a1wolfe/iMX6-BareBones/Kicad/3D Models/SOT583_MP2182_MNP.step

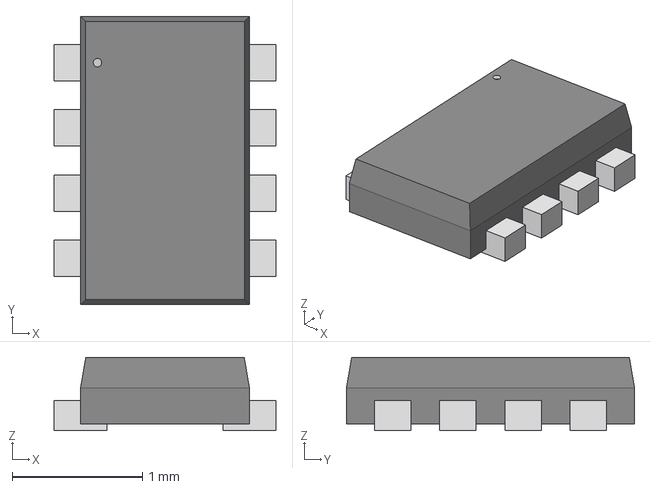
[picture p31: CAD file, 2026-04-11]
Kicad/3D Models/SOT583_MP2182_MNP.step
1.70 x 2.21 x 0.561 mm
