a1wolfe/iMX6-BareBones/Kicad/3D Models/P3V3_ind_74438322010.stp

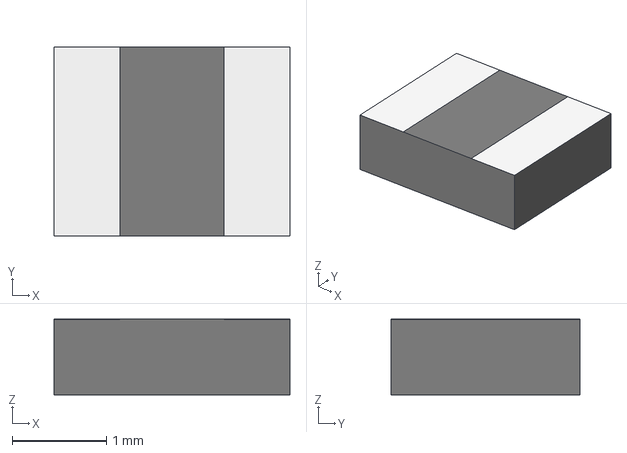
[picture p32: CAD file, 2026-04-11]
Kicad/3D Models/P3V3_ind_74438322010.stp
2.50 x 2.00 x 0.8 mm
