a1wolfe/iMX6-BareBones/Kicad/3D Models/5015.step

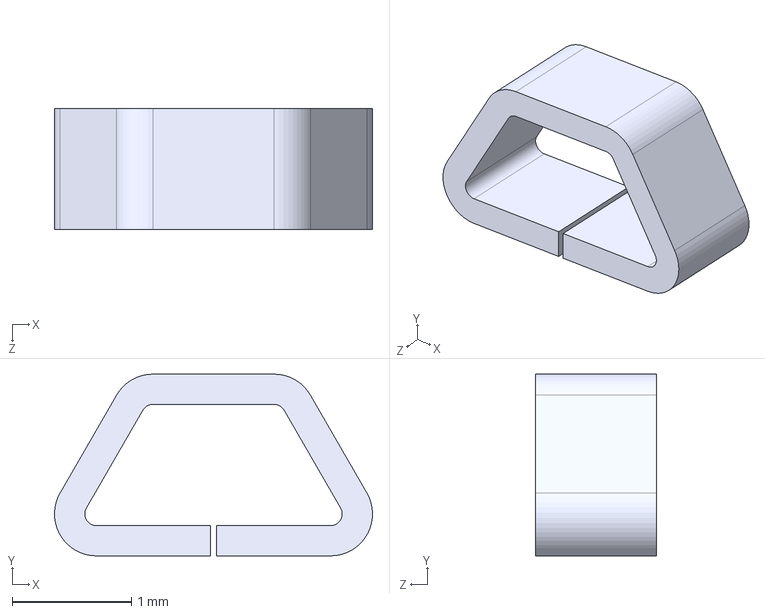
[picture p33: CAD file, 2026-04-11]
Kicad/3D Models/5015.step
2.67 x 1.52 x 1.02 mm
