a1wolfe/iMX6-BareBones/Kicad/3D Models/TPS3808E.stp

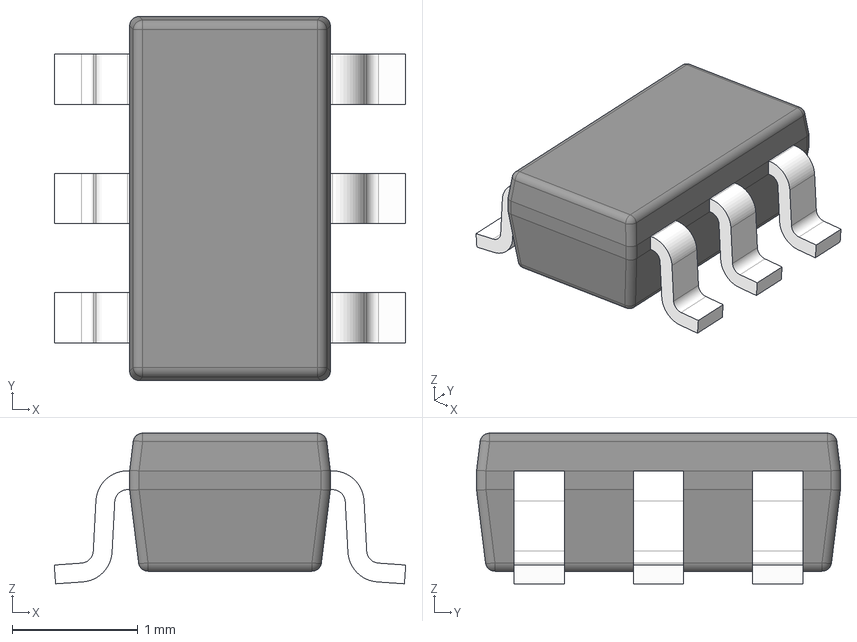
[picture p34: CAD file, 2026-04-11]
Kicad/3D Models/TPS3808E.stp
2.80 x 2.90 x 1.20 mm
BODY-SOT
LEAD-SOT x 6
