a1wolfe/iMX6-BareBones/Kicad/3D Models/PPPC042LFBN-RC.STEP

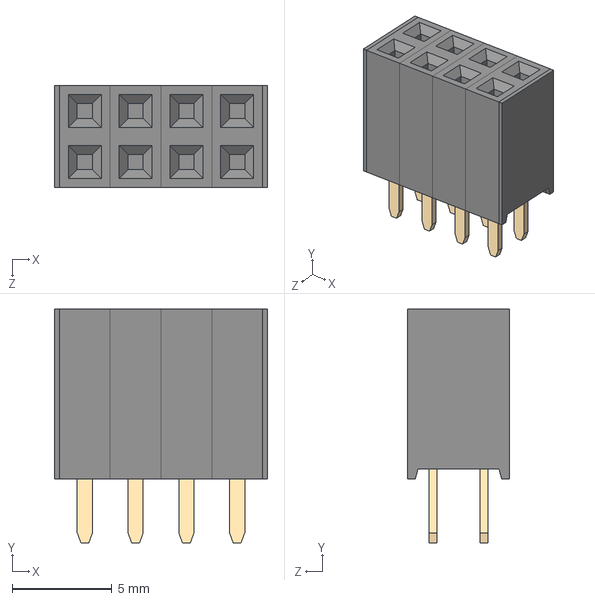
[picture p35: CAD file, 2026-04-11]
Kicad/3D Models/PPPC042LFBN-RC.STEP
10.7 x 11.7 x 5.08 mm
NPPC202LFBN-RC_C04
Pin - Gold x 4
