a1wolfe/iMX6-BareBones/Kicad/3D Models/QSPI-Flash_AT25SF321B-SSHB-T.stp

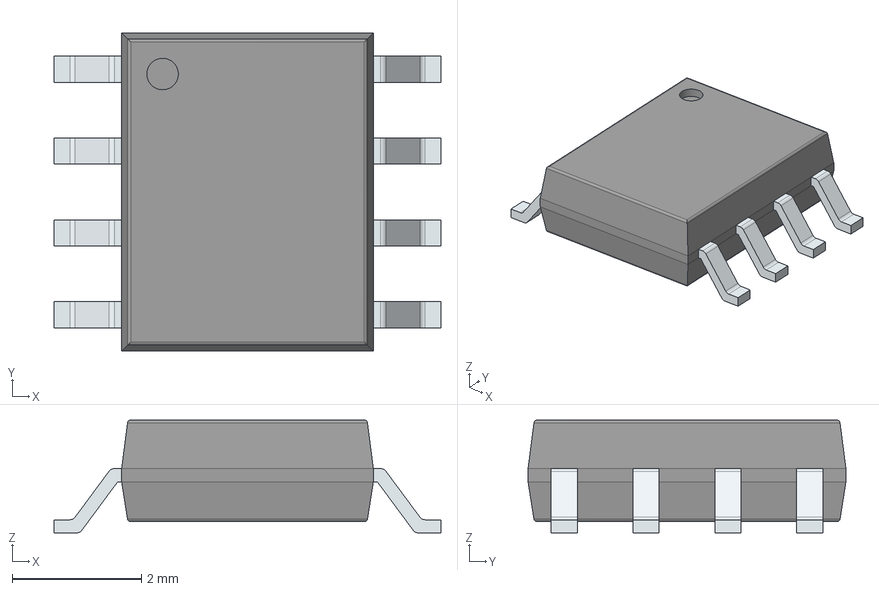
[picture p36: CAD file, 2026-04-11]
Kicad/3D Models/QSPI-Flash_AT25SF321B-SSHB-T.stp
6.00 x 4.92 x 1.75 mm
PinsArrayLR
