a1wolfe/iMX6-BareBones/Kicad/3D Models/_ _ _C122LFBN-RC.STEP

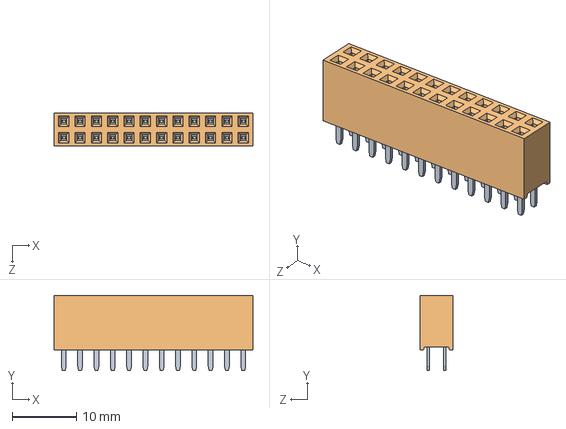
[picture p37: CAD file, 2026-04-11]
Kicad/3D Models/_ _ _C122LFBN-RC.STEP
31.0 x 11.7 x 5.08 mm
