a1wolfe/iMX6-BareBones/Kicad/3D Models/SP0503BAHTG.stp

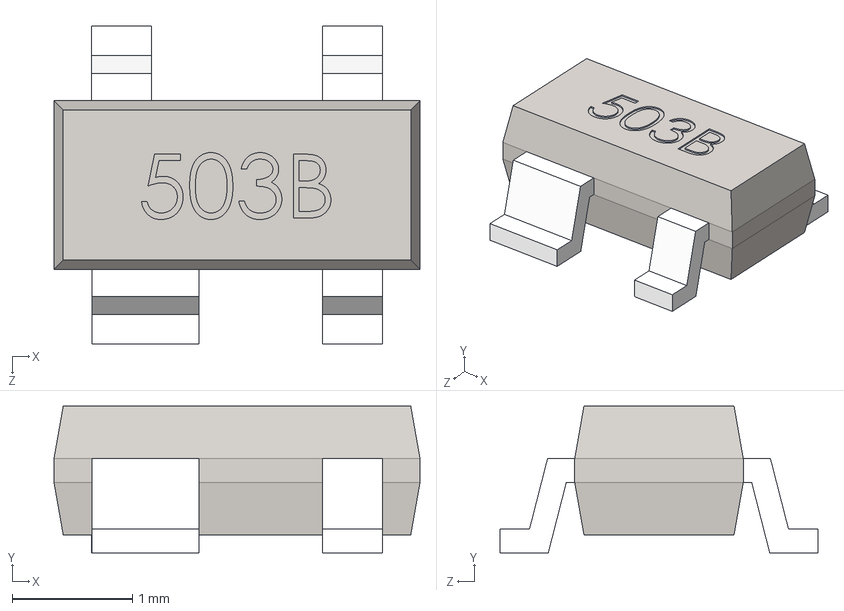
[picture p38: CAD file, 2026-04-11]
Kicad/3D Models/SP0503BAHTG.stp
3.04 x 1.22 x 2.64 mm
