a1wolfe/iMX6-BareBones/Kicad/3D Models/NCP380HMU05AATBG_LoadSwitch.stp

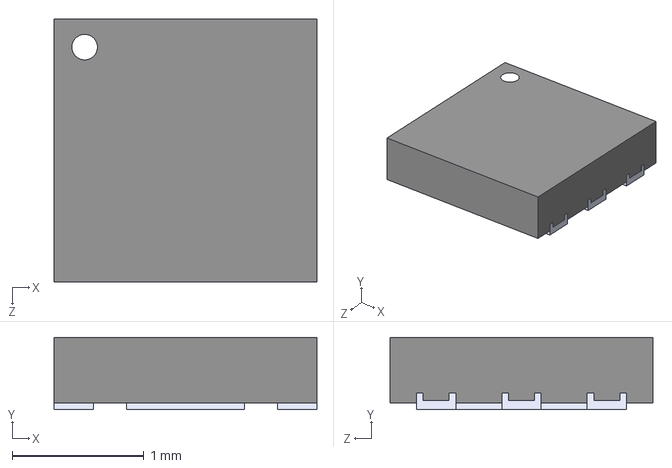
[picture p39: CAD file, 2026-04-11]
Kicad/3D Models/NCP380HMU05AATBG_LoadSwitch.stp
2.00 x 0.55 x 2.00 mm
