a1wolfe/iMX6-BareBones/Kicad/3D Models/MT41K256M16TW-107_P.step

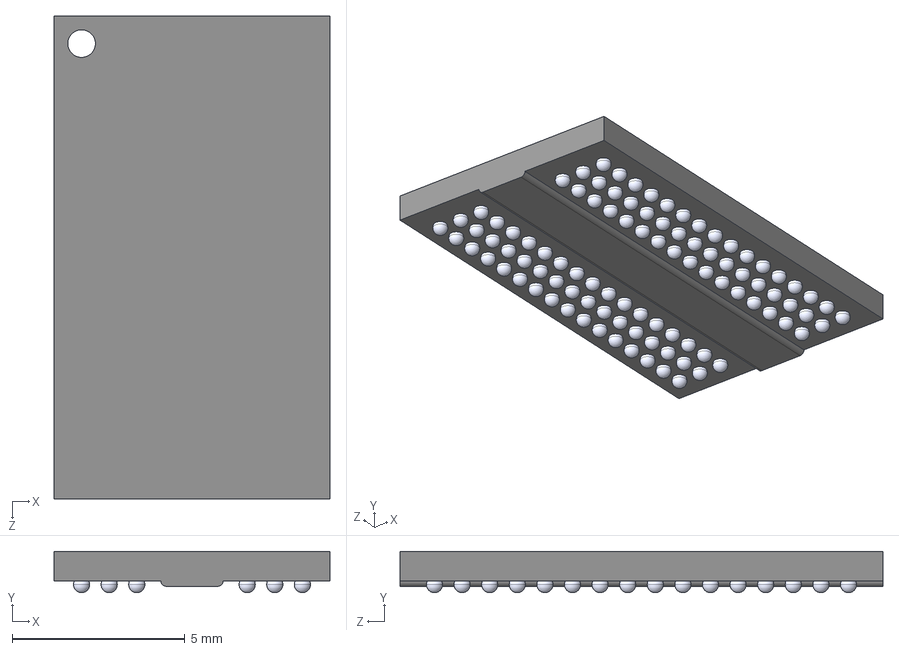
[picture p40: CAD file, 2026-04-11]
Kicad/3D Models/MT41K256M16TW-107_P.step
8.00 x 1.20 x 14.0 mm
