a1wolfe/iMX6-BareBones/Kicad/3D Models/TJA1042T_3.stp

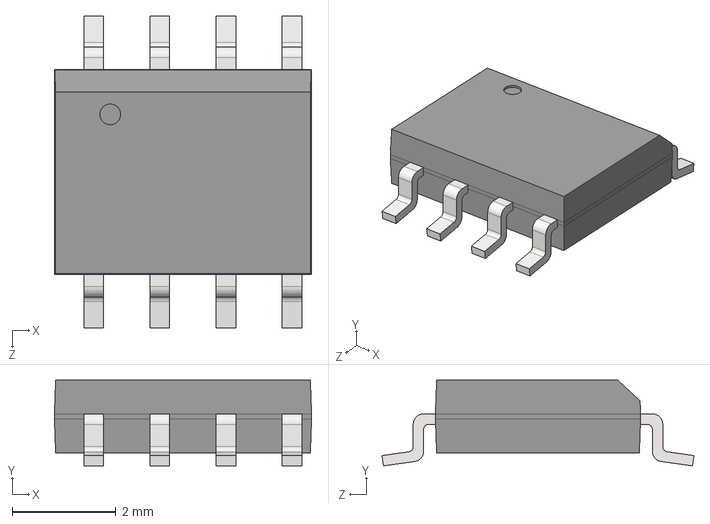
[picture p41: CAD file, 2026-04-11]
Kicad/3D Models/TJA1042T_3.stp
4.95 x 1.65 x 6.00 mm
