a1wolfe/iMX6-BareBones/Kicad/3D Models/APX803S-29SR-7.stp

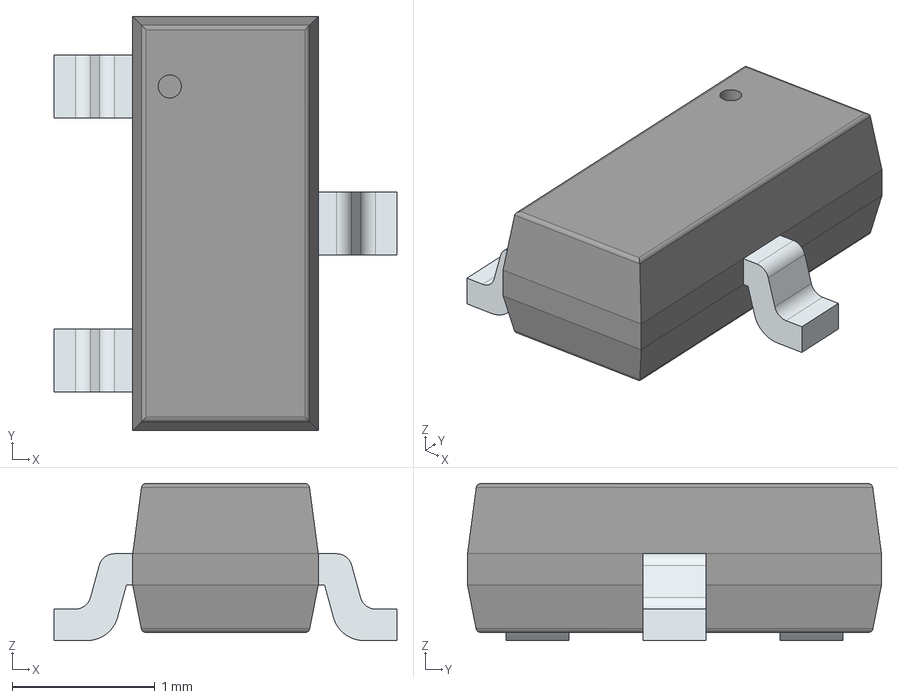
[picture p42: CAD file, 2026-04-11]
Kicad/3D Models/APX803S-29SR-7.stp
2.40 x 2.90 x 1.10 mm
PinsArrayL
FilletPinR
