a1wolfe/iMX6-BareBones/Kicad/3D Models/NX20P5090UK_awolfe.stp

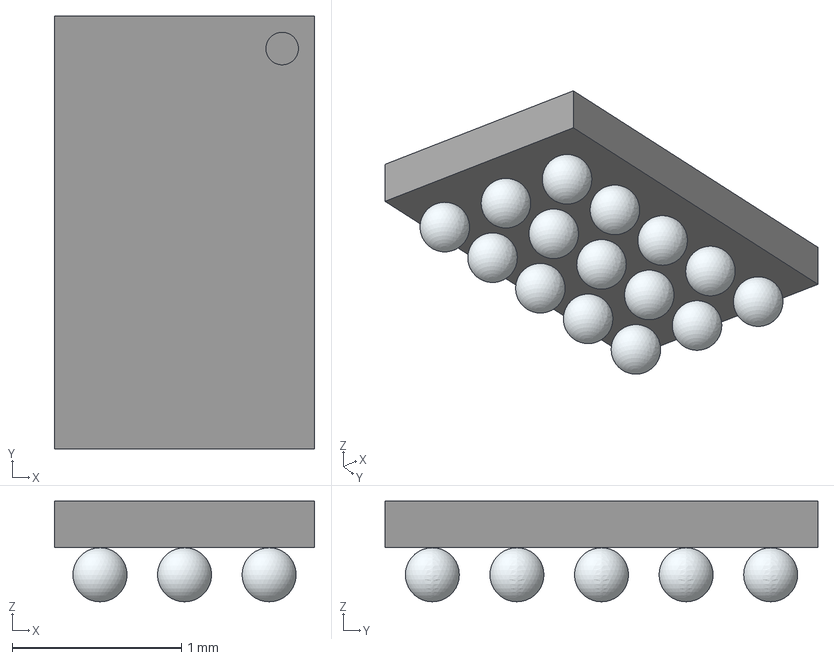
[picture p43: CAD file, 2026-04-11]
Kicad/3D Models/NX20P5090UK_awolfe.stp
1.54 x 2.56 x 0.595 mm
