a1wolfe/iMX6-BareBones/Kicad/3D Models/FC-135_32.7680KA-K0.stp

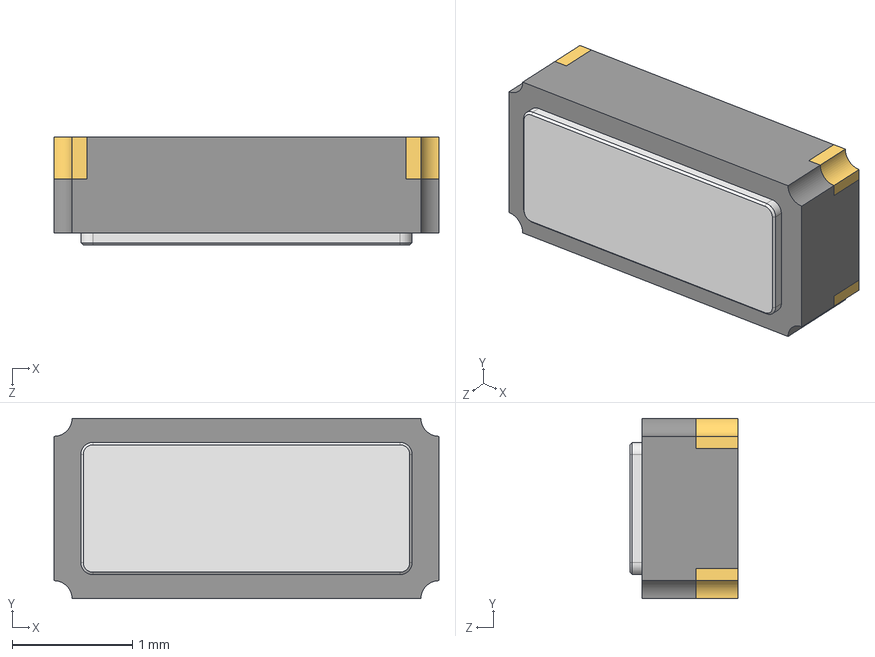
[picture p44: CAD file, 2026-04-11]
Kicad/3D Models/FC-135_32.7680KA-K0.stp
3.20 x 1.50 x 0.901 mm
