a1wolfe/iMX6-BareBones/Kicad/3D Models/MIC2025_MSOP-8_MM_MCH.step

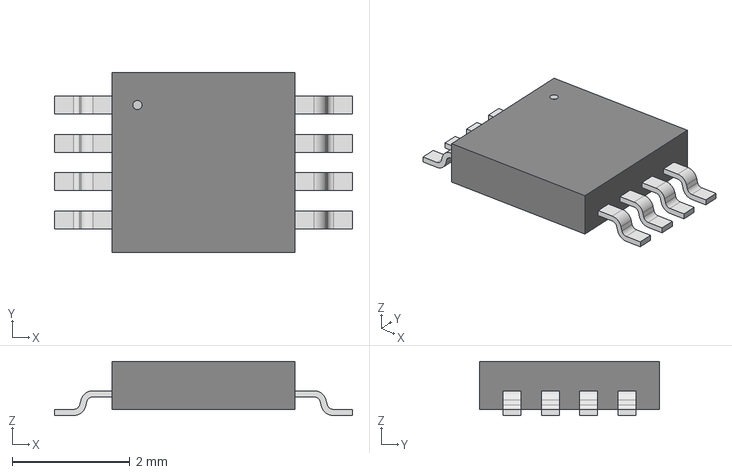
[picture p45: CAD file, 2026-04-11]
Kicad/3D Models/MIC2025_MSOP-8_MM_MCH.step
5.05 x 3.05 x 0.917 mm
