a1wolfe/iMX6-BareBones/Kicad/3D Models/eMMC_MX52LM04A11XSI.stp

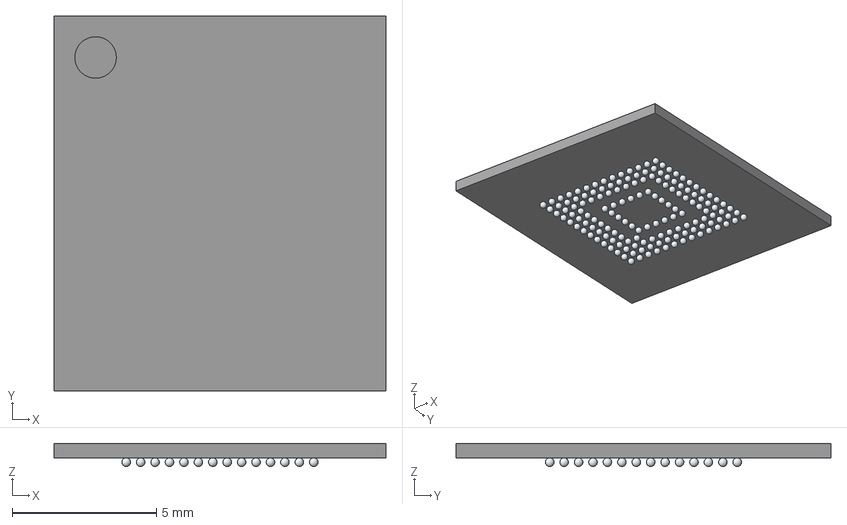
[picture p46: CAD file, 2026-04-11]
Kicad/3D Models/eMMC_MX52LM04A11XSI.stp
11.5 x 13.0 x 0.8 mm
A1
A2
A3
A4
A5
A6
A7
A8
A9
A10
A11
A12
A13
A14
B1
B2
B3
B4
B5
B6
B7
B8
B9
B10
B11
B12
B13
B14
C1
C2
C3
C4
C5
C6
C7
C8
C9
C10
C11
C12
C13
C14
D1
D2
D3
D4
D12
D13
D14
E1
E2
E3
E5
E6
E7
E8
E9
E10
E12
E13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
