a1wolfe/iMX6-BareBones/Kicad/3D Models/TLV773P_LDO_DBV0005A.stp

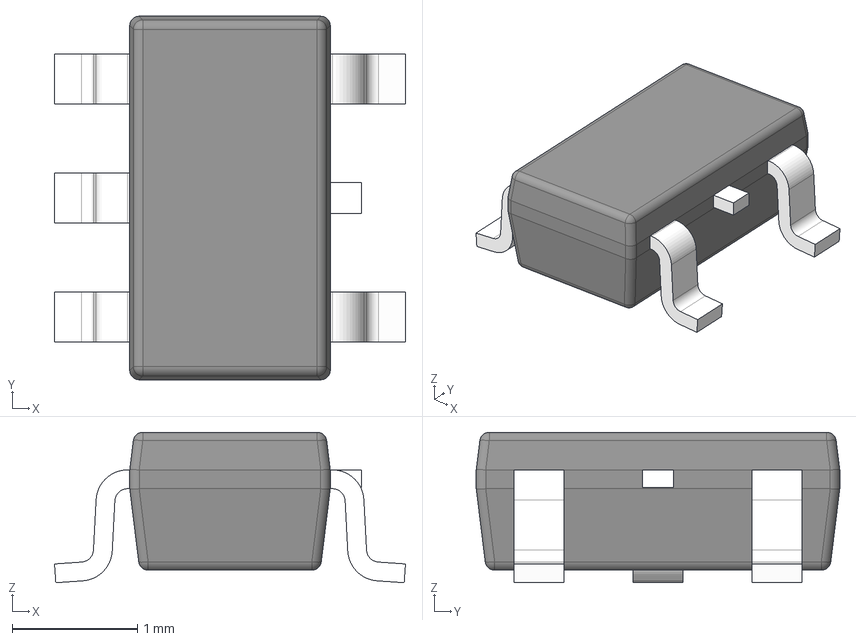
[picture p47: CAD file, 2026-04-11]
Kicad/3D Models/TLV773P_LDO_DBV0005A.stp
2.80 x 2.90 x 1.20 mm
BODY-SOT
LEAD-SOT x 5
LEAD-DUMMY
