a1wolfe/iMX6-BareBones/Kicad/3D Models/DualAnd_74LVC2G08GT_115.step

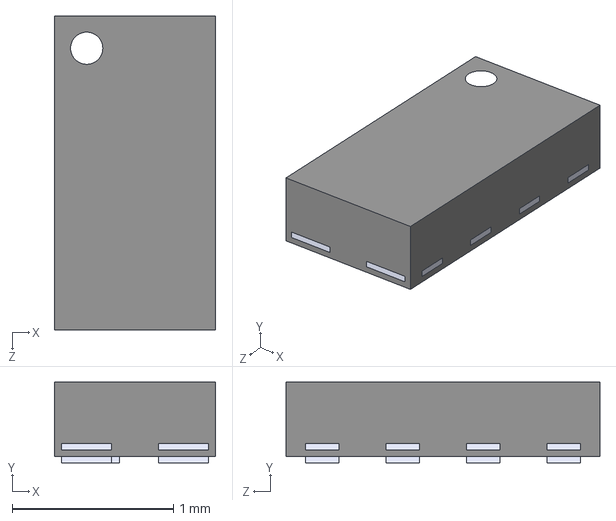
[picture p48: CAD file, 2026-04-11]
Kicad/3D Models/DualAnd_74LVC2G08GT_115.step
1.00 x 0.5 x 1.95 mm
