a1wolfe/iMX6-BareBones/Kicad/3D Models/USBArec_61400416021_rev1.stp

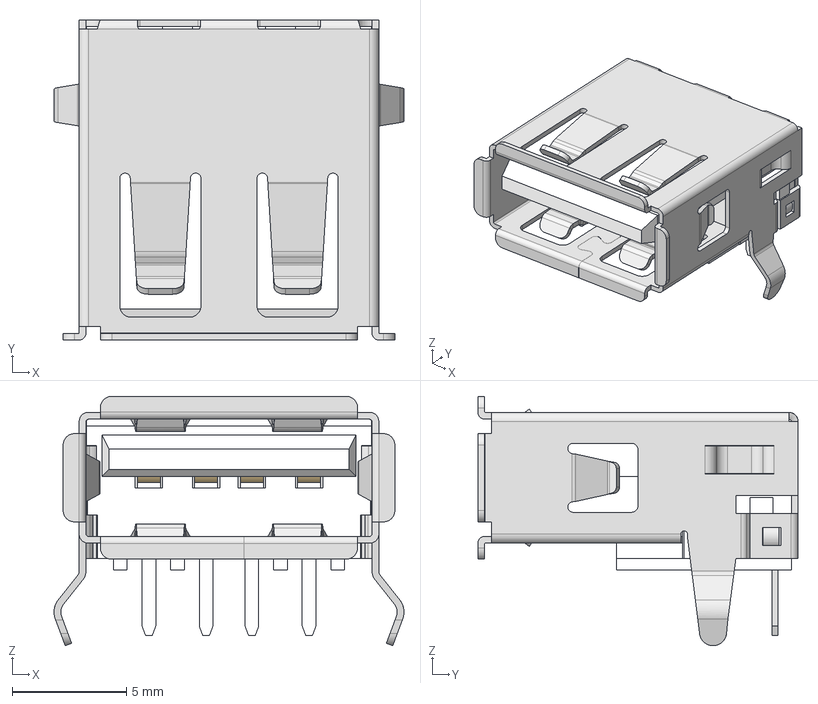
[picture p49: CAD file, 2026-04-11]
Kicad/3D Models/USBArec_61400416021_rev1.stp
15.3 x 14.0 x 10.9 mm
61400416021_Insulator
61400416021_Contact Plating x 4
61400416021_Shielding
