a1wolfe/iMX6-BareBones/Kicad/3D Models/LevelShift_DCU0008A.stp

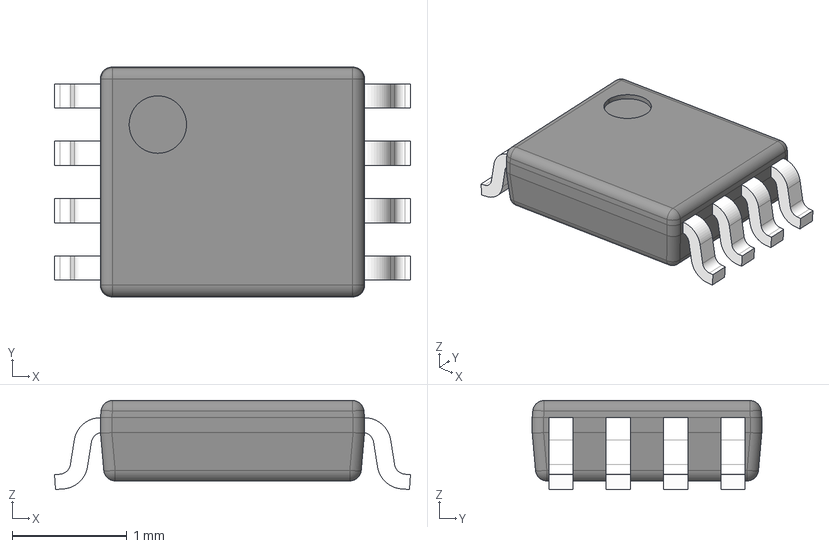
[picture p50: CAD file, 2026-04-11]
Kicad/3D Models/LevelShift_DCU0008A.stp
3.10 x 2.00 x 0.775 mm
BODY-VSSOP
LEAD-VSSOP x 8
