a1wolfe/iMX6-BareBones/Kicad/3D Models/218-4.STEP

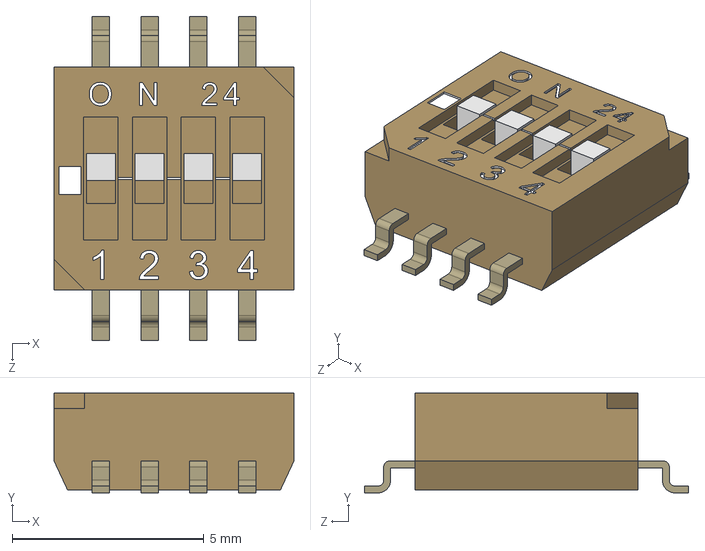
[picture p51: CAD file, 2026-04-11]
Kicad/3D Models/218-4.STEP
6.25 x 2.60 x 8.44 mm
