a1wolfe/iMX6-BareBones/Kicad/3D Models/DualNPN_MBT3904DW1T3G.stp

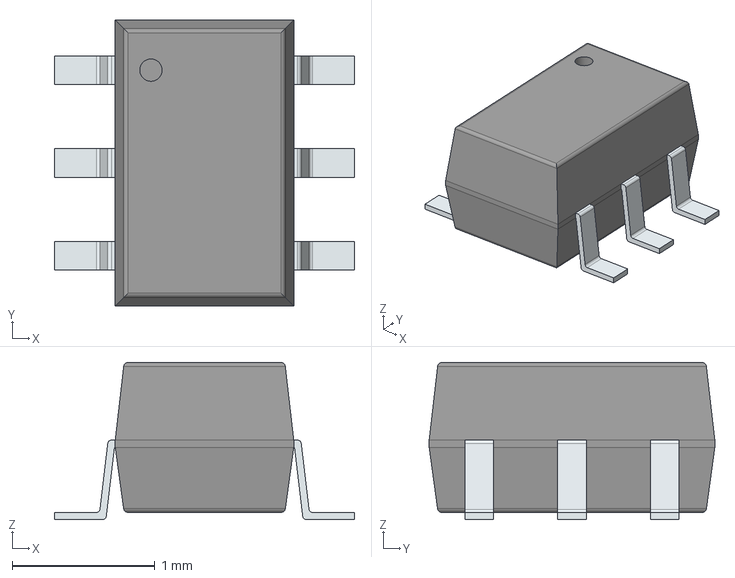
[picture p52: CAD file, 2026-04-11]
Kicad/3D Models/DualNPN_MBT3904DW1T3G.stp
2.10 x 2.00 x 1.10 mm
PinsArrayLR
