a1wolfe/iMX6-BareBones/Kicad/3D Models/USB-Tran_CP2102N-A02-GQFN20--3DModel-STEP-269445.STEP

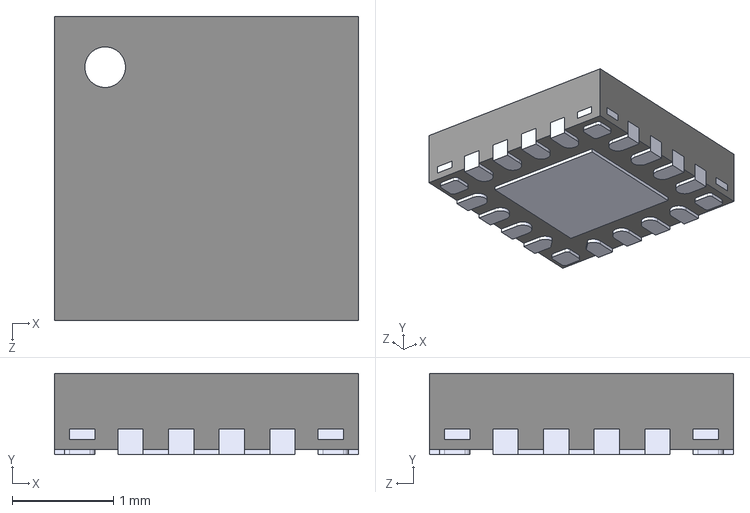
[picture p53: CAD file, 2026-04-11]
Kicad/3D Models/USB-Tran_CP2102N-A02-GQFN20--3DModel-STEP-269445.STEP
3.00 x 0.8 x 3.00 mm
