a1wolfe/iMX6-BareBones/Kicad/3D Models/PPPC102LFBN-RC.STEP

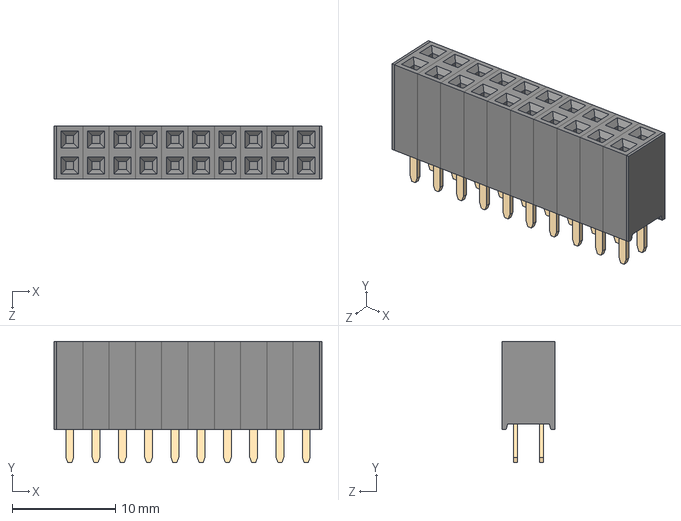
[picture p54: CAD file, 2026-04-11]
Kicad/3D Models/PPPC102LFBN-RC.STEP
25.9 x 11.7 x 5.08 mm
NPPC202LFBN-RC_C10
Pin - Gold x 10
