a1wolfe/iMX6-BareBones/Kicad/3D Models/WE-LHMI_4020+(rev1).stp

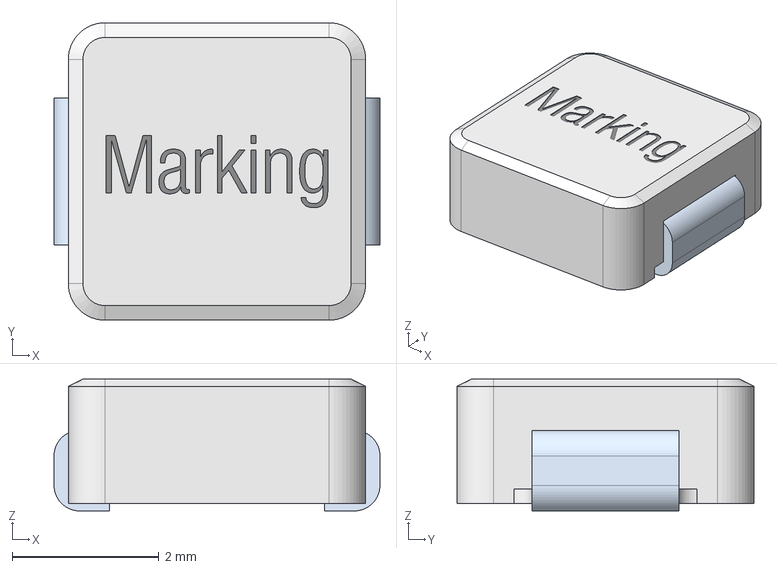
[picture p55: CAD file, 2026-04-11]
Kicad/3D Models/WE-LHMI_4020+(rev1).stp
4.45 x 4.06 x 1.80 mm
