a1wolfe/iMX6-BareBones/Kicad/3D Models/DLW43SH510XK2K--3DModel-STEP-1.STEP

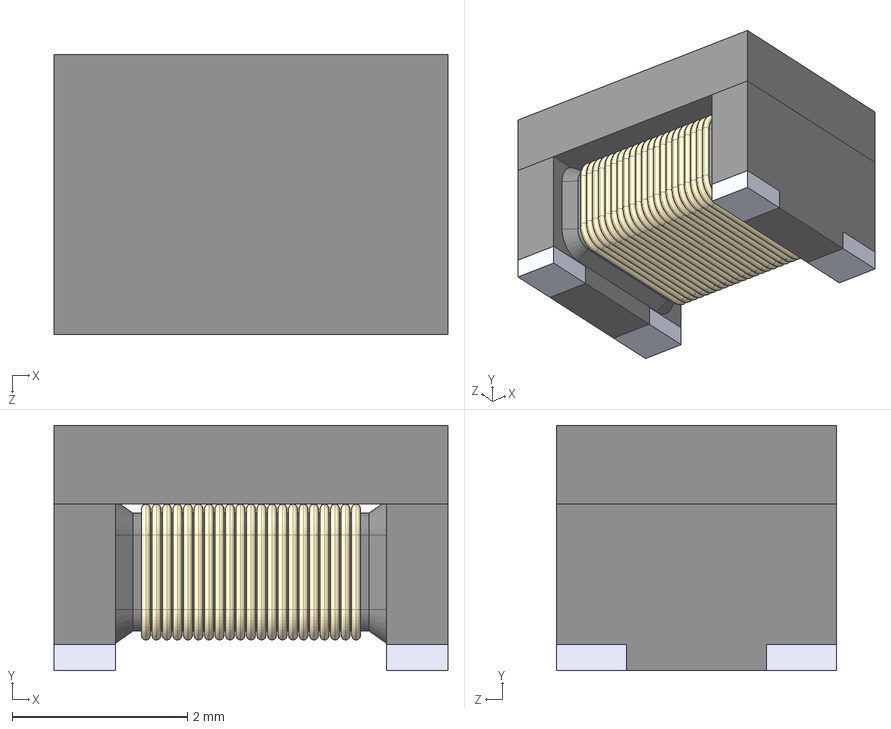
[picture p56: CAD file, 2026-04-11]
Kicad/3D Models/DLW43SH510XK2K--3DModel-STEP-1.STEP
4.50 x 2.80 x 3.20 mm
