a1wolfe/iMX6-BareBones/Kicad/3D Models/AP3401KTTR-G1.stp

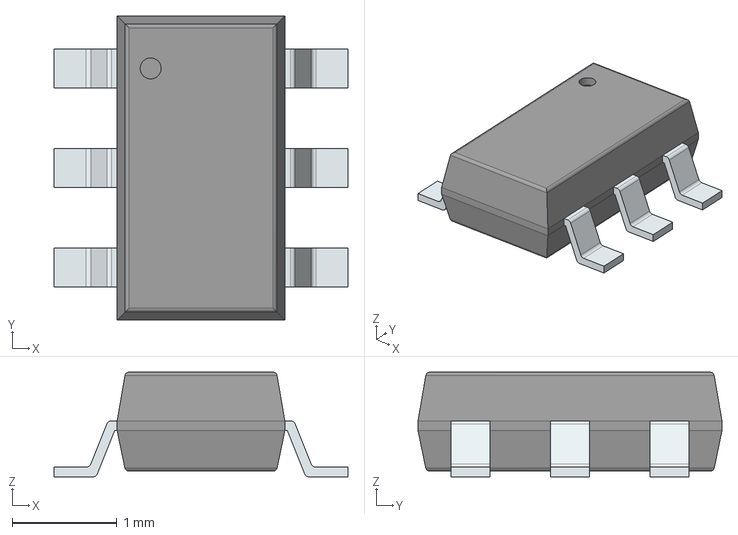
[picture p57: CAD file, 2026-04-11]
Kicad/3D Models/AP3401KTTR-G1.stp
2.80 x 2.90 x 1.00 mm
PinsArrayLR
