a1wolfe/iMX6-BareBones/Kicad/3D Models/sf-1206s-series.stp

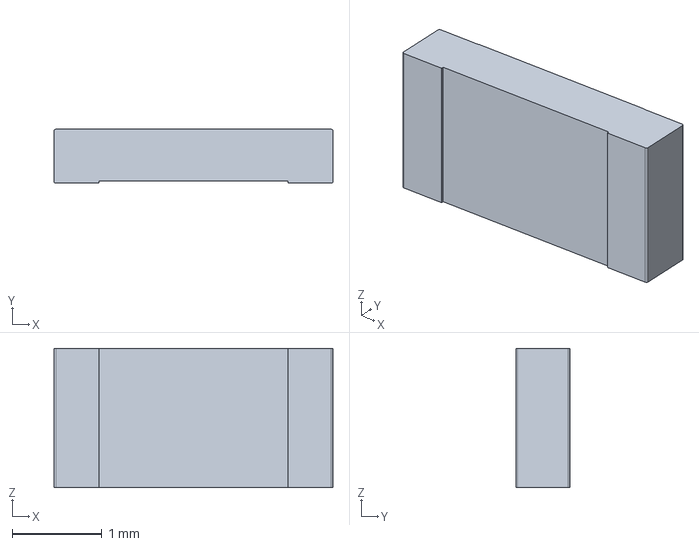
[picture p58: CAD file, 2026-04-11]
Kicad/3D Models/sf-1206s-series.stp
3.10 x 0.605 x 1.55 mm
