a1wolfe/iMX6-BareBones/Kicad/3D Models/DRL0006A_buck.stp

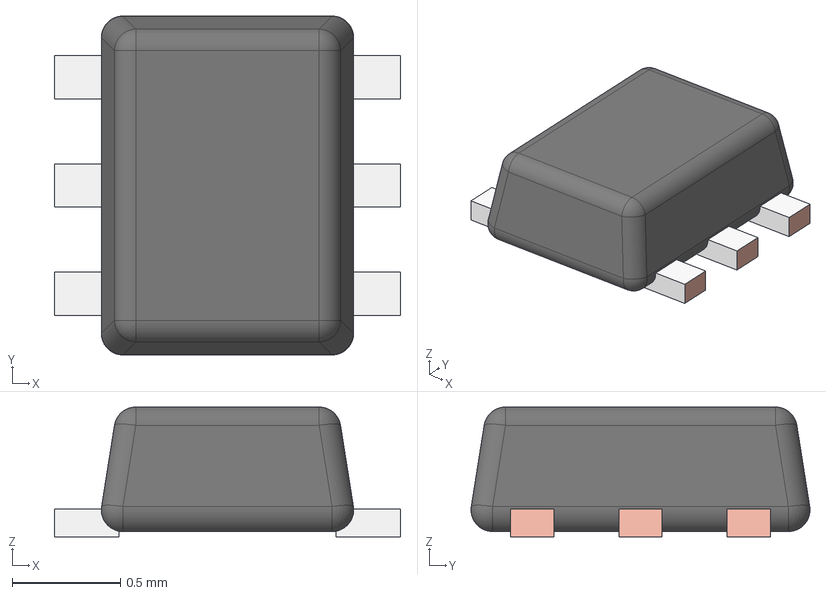
[picture p59: CAD file, 2026-04-11]
Kicad/3D Models/DRL0006A_buck.stp
1.60 x 1.57 x 0.6 mm
FRAME-DRL0006A
BODY-SOT
PIN1-ID
