a1wolfe/iMX6-BareBones/Kicad/3D Models/Kingbright_dualLED.step

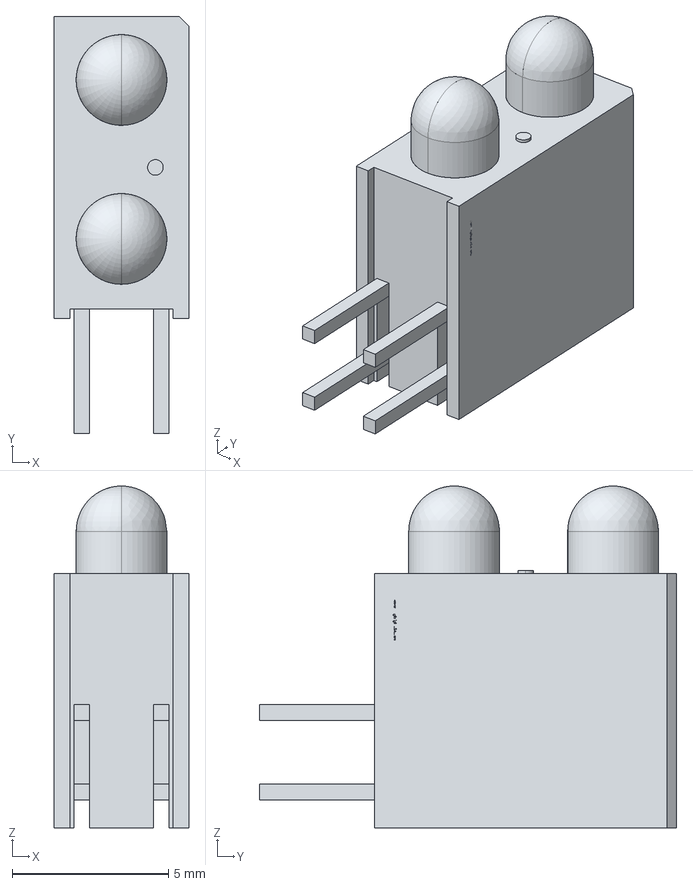
[picture p60: CAD file, 2026-04-11]
Kicad/3D Models/Kingbright_dualLED.step
4.30 x 13.3 x 10.9 mm
