a1wolfe/iMX6-BareBones/Kicad/BootMode.kicad_sch

## KiCad design Kicad/BootMode.kicad_sch (2026-04-23)

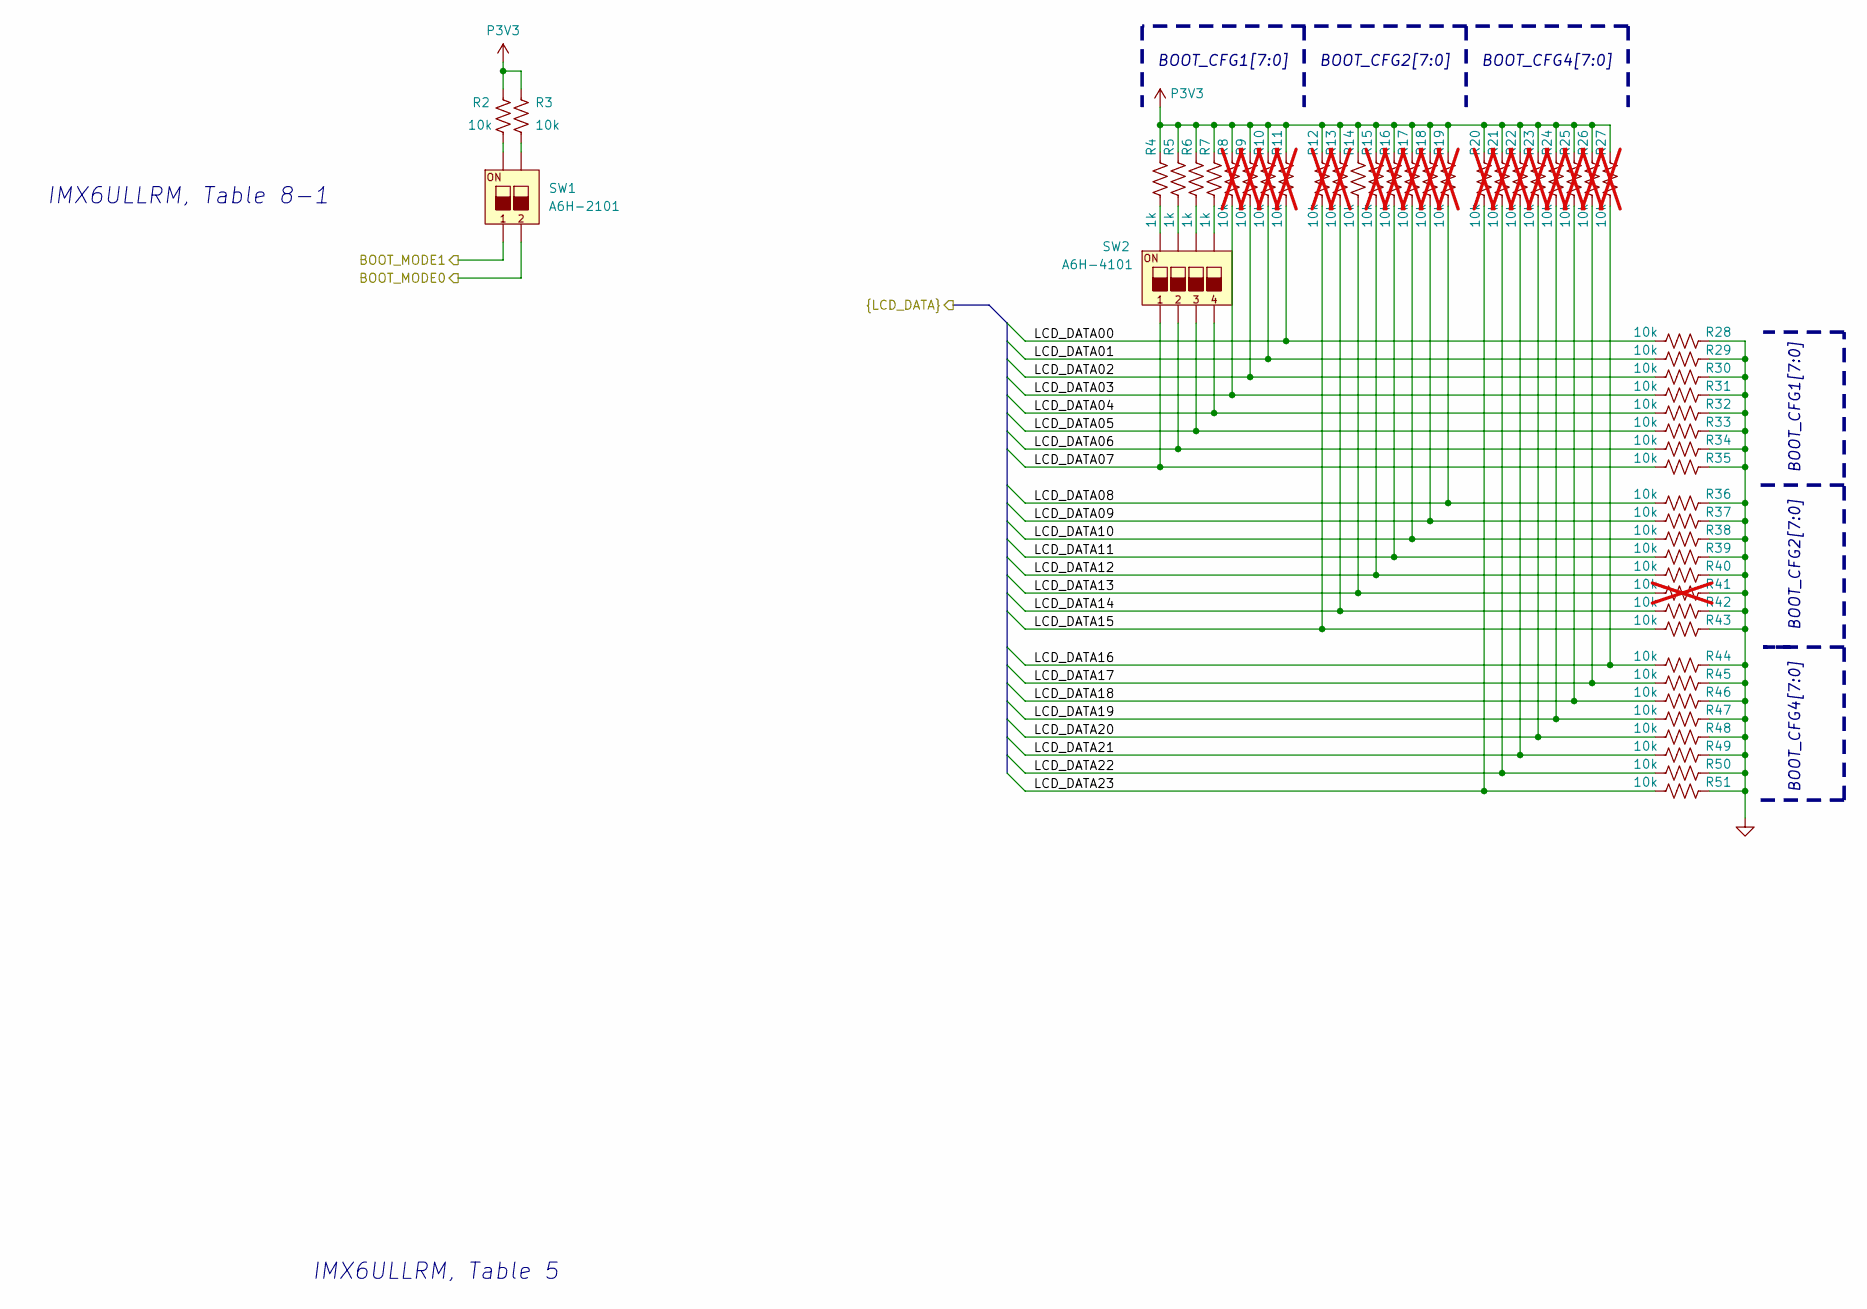
[picture p63: schematic BootMode.kicad_sch]

Parts:
R2, R3, R14, R28, R29, R30, R31, R32, R33, R34, R35, R36, R37, R38, R39, R40, R42, R43, R44, R45, R46, R47, R48, R49, R50, R51: 10k; R_0402_1005Metric; Tolerance 1%; MPN RC0402FR-7W10KL
R4, R5, R6, R7: 1k; R_0402_1005Metric; Tolerance 1%; MPN RC0402FR-7W1KL
R8, R9, R10, R11, R12, R13, R15, R16, R17, R18, R19, R20, R21, R22, R23, R24, R25, R26, R27, R41: 10k; R_0402_1005Metric; Tolerance 1%; MPN RC0402FR-7W10KL; not fitted
SW1: A6H-2101; SW_DIP_SPSTx02_Slide_Omron_A6H-2101_W6.15mm_P1.27mm; MPN A6H-2101
SW2: A6H-4101; SW_DIP_SPSTx04_Slide_Omron_A6H-4101_W6.15mm_P1.27mm; MPN A6H-4101

Connections:
BOOT_MODE0: SW1.2
BOOT_MODE1: SW1.1
GND: R28.1, R29.1, R30.1, R31.1, R32.1, R33.1, R34.1, R35.1, R36.1, R37.1, R38.1, R39.1, R40.1, R41.1, R42.1, R43.1, R44.1, R45.1, R46.1, R47.1, R48.1, R49.1, R50.1, R51.1
LCD_DATA00: R11.2, R28.2
LCD_DATA01: R10.2, R29.2
LCD_DATA02: R9.2, R30.2
LCD_DATA03: R8.2, R31.2
LCD_DATA04: R32.2, SW2.5
LCD_DATA05: R33.2, SW2.6
LCD_DATA06: R34.2, SW2.7
LCD_DATA07: R35.2, SW2.8
LCD_DATA08: R19.2, R36.2
LCD_DATA09: R18.2, R37.2
LCD_DATA10: R17.2, R38.2
LCD_DATA11: R16.2, R39.2
LCD_DATA12: R15.2, R40.2
LCD_DATA13: R14.2, R41.2
LCD_DATA14: R13.2, R42.2
LCD_DATA15: R12.2, R43.2
LCD_DATA16: R27.2, R44.2
LCD_DATA17: R26.2, R45.2
LCD_DATA18: R25.2, R46.2
LCD_DATA19: R24.2, R47.2
LCD_DATA20: R23.2, R48.2
LCD_DATA21: R22.2, R49.2
LCD_DATA22: R21.2, R50.2
LCD_DATA23: R20.2, R51.2
unnamed: R2.2, SW1.4
unnamed: R3.2, SW1.3
unnamed: R4.2, SW2.1
unnamed: R5.2, SW2.2
unnamed: R6.2, SW2.3
unnamed: R7.2, SW2.4
P3V3: R2.1, R3.1, R4.1, R5.1, R6.1, R7.1, R8.1, R9.1, R10.1, R11.1, R12.1, R13.1, R14.1, R15.1, R16.1, R17.1, R18.1, R19.1, R20.1, R21.1, R22.1, R23.1, R24.1, R25.1, R26.1, R27.1

Notes on the sheet:
BOOT_CFG2[7:0]
IMX6ULLRM, Table 8-1
BOOT_CFG4[7:0]
BOOT_CFG1[7:0]
IMX6ULLRM, Table 5
