a1wolfe/iMX6-BareBones/Kicad/CAN.kicad_sch

## KiCad design Kicad/CAN.kicad_sch (2026-04-23)

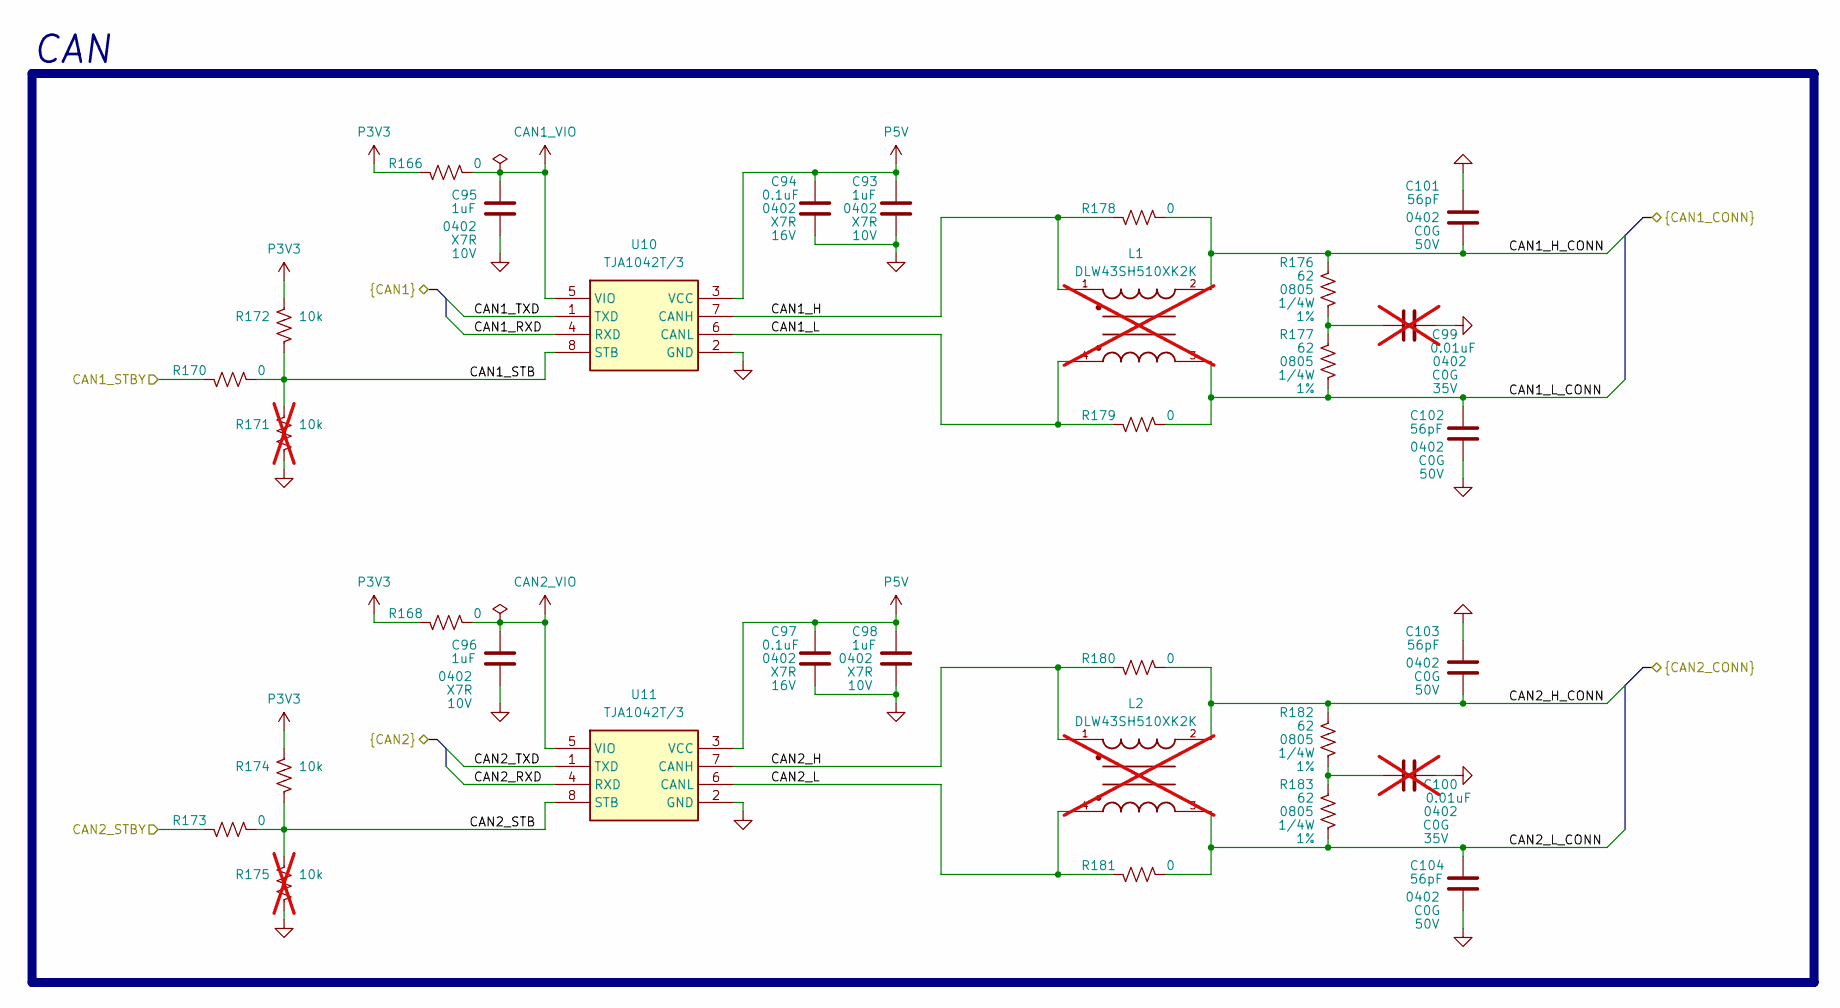
[picture p64: schematic CAN.kicad_sch]

Parts:
C93, C95, C96, C98: 1uF; C_0402_1005Metric; Tolerance 10%; Voltage 10V; MPN GRM155Z71A105KE01
C94, C97: 0.1uF; C_0402_1005Metric; Tolerance 10%; Voltage 16V; MPN GRM155R71C104KA88
C99, C100: 0.01uF; C_0402_1005Metric; Tolerance 2%; Voltage 35V; MPN GRM1555CYA103GE01; not fitted
C101, C102, C103, C104: 56pF; C_0402_1005Metric; Tolerance 5%; Voltage 50V; MPN GRM1555C1H560JA01
L1, L2: DLW43SH510XK2K; FIL_DLW43SH510XK2K; MPN DLW43SH510XK2K; not fitted
R166, R168, R170, R173, R178, R179, R180, R181: 0; R_0402_1005Metric; Tolerance Jumper; MPN RC0402JR-070RL
R171, R175: 10k; R_0402_1005Metric; Tolerance 1%; MPN RC0402FR-7W10KL; not fitted
R172, R174: 10k; R_0402_1005Metric; Tolerance 1%; MPN RC0402FR-7W10KL
R176, R177, R182, R183: 62; R_0805_2012Metric; Tolerance 1%; MPN RK73H2ATTD62R0F
U10, U11: TJA1042T/3; TJA1042T_SOIC127P600X175-8N; Manufacturer_Part_Number TJA1042T/3; Mouser Part Number N/A

Connections:
CAN1_H: L1.1, R178.1, U10.7 (CANH)
CAN1_H_CONN: C101.1, L1.2, R176.2, R178.2
CAN1_L: L1.4, R179.1, U10.6 (CANL)
CAN1_L_CONN: C102.1, L1.3, R177.1, R179.2
CAN1_RXD: U10.4 (RXD)
CAN1_STB: R170.2, R171.2, R172.1, U10.8 (STB)
CAN1_STBY: R170.1
CAN1_TXD: U10.1 (TXD)
CAN1_VIO: C95.1, R166.2, U10.5 (VIO)
CAN2_H: L2.1, R180.1, U11.7 (CANH)
CAN2_H_CONN: C103.1, L2.2, R180.2, R182.2
CAN2_L: L2.4, R181.1, U11.6 (CANL)
CAN2_L_CONN: C104.1, L2.3, R181.2, R183.1
CAN2_RXD: U11.4 (RXD)
CAN2_STB: R173.2, R174.1, R175.2, U11.8 (STB)
CAN2_STBY: R173.1
CAN2_TXD: U11.1 (TXD)
CAN2_VIO: C96.1, R168.2, U11.5 (VIO)
GND: C93.2, C94.2, C95.2, C96.2, C97.2, C98.2, C99.2, C100.2, C101.2, C102.2, C103.2, C104.2, R171.1, R175.1, U10.2 (GND), U11.2 (GND)
unnamed: C99.1, R176.1, R177.2
unnamed: C100.1, R182.1, R183.2
P3V3: R166.1, R168.1, R172.2, R174.2
P5V: C93.1, C94.1, C97.1, C98.1, U10.3 (VCC), U11.3 (VCC)

Notes on the sheet:
CAN
