a1wolfe/iMX6-BareBones/Kicad/Connectors.kicad_sch

## KiCad design Kicad/Connectors.kicad_sch (2026-04-23)

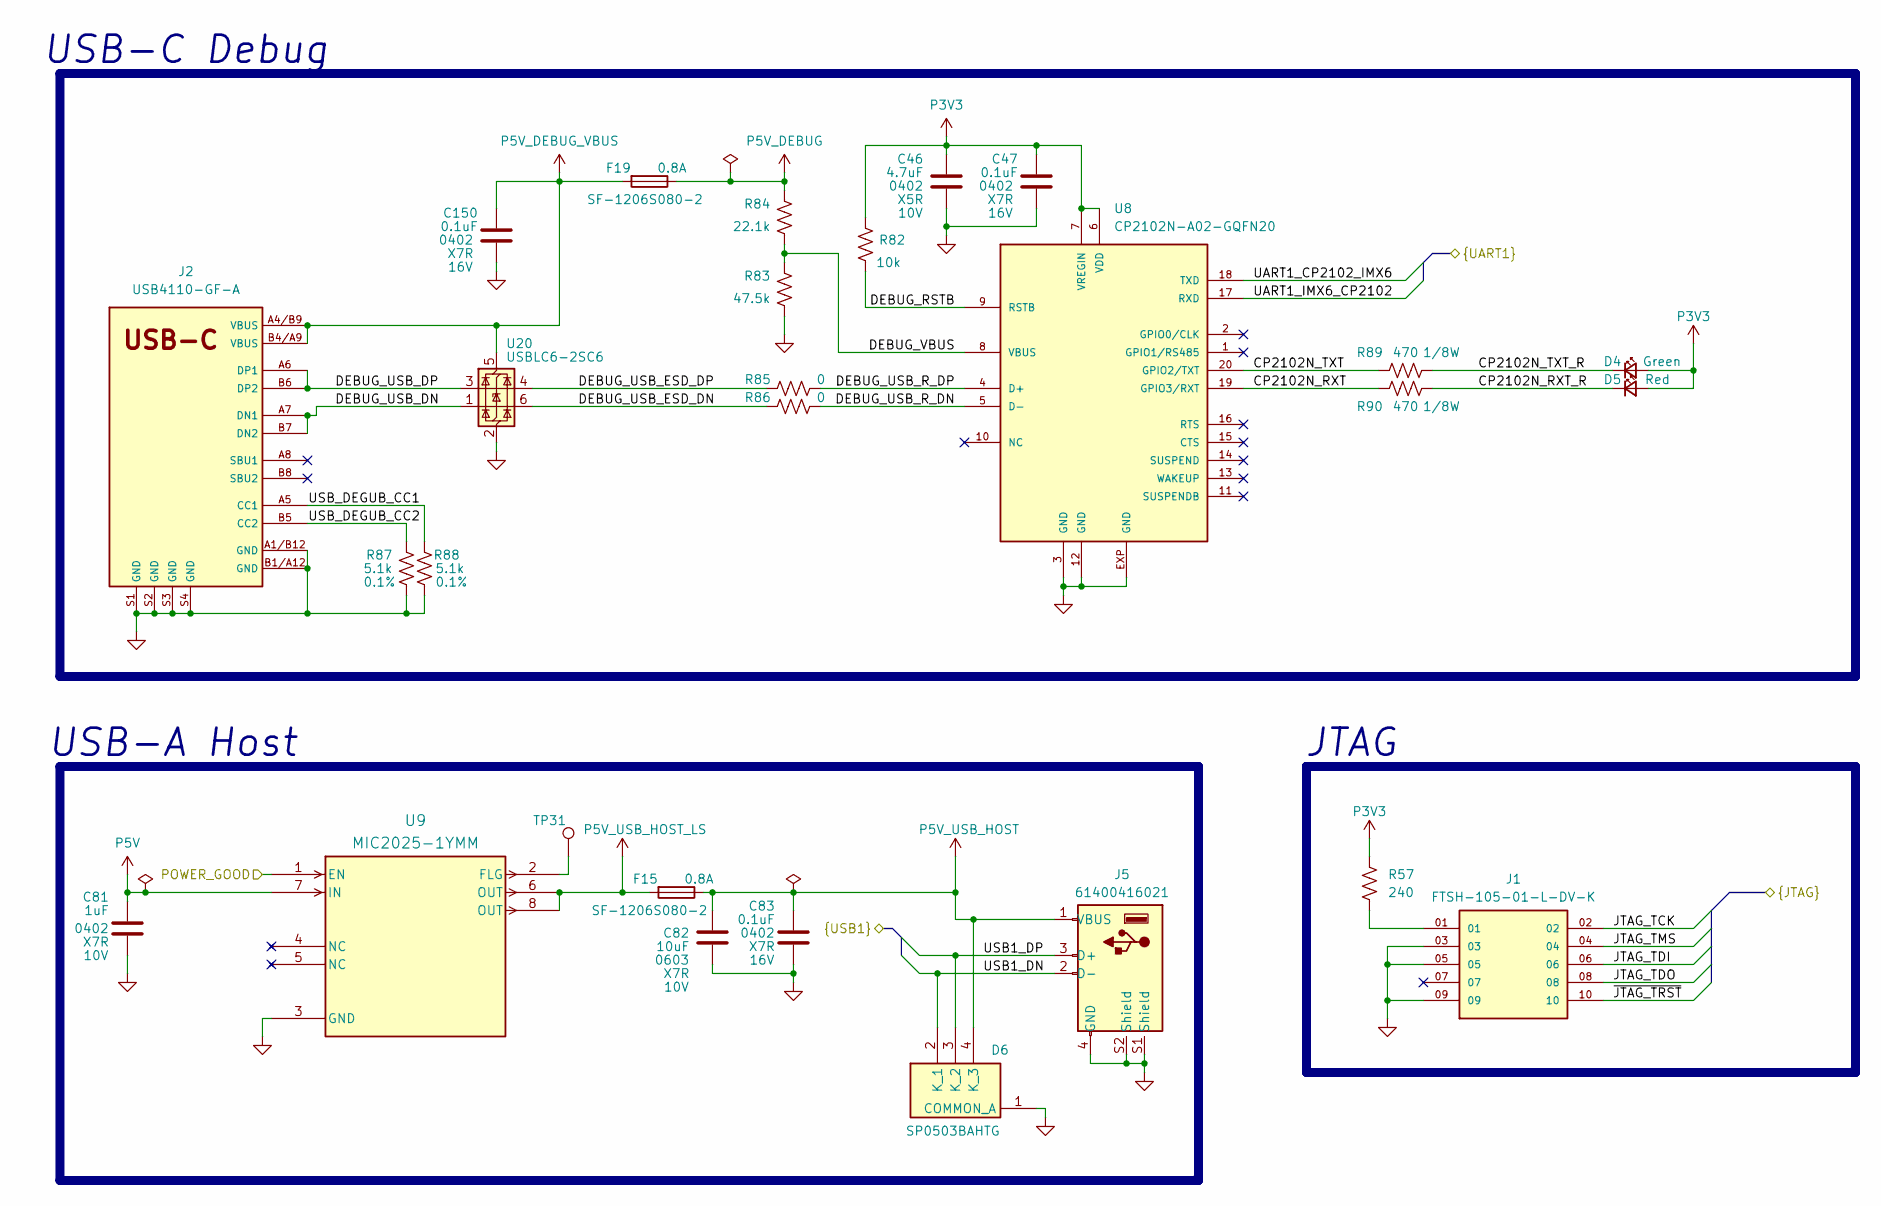
[picture p65: schematic Connectors.kicad_sch]

Parts:
C46: 4.7uF; C_0402_1005Metric; Tolerance 20%; Voltage 10V; MPN GRM155R61A475MEA
C47, C83, C150: 0.1uF; C_0402_1005Metric; Tolerance 10%; Voltage 16V; MPN GRM155R71C104KA88
C81: 1uF; C_0402_1005Metric; Tolerance 10%; Voltage 10V; MPN GRM155Z71A105KE01
C82: 10uF; C_0603_1608Metric; Tolerance 10%; Voltage 10V; MPN GRM188Z71A106KA73
D4: LTST-C170GKT; LED_0805_2012Metric; MPN LTST-C170GKT
D5: LTST-C170KRKT; LED_0805_2012Metric; MPN LTST-C170KRKT
D6: SP0503BAHTG; Manufacturer_Part_Number SP0503BAHTG; Mouser Part Number 576-SP0503BAHTG
F15, F19: SF-1206S080-2; Fuse_1206_3216Metric; Current Rating 0.8A; MPN SF-1206S080-2
J1: FTSH-105-01-L-DV-K; SAMTEC_FTSH-105-XX-X-DV; PARTREV H
J2: USB4110-GF-A; GCT_USB4110GFA; MPN USB4110-GF-A
J5: 61400416021; USBArec_61400416021; MPN 61400416021
R57: 240; R_0402_1005Metric; Tolerance 0.1%; MPN RT0402BRD07240RL
R82: 10k; R_0402_1005Metric; Tolerance 1%; MPN RC0402FR-7W10KL
R83: 47.5k; R_0402_1005Metric; Tolerance 1%; MPN RC0402FR-0747K5L
R84: 22.1k; R_0402_1005Metric; Tolerance 1%; MPN RC0402FR-0722K1L
R85, R86: 0; R_0402_1005Metric; Tolerance Jumper; MPN RC0402JR-070RL
R87, R88: 5.1k; R_0402_1005Metric; Tolerance 0.1%; MPN RT0402BRD075K1L
R89, R90: 470; R_0402_1005Metric; Tolerance 1%; MPN RCC0402470RFKED
TP31: TestPoint; TestPoint_Pad_D30mil
U8: CP2102N-A02-GQFN20; CP2102N_WFQFN-20; MPN CP2102N-A02-GQFN20
U9: MIC2025-1YMM; MIC2025_MSOP-8_MM_MCH; MPN MIC2025-1YMM
U20: USBLC6-2SC6

Connections:
CP2102N_RXT: R90.2, U8.19 (GPIO3/RXT)
CP2102N_RXT_R: D5.1 (K), R90.1
CP2102N_TXT: R89.2, U8.20 (GPIO2/TXT)
CP2102N_TXT_R: D4.1 (K), R89.1
DEBUG_RSTB: R82.1, U8.9 (RSTB)
DEBUG_USB_DN: J2.A7 (DN1), J2.B7 (DN2), U20.1 (I/O2)
DEBUG_USB_DP: J2.A6 (DP1), J2.B6 (DP2), U20.3 (I/O1)
DEBUG_USB_ESD_DN: R86.2, U20.6 (I/O2)
DEBUG_USB_ESD_DP: R85.2, U20.4 (I/O1)
DEBUG_USB_R_DN: R86.1, U8.5 (D-)
DEBUG_USB_R_DP: R85.1, U8.4 (D+)
DEBUG_VBUS: R83.2, R84.1, U8.8 (VBUS)
GND: C46.1, C47.1, C81.1, C82.1, C83.1, C150.1, D6.1 (COMMON_A), J1.03, J1.05, J1.09, J2.A1/B12 (GND), J2.B1/A12 (GND), J2.S1 (GND), J2.S2 (GND), J2.S3 (GND), J2.S4 (GND), J5.4 (GND), J5.S1 (Shield), J5.S2 (Shield), R83.1, R87.1, R88.1, U8.3 (GND), U8.12 (GND), U8.EXP (GND), U9.3 (GND), U20.2 (GND)
JTAG_TCK: J1.02
JTAG_TDI: J1.06
JTAG_TDO: J1.08
JTAG_TMS: J1.04
unnamed: J1.01, R57.2
unnamed: TP31.1, U9.2 (FLG)
P3V3: C46.2, C47.2, D4.2 (A), D5.2 (A), R57.1, R82.2, U8.6 (VDD), U8.7 (VREGIN)
P5V: C81.2, U9.7 (IN)
P5V_DEBUG: F19.1, R84.2
P5V_DEBUG_VBUS: C150.2, F19.2, J2.A4/B9 (VBUS), J2.B4/A9 (VBUS), U20.5 (VBUS)
P5V_USB_HOST: C82.2, C83.2, D6.4 (K_3), F15.1, J5.1 (VBUS)
P5V_USB_HOST_LS: F15.2, U9.6 (OUT), U9.8 (OUT)
POWER_GOOD: U9.1 (EN)
UART1_CP2102_IMX6: U8.18 (TXD)
UART1_IMX6_CP2102: U8.17 (RXD)
USB1_DN: D6.2 (K_1), J5.2 (D-)
USB1_DP: D6.3 (K_2), J5.3 (D+)
USB_DEGUB_CC1: J2.A5 (CC1), R88.2
USB_DEGUB_CC2: J2.B5 (CC2), R87.2
~JTAG_TRST: J1.10

Notes on the sheet:
USB-A Host
USB-C Debug
JTAG
