a1wolfe/iMX6-BareBones/Kicad/DRAM_DDR3L.kicad_sch

## KiCad design Kicad/DRAM_DDR3L.kicad_sch (2026-04-23)

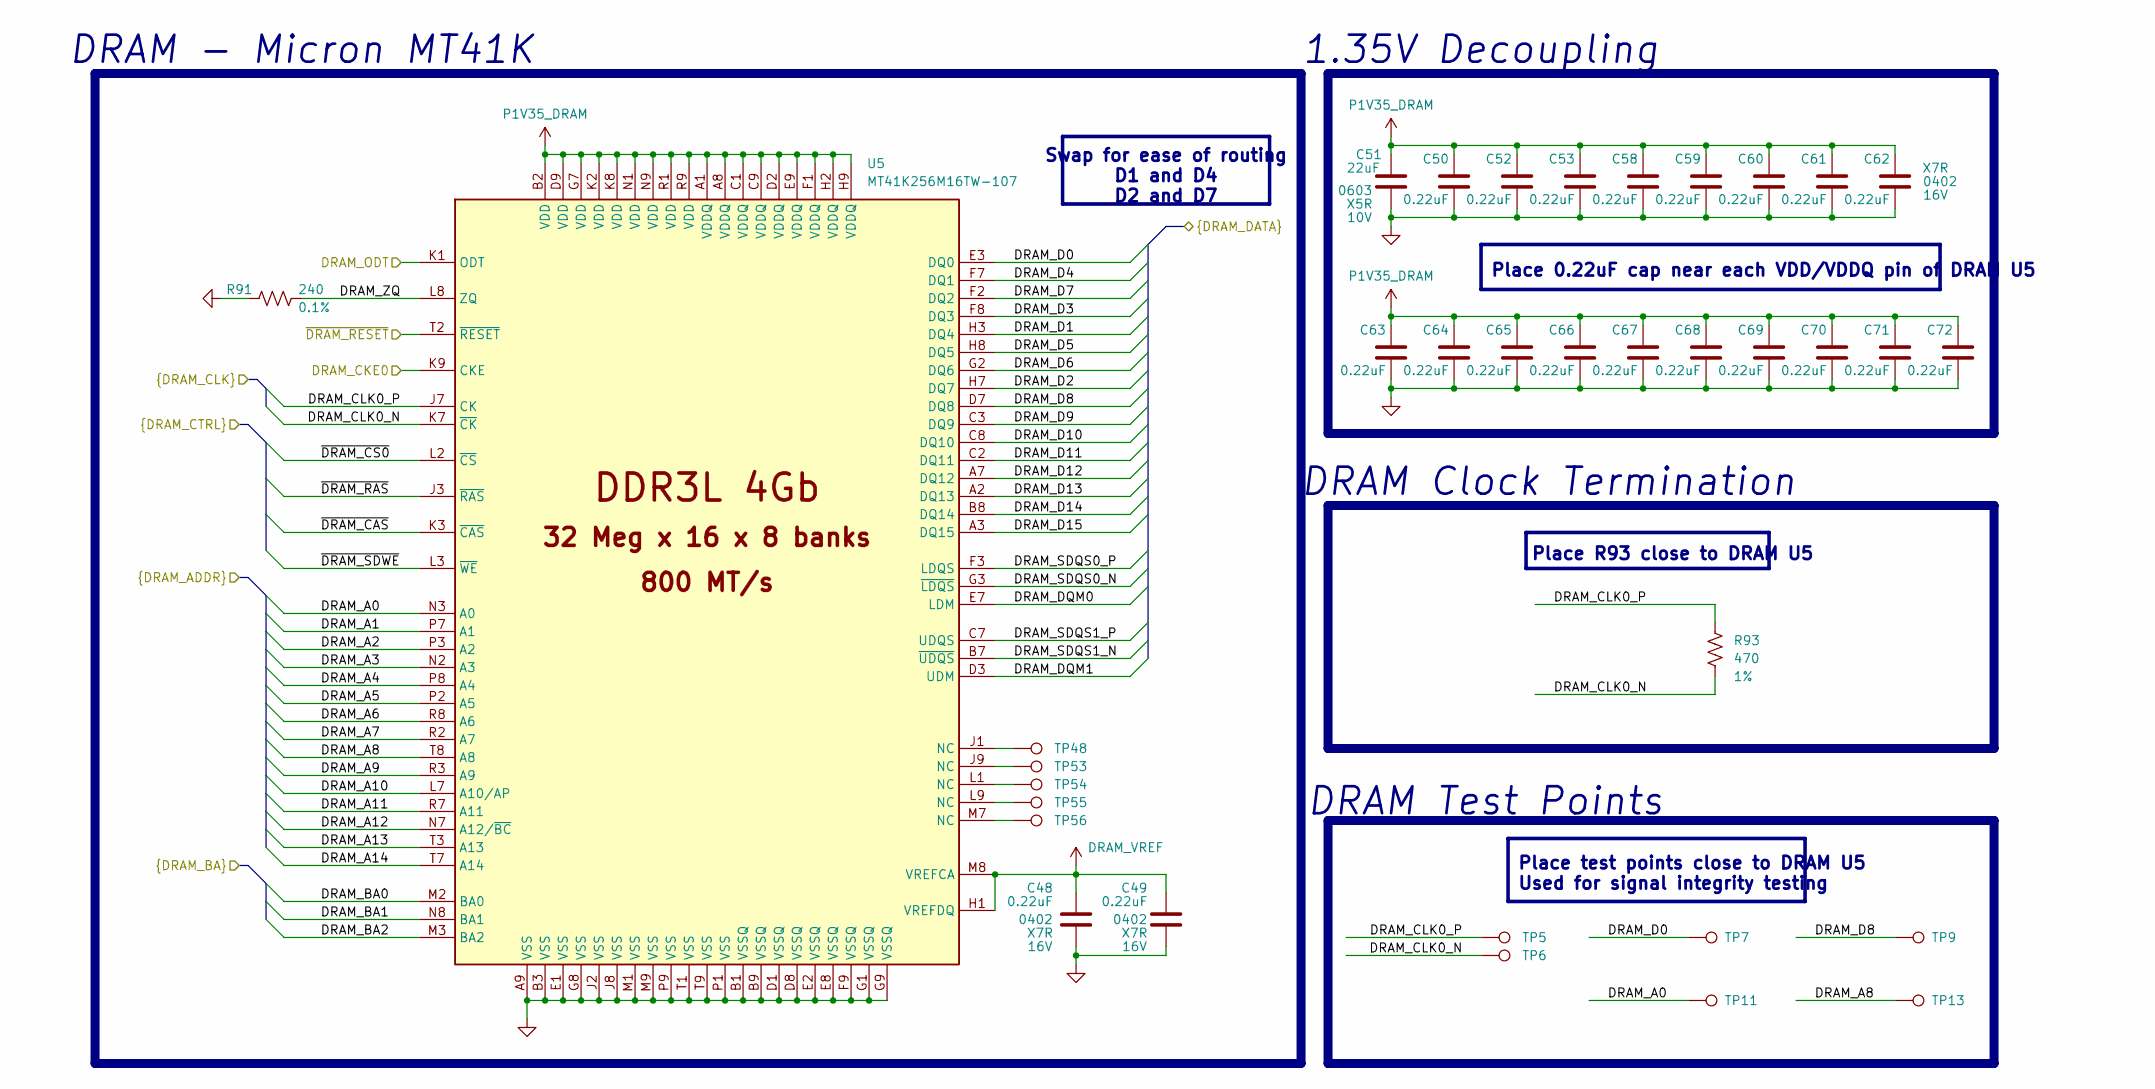
[picture p66: schematic DRAM_DDR3L.kicad_sch]

Parts:
C48, C49, C50, C52, C53, C58, C59, C60, C61, C62, C63, C64, C65, C66, C67, C68, C69, C70, C71, C72: 0.22uF; C_0402_1005Metric; Tolerance 10%; Voltage 16V; MPN GRM155R71C224KA12
C51: 22uF; C_0603_1608Metric; Tolerance 20%; Voltage 10V; MPN GRM188R61A226ME15
R91: 240; R_0402_1005Metric; Tolerance 0.1%; MPN RT0402BRD07240RL
R93: 470; R_0402_1005Metric; Tolerance 1%; MPN RCC0402470RFKED
TP5, TP6, TP7, TP9, TP11, TP13, TP48, TP53, TP54, TP55, TP56: TestPoint; TestPoint_Pad_D18mil
U5: MT41K256M16TW-107; MT41K_BGA96C80P9X16_1400X800X120; MPN MT41K256M16TW-107

Connections:
DRAM_A0: TP11.1, U5.N3 (A0)
DRAM_A1: U5.P7 (A1)
DRAM_A2: U5.P3 (A2)
DRAM_A3: U5.N2 (A3)
DRAM_A4: U5.P8 (A4)
DRAM_A5: U5.P2 (A5)
DRAM_A6: U5.R8 (A6)
DRAM_A7: U5.R2 (A7)
DRAM_A8: TP13.1, U5.T8 (A8)
DRAM_A9: U5.R3 (A9)
DRAM_A10: U5.L7 (A10/AP)
DRAM_A11: U5.R7 (A11)
DRAM_A12: U5.N7 (A12/~BC)
DRAM_A13: U5.T3 (A13)
DRAM_A14: U5.T7 (A14)
DRAM_BA0: U5.M2 (BA0)
DRAM_BA1: U5.N8 (BA1)
DRAM_BA2: U5.M3 (BA2)
DRAM_CKE0: U5.K9 (CKE)
DRAM_CLK0_N: R93.2, TP6.1, U5.K7 (~CK)
DRAM_CLK0_P: R93.1, TP5.1, U5.J7 (CK)
DRAM_D0: TP7.1, U5.E3 (DQ0)
DRAM_D1: U5.H3 (DQ4)
DRAM_D2: U5.H7 (DQ7)
DRAM_D3: U5.F8 (DQ3)
DRAM_D4: U5.F7 (DQ1)
DRAM_D5: U5.H8 (DQ5)
DRAM_D6: U5.G2 (DQ6)
DRAM_D7: U5.F2 (DQ2)
DRAM_D8: TP9.1, U5.D7 (DQ8)
DRAM_D9: U5.C3 (DQ9)
DRAM_D10: U5.C8 (DQ10)
DRAM_D11: U5.C2 (DQ11)
DRAM_D12: U5.A7 (DQ12)
DRAM_D13: U5.A2 (DQ13)
DRAM_D14: U5.B8 (DQ14)
DRAM_D15: U5.A3 (DQ15)
DRAM_DQM0: U5.E7 (LDM)
DRAM_DQM1: U5.D3 (UDM)
DRAM_ODT: U5.K1 (ODT)
DRAM_SDQS0_N: U5.G3 (~LDQS)
DRAM_SDQS0_P: U5.F3 (LDQS)
DRAM_SDQS1_N: U5.B7 (~UDQS)
DRAM_SDQS1_P: U5.C7 (UDQS)
DRAM_VREF: C48.2, C49.2, U5.H1 (VREFDQ), U5.M8 (VREFCA)
DRAM_ZQ: R91.1, U5.L8 (ZQ)
GND: C48.1, C49.1, C50.1, C51.2, C52.1, C53.1, C58.1, C59.1, C60.1, C61.1, C62.1, C63.1, C64.1, C65.1, C66.1, C67.1, C68.1, C69.1, C70.1, C71.1, C72.1, R91.2, U5.A9 (VSS), U5.B1 (VSSQ), U5.B3 (VSS), U5.B9 (VSSQ), U5.D1 (VSSQ), U5.D8 (VSSQ), U5.E1 (VSS), U5.E2 (VSSQ), U5.E8 (VSSQ), U5.F9 (VSSQ), U5.G1 (VSSQ), U5.G8 (VSS), U5.G9 (VSSQ), U5.J2 (VSS), U5.J8 (VSS), U5.M1 (VSS), U5.M9 (VSS), U5.P1 (VSS), U5.P9 (VSS), U5.T1 (VSS), U5.T9 (VSS)
unnamed: TP48.1, U5.J1 (NC)
unnamed: TP53.1, U5.J9 (NC)
unnamed: TP54.1, U5.L1 (NC)
unnamed: TP55.1, U5.L9 (NC)
unnamed: TP56.1, U5.M7 (NC)
P1V35_DRAM: C50.2, C51.1, C52.2, C53.2, C58.2, C59.2, C60.2, C61.2, C62.2, C63.2, C64.2, C65.2, C66.2, C67.2, C68.2, C69.2, C70.2, C71.2, C72.2, U5.A1 (VDDQ), U5.A8 (VDDQ), U5.B2 (VDD), U5.C1 (VDDQ), U5.C9 (VDDQ), U5.D2 (VDDQ), U5.D9 (VDD), U5.E9 (VDDQ), U5.F1 (VDDQ), U5.G7 (VDD), U5.H2 (VDDQ), U5.H9 (VDDQ), U5.K2 (VDD), U5.K8 (VDD), U5.N1 (VDD), U5.N9 (VDD), U5.R1 (VDD), U5.R9 (VDD)
~DRAM_CAS: U5.K3 (~CAS)
~DRAM_CS0: U5.L2 (~CS)
~DRAM_RAS: U5.J3 (~RAS)
~DRAM_RESET: U5.T2 (~RESET)
~DRAM_SDWE: U5.L3 (~WE)

Notes on the sheet:
Place test points close to DRAM U5 Used for signal integrity testing
Swap for ease of routing D1 and D4 D2 and D7
DRAM Clock Termination
DRAM - Micron MT41K
Place R93 close to DRAM U5
1.35V Decoupling
DRAM Test Points
Place 0.22uF cap near each VDD/VDDQ pin of DRAM U5
