a1wolfe/iMX6-BareBones/Kicad/Devices_Storage.kicad_sch

## KiCad design Kicad/Devices_Storage.kicad_sch (2026-04-11)

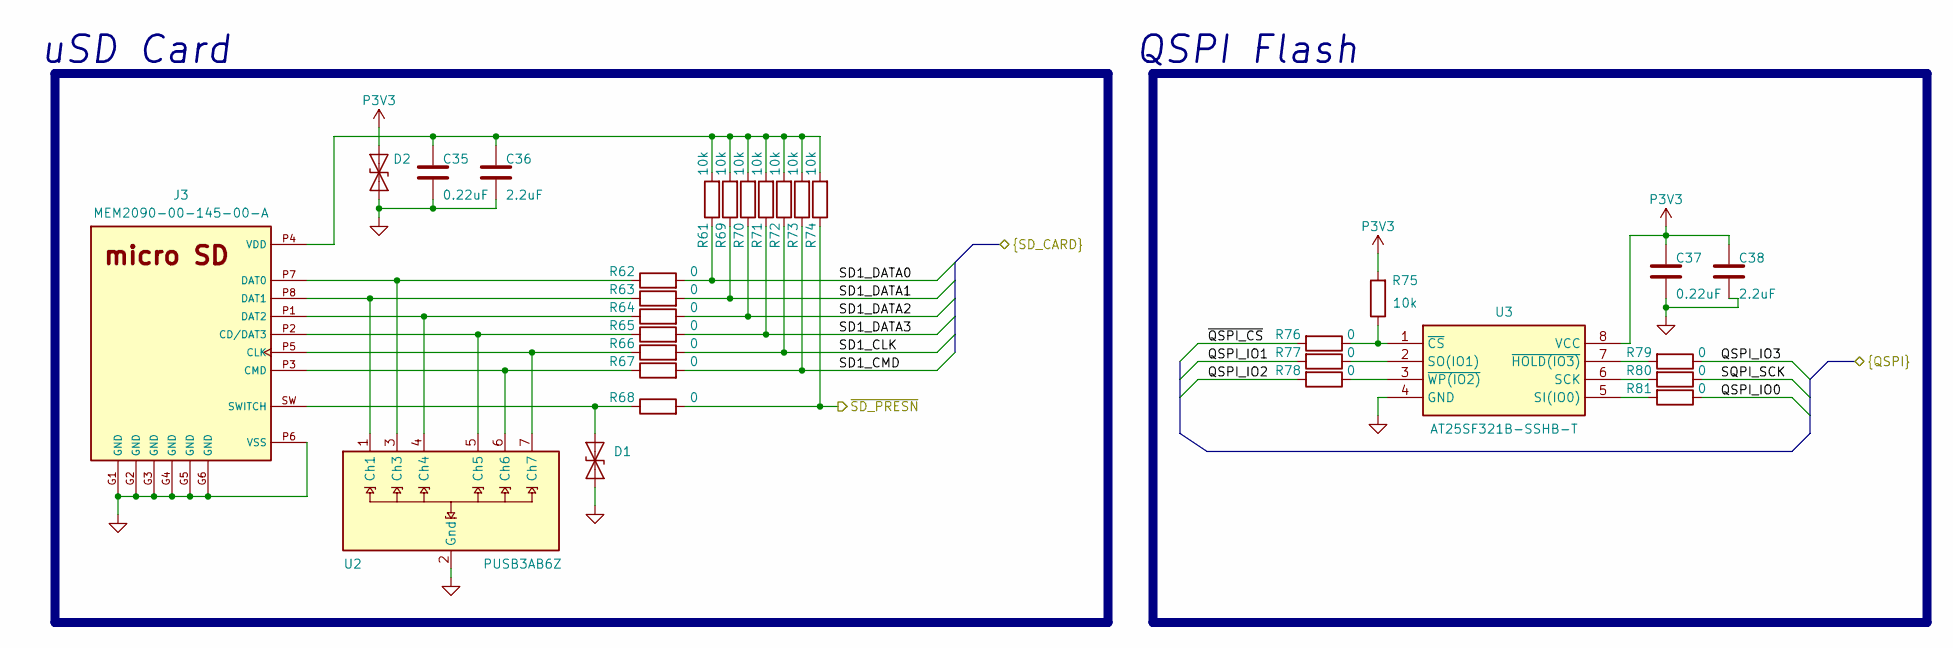
[picture p67: schematic Devices_Storage.kicad_sch]

Parts:
C35, C37: 0.22uF; C_0603_1608Metric
C36, C38: 2.2uF; C_0603_1608Metric
D1, D2: ESD9B5.0ST5G; D_SOD-923
J3: MEM2090-00-145-00-A
R61, R69, R70, R71, R72, R73, R74, R75: 10k
R62, R63, R64, R65, R66, R67, R68, R76, R77, R78, R79, R80, R81: 0
U2: PUSB3AB6Z; IC_PUSB3AB6Z_ESD-SD
U3: AT25SF321B-SSHB-T; SOIC127P600X175-8N; Manufacturer_Part_Number AT25SF321B-SSHB-T; Mouser Part Number 988-AT25SF321BSSHB-T

Connections:
GND: C35.2, C36.2, C37.2, C38.2, D1.1 (A1), D2.1 (A1), J3.G1 (GND), J3.G2 (GND), J3.G3 (GND), J3.G4 (GND), J3.G5 (GND), J3.G6 (GND), J3.P6 (VSS), U2.2 (Gnd), U3.4 (GND)
unnamed: C35.1, C36.1, J3.P4 (VDD), R61.2, R69.2, R70.2, R71.2, R72.2, R73.2, R74.2
unnamed: D1.2 (A2), J3.SW (SWITCH), R68.1
unnamed: J3.P1 (DAT2), R64.1, U2.4 (Ch4)
unnamed: J3.P2 (CD/DAT3), R65.1, U2.5 (Ch5)
unnamed: J3.P3 (CMD), R67.1, U2.6 (Ch6)
unnamed: J3.P5 (CLK), R66.1, U2.7 (Ch7)
unnamed: J3.P7 (DAT0), R62.1, U2.3 (Ch3)
unnamed: J3.P8 (DAT1), R63.1, U2.1 (Ch1)
unnamed: R75.1, R76.1, U3.1 (~CS)
unnamed: R77.1, U3.2 (SO(IO1))
unnamed: R78.1, U3.3 (~WP(IO2))
unnamed: R79.2, U3.7 (~HOLD(IO3))
unnamed: R80.2, U3.6 (SCK)
unnamed: R81.2, U3.5 (SI(IO0))
P3V3: C37.1, C38.1, D2.2 (A2), R75.2, U3.8 (VCC)
QSPI_IO0: R81.1
QSPI_IO1: R77.2
QSPI_IO2: R78.2
QSPI_IO3: R79.1
SD1_CLK: R66.2, R72.1
SD1_CMD: R67.2, R73.1
SD1_DATA0: R61.1, R62.2
SD1_DATA1: R63.2, R69.1
SD1_DATA2: R64.2, R70.1
SD1_DATA3: R65.2, R71.1
SQPI_SCK: R80.1
~QSPI_CS: R76.2
~SD_PRESN: R68.2, R74.1

Notes on the sheet:
QSPI Flash
uSD Card
