a1wolfe/iMX6-BareBones/Kicad/Ethernet.kicad_sch

## KiCad design Kicad/Ethernet.kicad_sch (2026-04-23)

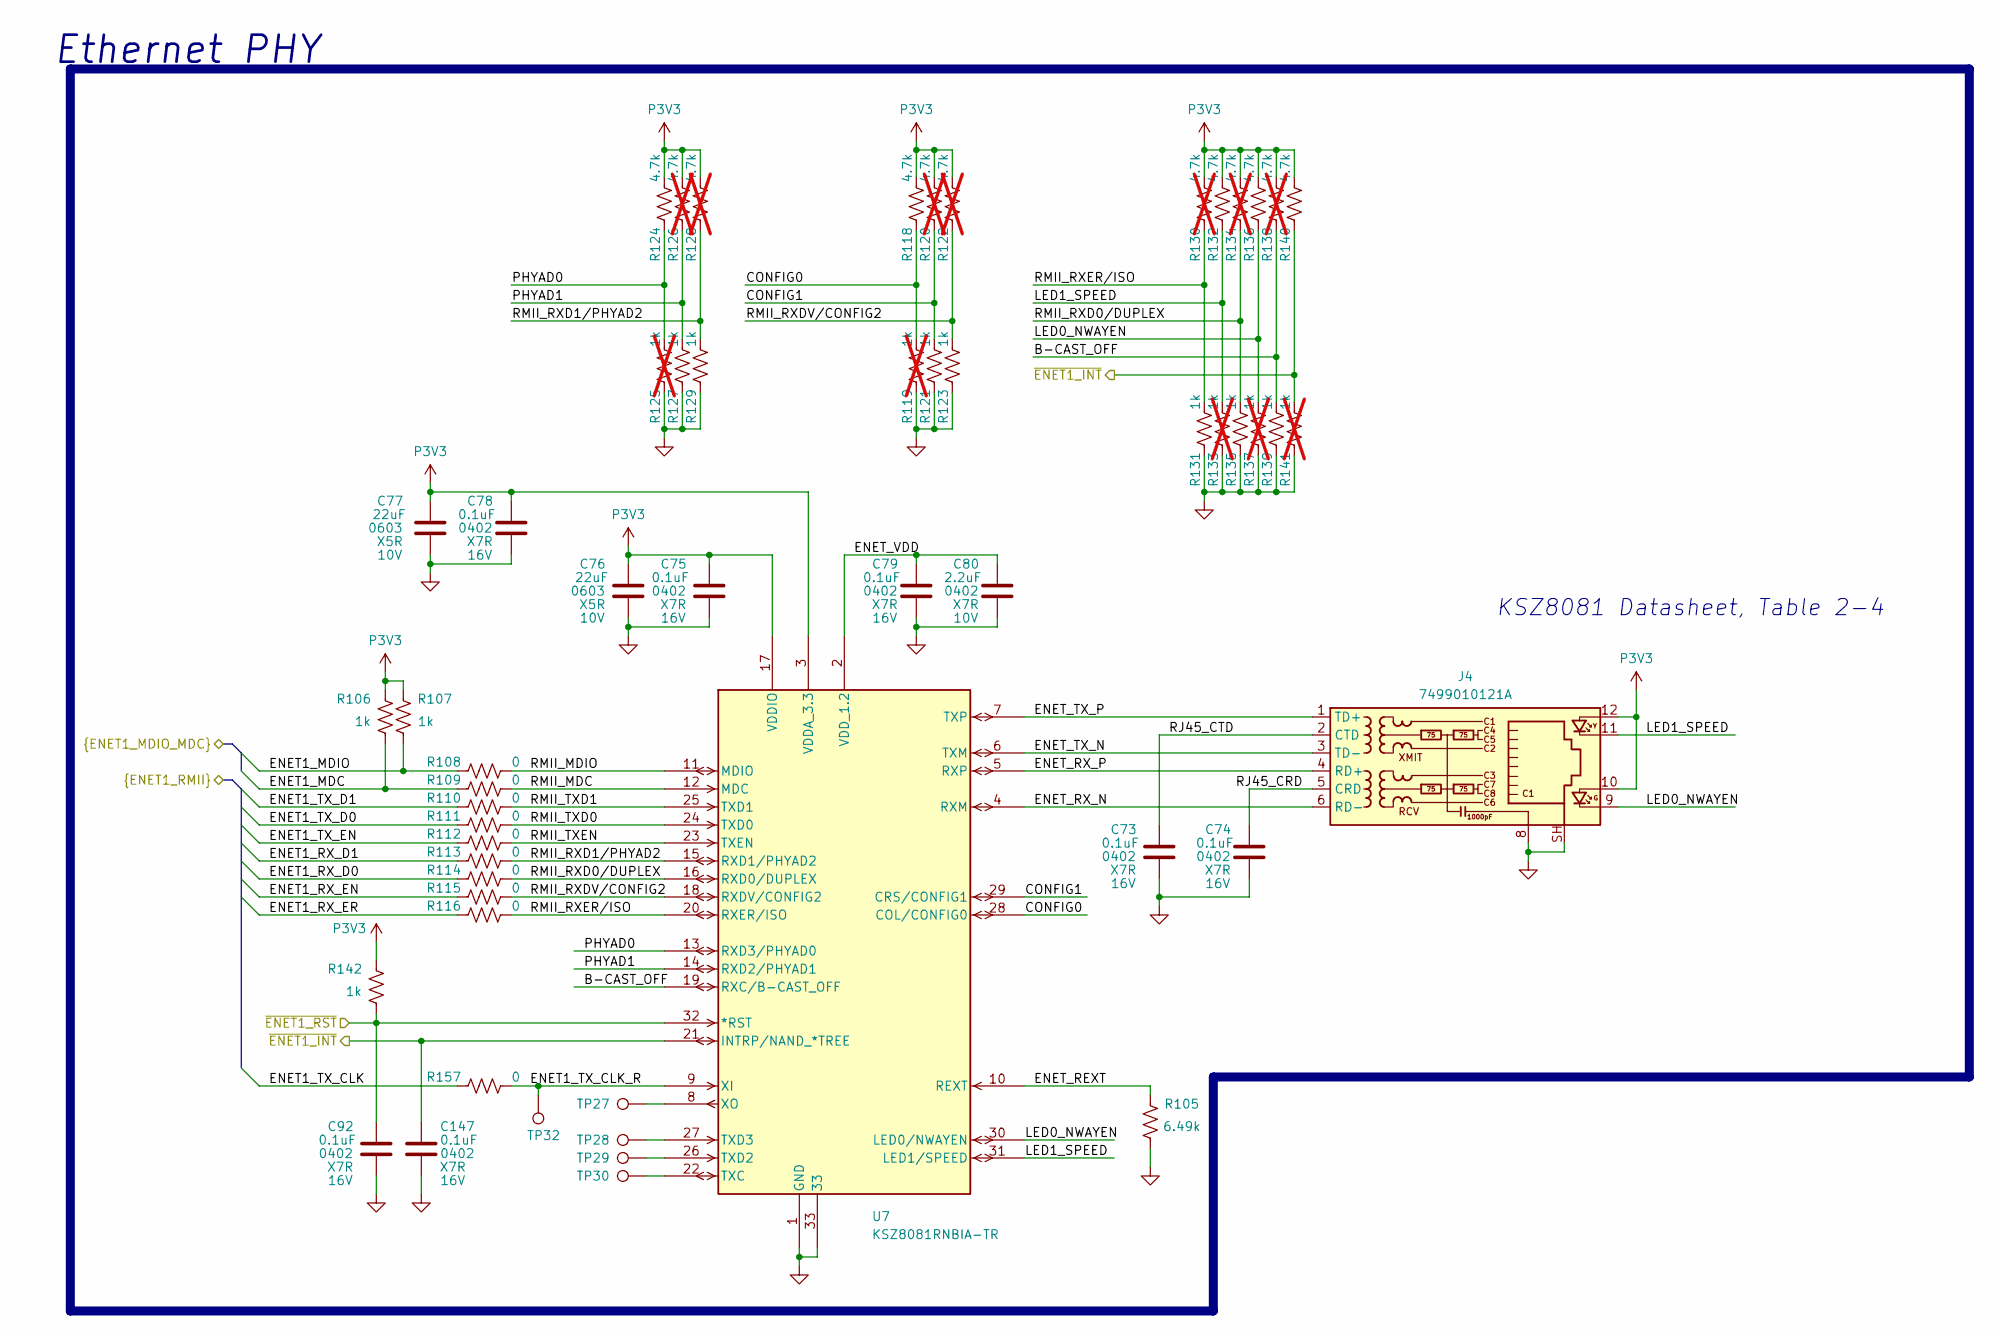
[picture p68: schematic Ethernet.kicad_sch]

Parts:
C73, C74, C75, C78, C79, C92, C147: 0.1uF; C_0402_1005Metric; Tolerance 10%; Voltage 16V; MPN GRM155R71C104KA88
C76, C77: 22uF; C_0603_1608Metric; Tolerance 20%; Voltage 10V; MPN GRM188R61A226ME15
C80: 2.2uF; C_0402_1005Metric; Tolerance 10%; Voltage 10V; MPN GRM155Z71A225KE44
J4: 7499010121A; T_Wurth_WE-RJ45LAN_7499010121A; MPN 7499010121A
R105: 6.49k; R_0402_1005Metric; Tolerance 1%; MPN CRCW04026K49FKED
R106, R107, R121, R123, R127, R129, R131, R135, R139, R142: 1k; R_0402_1005Metric; Tolerance 1%; MPN RC0402FR-7W1KL
R108, R109, R110, R111, R112, R113, R114, R115, R116, R157: 0; R_0402_1005Metric; Tolerance Jumper; MPN RC0402JR-070RL
R118, R124, R132, R136, R140: 4.7k; R_0402_1005Metric; Tolerance 1%; MPN RC0402FR-074K7L
R119, R125, R133, R137, R141: 1k; R_0402_1005Metric; Tolerance 1%; MPN RC0402FR-7W1KL; not fitted
R120, R122, R126, R128, R130, R134, R138: 4.7k; R_0402_1005Metric; Tolerance 1%; MPN RC0402FR-074K7L; not fitted
TP27, TP28, TP29, TP30, TP32: TestPoint; TestPoint_Pad_D30mil
U7: KSZ8081RNBIA-TR; KSZ8081RNB_QFN32; MPN KSZ8081RNBIA-TR

Connections:
B-CAST_OFF: R138.1, R139.2, U7.19 (RXC/B-CAST_OFF)
CONFIG0: R118.1, R119.2, U7.28 (COL/CONFIG0)
CONFIG1: R120.1, R121.2, U7.29 (CRS/CONFIG1)
ENET1_MDC: R106.1, R109.2
ENET1_MDIO: R107.1, R108.2
ENET1_RX_D0: R114.2
ENET1_RX_D1: R113.2
ENET1_RX_EN: R115.2
ENET1_RX_ER: R116.2
ENET1_TX_CLK: R157.2
ENET1_TX_CLK_R: R157.1, TP32.1, U7.9 (XI)
ENET1_TX_D0: R111.2
ENET1_TX_D1: R110.2
ENET1_TX_EN: R112.2
ENET_REXT: R105.2, U7.10 (REXT)
ENET_RX_N: J4.6 (RD-), U7.4 (RXM)
ENET_RX_P: J4.4 (RD+), U7.5 (RXP)
ENET_TX_N: J4.3 (TD-), U7.6 (TXM)
ENET_TX_P: J4.1 (TD+), U7.7 (TXP)
ENET_VDD: C79.1, C80.1, U7.2 (VDD_1.2)
GND: C73.2, C74.2, C75.2, C76.2, C77.2, C78.2, C79.2, C80.2, C92.2, C147.2, J4.8, J4.SH, R105.1, R119.1, R121.1, R123.1, R125.1, R127.1, R129.1, R131.1, R133.1, R135.1, R137.1, R139.1, R141.1, U7.1 (GND), U7.33
LED0_NWAYEN: J4.9, R136.1, R137.2, U7.30 (LED0/NWAYEN)
LED1_SPEED: J4.11, R132.1, R133.2, U7.31 (LED1/SPEED)
unnamed: TP27.1, U7.8 (XO)
unnamed: TP28.1, U7.27 (TXD3)
unnamed: TP29.1, U7.26 (TXD2)
unnamed: TP30.1, U7.22 (TXC)
P3V3: C75.1, C76.1, C77.1, C78.1, J4.10, J4.12, R106.2, R107.2, R118.2, R120.2, R122.2, R124.2, R126.2, R128.2, R130.2, R132.2, R134.2, R136.2, R138.2, R140.2, R142.2, U7.3 (VDDA_3.3), U7.17 (VDDIO)
PHYAD0: R124.1, R125.2, U7.13 (RXD3/PHYAD0)
PHYAD1: R126.1, R127.2, U7.14 (RXD2/PHYAD1)
RJ45_CRD: C74.1, J4.5 (CRD)
RJ45_CTD: C73.1, J4.2 (CTD)
RMII_MDC: R109.1, U7.12 (MDC)
RMII_MDIO: R108.1, U7.11 (MDIO)
RMII_RXD0/DUPLEX: R114.1, R134.1, R135.2, U7.16 (RXD0/DUPLEX)
RMII_RXD1/PHYAD2: R113.1, R128.1, R129.2, U7.15 (RXD1/PHYAD2)
RMII_RXDV/CONFIG2: R115.1, R122.1, R123.2, U7.18 (RXDV/CONFIG2)
RMII_RXER/ISO: R116.1, R130.1, R131.2, U7.20 (RXER/ISO)
RMII_TXD0: R111.1, U7.24 (TXD0)
RMII_TXD1: R110.1, U7.25 (TXD1)
RMII_TXEN: R112.1, U7.23 (TXEN)
~ENET1_INT: C147.1, R140.1, R141.2, U7.21 (INTRP/NAND_*TREE)
~ENET1_RST: C92.1, R142.1, U7.32 (*RST)

Notes on the sheet:
Ethernet PHY
KSZ8081 Datasheet, Table 2-4
