a1wolfe/iMX6-BareBones/Kicad/Headers.kicad_sch

## KiCad design Kicad/Headers.kicad_sch (2026-04-23)

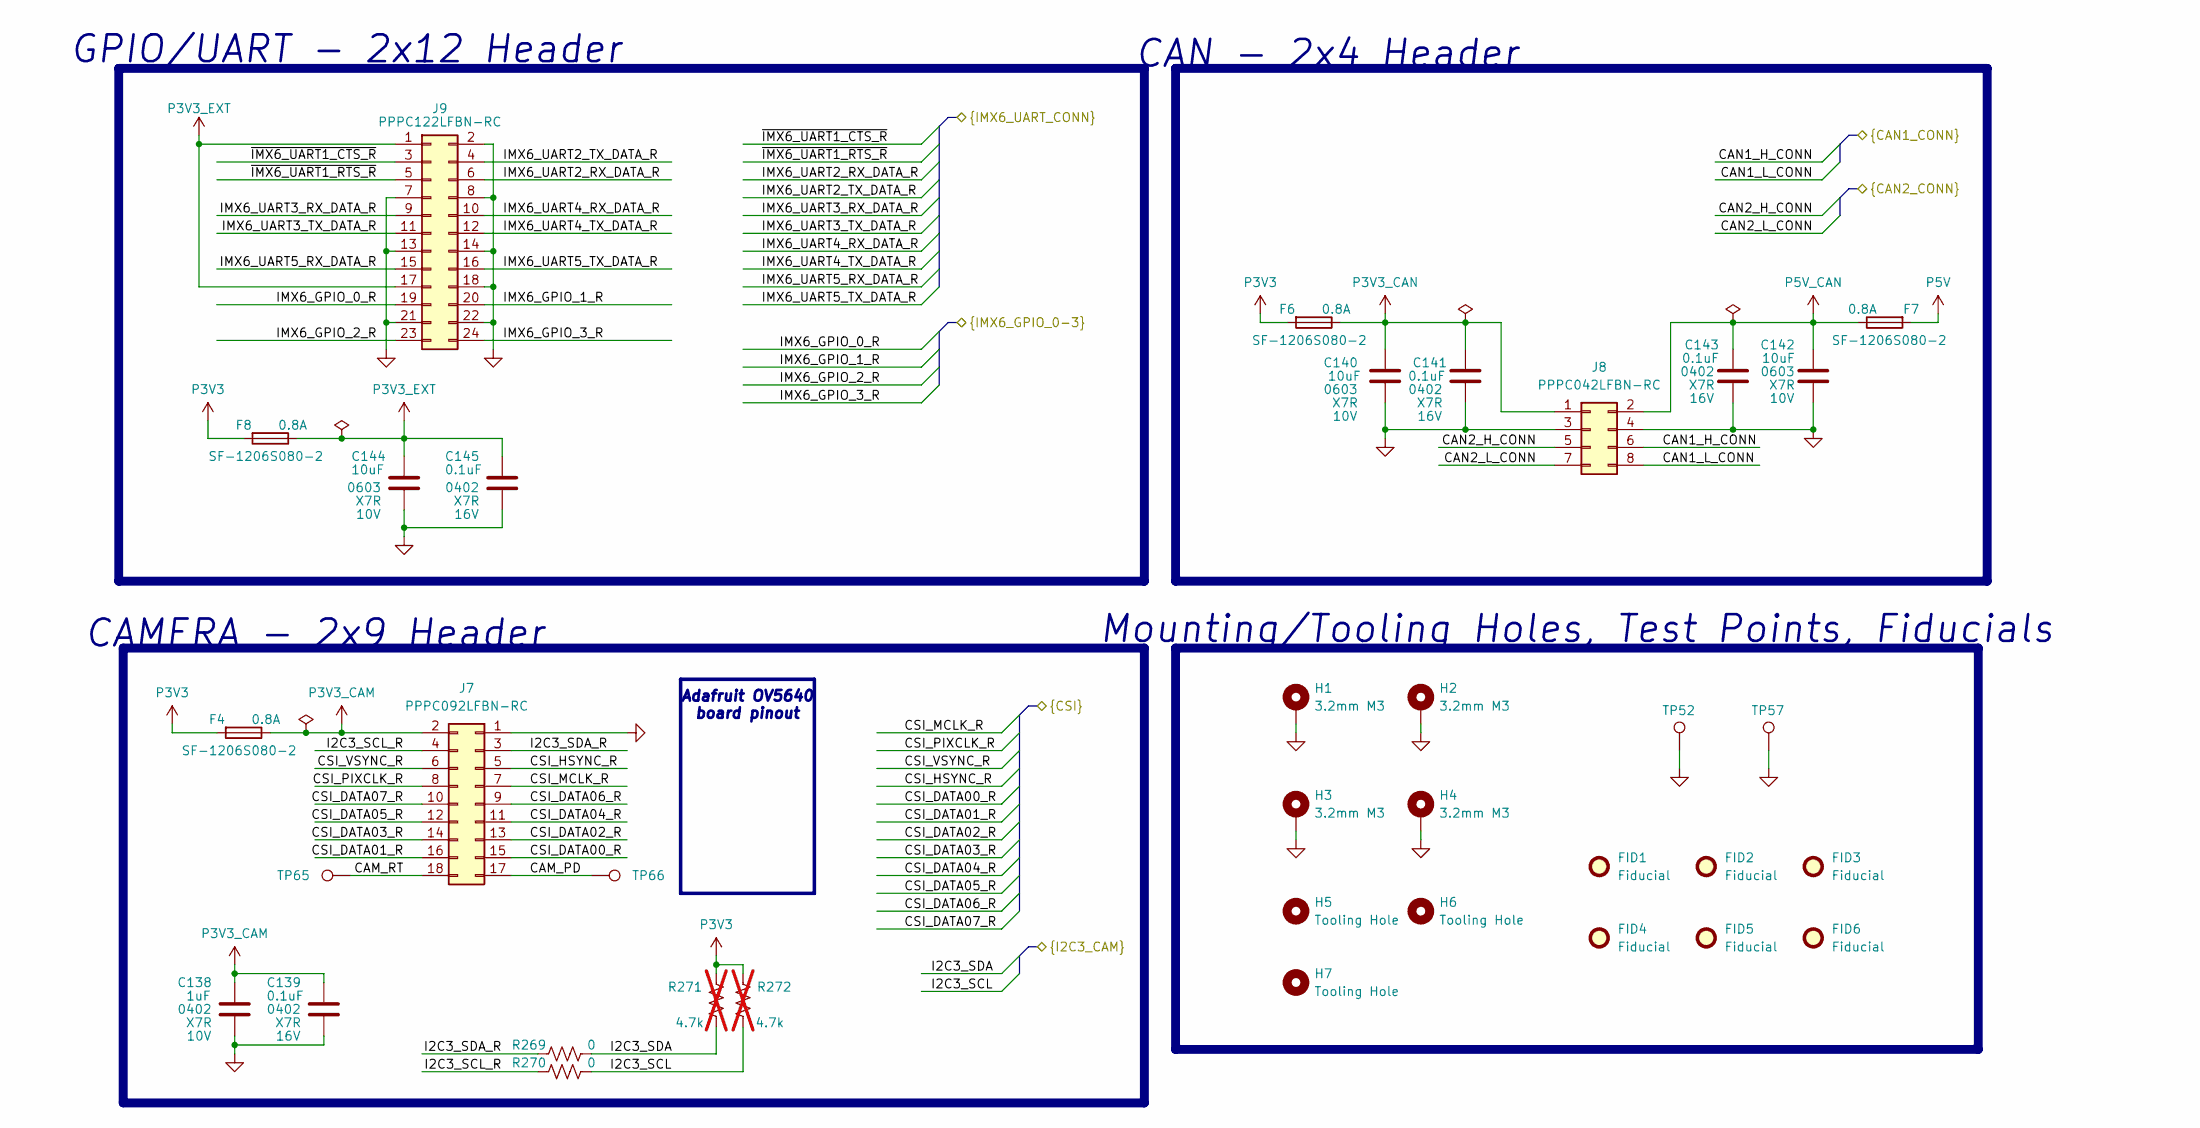
[picture p69: schematic Headers.kicad_sch]

Parts:
C138: 1uF; C_0402_1005Metric; Tolerance 10%; Voltage 10V; MPN GRM155Z71A105KE01
C139, C141, C143, C145: 0.1uF; C_0402_1005Metric; Tolerance 10%; Voltage 16V; MPN GRM155R71C104KA88
C140, C142, C144: 10uF; C_0603_1608Metric; Tolerance 10%; Voltage 10V; MPN GRM188Z71A106KA73
F4, F6, F7, F8: SF-1206S080-2; Fuse_1206_3216Metric; Current Rating 0.8A; MPN SF-1206S080-2
FID1, FID2, FID3, FID4, FID5, FID6: Fiducial; Fiducial_1mm_Mask2mm
H1, H2, H3, H4: 3.2mm M3; MountingHole_3.2mm_M3_Pad_Via
H5, H6, H7: Tooling Hole; ToolingHole_1.152mm
J7: PPPC092LFBN-RC; PinSocket_2x09_P2.54mm_Vertical (Sullins PPPC092LFBN-RC); MPN PPPC092LFBN-RC
J8: PPPC042LFBN-RC; PinSocket_2x04_P2.54mm_Vertical ( Sullins PPPC042LFBN-RC); MPN PPPC042LFBN-RC
J9: PPPC122LFBN-RC; PinSocket_2x12_P2.54mm_Vertical (Sullins PPPC122LFBN-RC); MPN PPPC122LFBN-RC
R269, R270: 0; R_0402_1005Metric; Tolerance Jumper; MPN RC0402JR-070RL
R271, R272: 4.7k; R_0402_1005Metric; Tolerance 1%; MPN RC0402FR-074K7L; not fitted
TP52, TP57: TestPoint; KEYSTONE_5015; MPN 5015
TP65, TP66: TestPoint; TestPoint_Pad_D30mil

Connections:
CAM_PD: J7.17, TP66.1
CAM_RT: J7.18, TP65.1
CAN1_H_CONN: J8.6
CAN1_L_CONN: J8.8
CAN2_H_CONN: J8.5
CAN2_L_CONN: J8.7
CSI_DATA00_R: J7.15
CSI_DATA01_R: J7.16
CSI_DATA02_R: J7.13
CSI_DATA03_R: J7.14
CSI_DATA04_R: J7.11
CSI_DATA05_R: J7.12
CSI_DATA06_R: J7.9
CSI_DATA07_R: J7.10
CSI_HSYNC_R: J7.5
CSI_MCLK_R: J7.7
CSI_PIXCLK_R: J7.8
CSI_VSYNC_R: J7.6
GND: C138.2, C139.2, C140.2, C141.2, C142.2, C143.2, C144.2, C145.2, H1.1, H2.1, H3.1, H4.1, J7.1, J8.3, J8.4, J9.2, J9.7, J9.8, J9.13, J9.14, J9.18, J9.21, J9.22, TP52.1, TP57.1
I2C3_SCL: R270.2, R272.1
I2C3_SCL_R: J7.4, R270.1
I2C3_SDA: R269.2, R271.1
I2C3_SDA_R: J7.3, R269.1
IMX6_GPIO_0_R: J9.19
IMX6_GPIO_1_R: J9.20
IMX6_GPIO_2_R: J9.23
IMX6_GPIO_3_R: J9.24
IMX6_UART2_RX_DATA_R: J9.6
IMX6_UART2_TX_DATA_R: J9.4
IMX6_UART3_RX_DATA_R: J9.9
IMX6_UART3_TX_DATA_R: J9.11
IMX6_UART4_RX_DATA_R: J9.10
IMX6_UART4_TX_DATA_R: J9.12
IMX6_UART5_RX_DATA_R: J9.15
IMX6_UART5_TX_DATA_R: J9.16
P3V3: F4.2, F6.2, F8.2, R271.2, R272.2
P3V3_CAM: C138.1, C139.1, F4.1, J7.2
P3V3_CAN: C140.1, C141.1, F6.1, J8.1
P3V3_EXT: C144.1, C145.1, F8.1, J9.1, J9.17
P5V: F7.2
P5V_CAN: C142.1, C143.1, F7.1, J8.2
~IMX6_UART1_CTS_R: J9.3
~IMX6_UART1_RTS_R: J9.5

Notes on the sheet:
CAMERA - 2x9 Header
CAN - 2x4 Header
Mounting/Tooling Holes, Test Points, Fiducials
Adafruit OV5640 board pinout
GPIO/UART - 2x12 Header
