a1wolfe/iMX6-BareBones/Kicad/Power2.kicad_sch

## KiCad design Kicad/Power2.kicad_sch (2026-04-23)

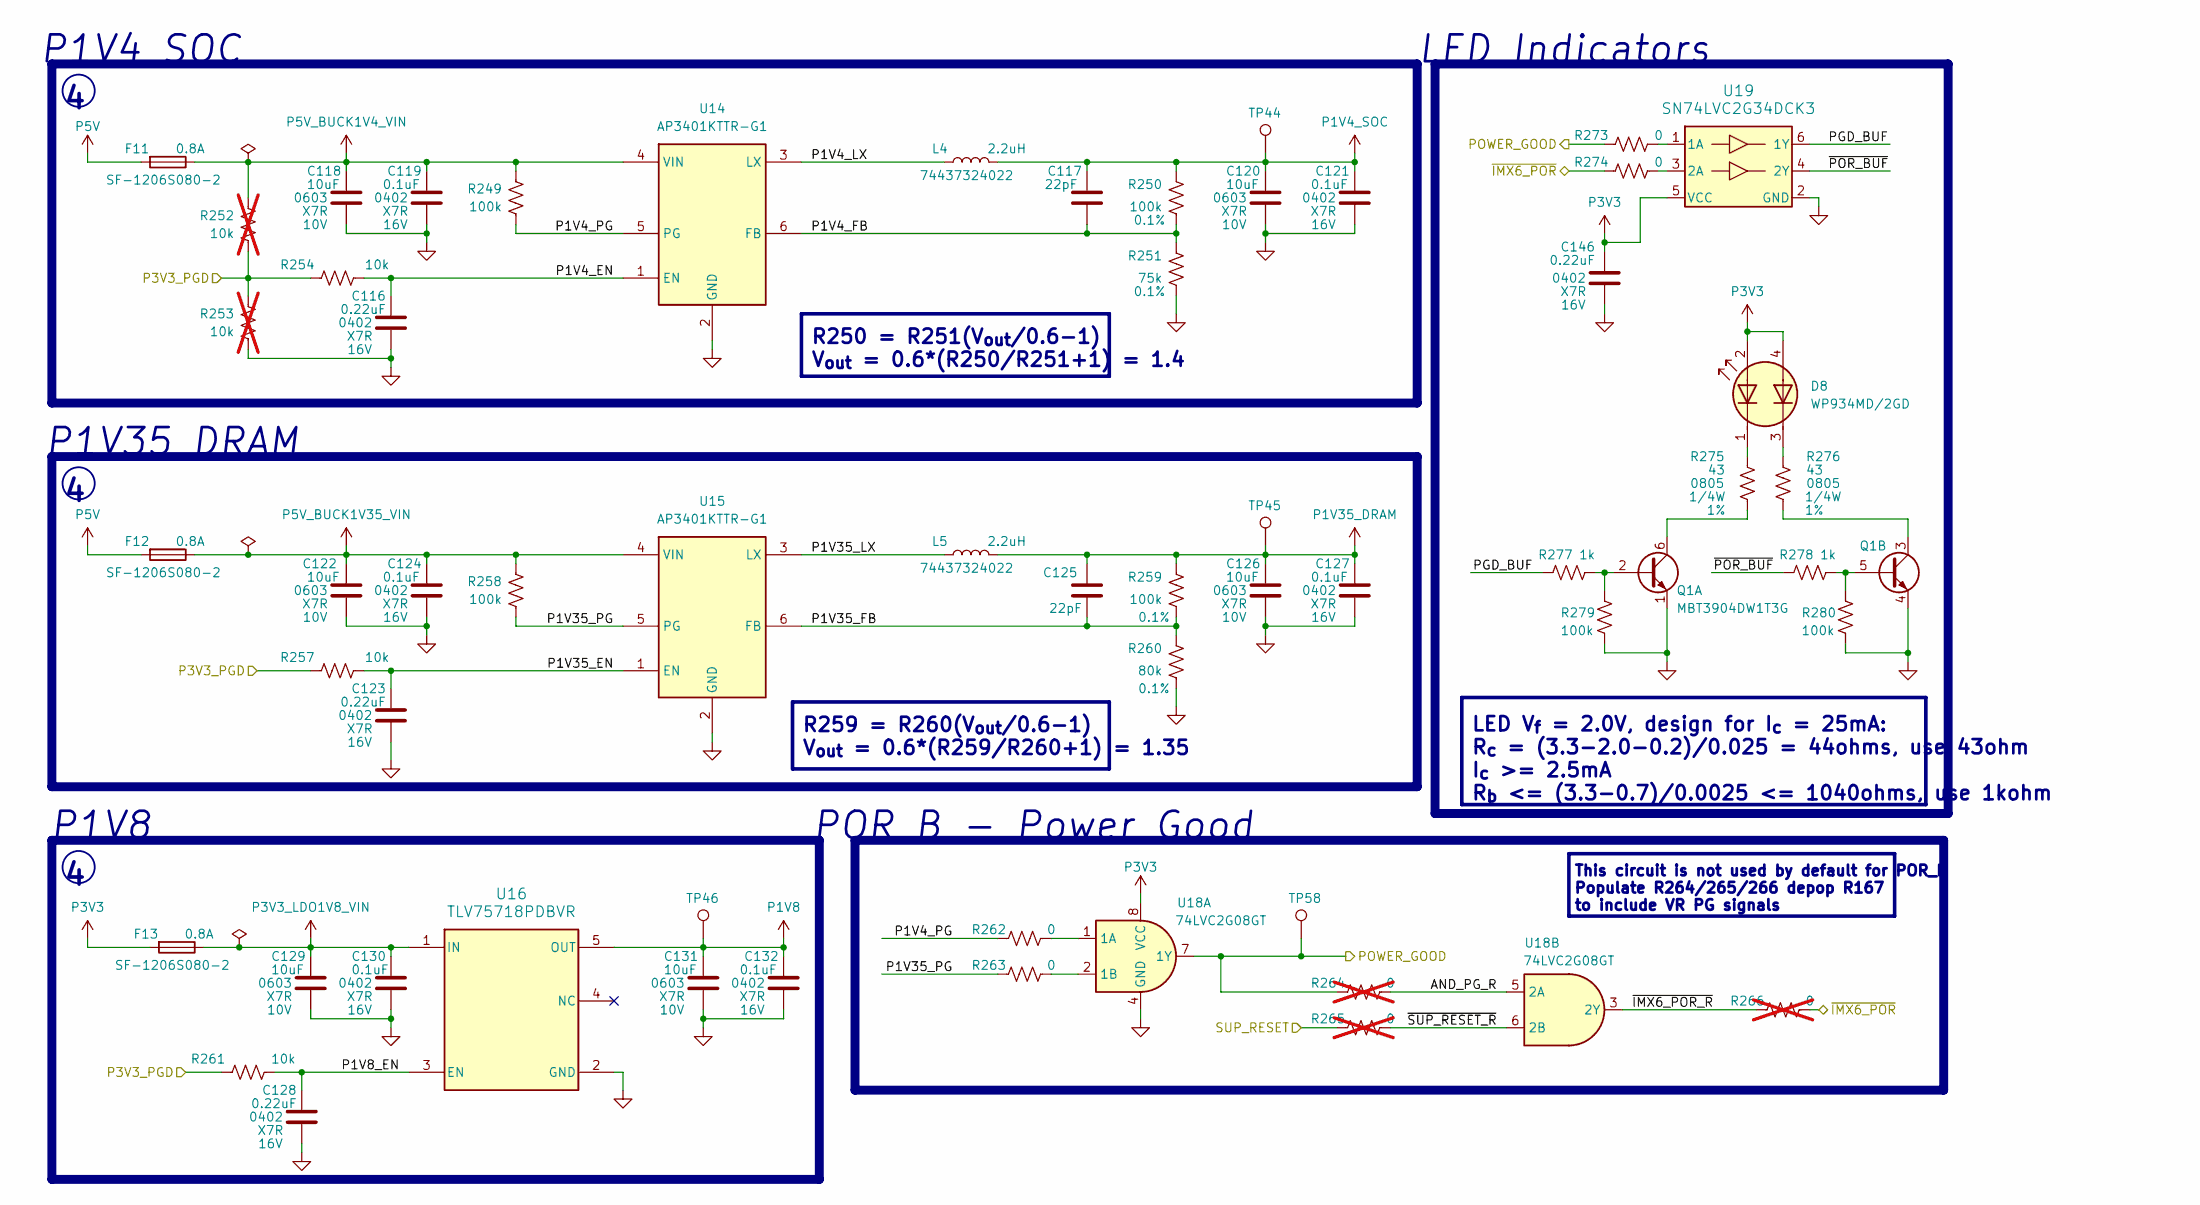
[picture p70: schematic Power2.kicad_sch]

Parts:
C116, C123, C128, C146: 0.22uF; C_0402_1005Metric; Tolerance 10%; Voltage 16V; MPN GRM155R71C224KA12
C117, C125: 22pF; C_0402_1005Metric; Tolerance 1%; Voltage 50V; MPN GJM1555C1H220FB01
C118, C120, C122, C126, C129, C131: 10uF; C_0603_1608Metric; Tolerance 10%; Voltage 10V; MPN GRM188Z71A106KA73
C119, C121, C124, C127, C130, C132: 0.1uF; C_0402_1005Metric; Tolerance 10%; Voltage 16V; MPN GRM155R71C104KA88
D8: WP934MD/2GD; LED_WP934MD_2GD; MPN WP934MD/2GD
F11, F12, F13: SF-1206S080-2; Fuse_1206_3216Metric; Current Rating 0.8A; MPN SF-1206S080-2
L4, L5: 2.2uH; WE-LHMI_4020; MPN 74437324022
Q1: MBT3904DW1T3G; DualNPN_MBT3904DW1T3G_SOT65P210X110-6N; MPN MBT3904DW1T3G
R249, R250, R258, R259, R279, R280: 100k; R_0402_1005Metric; Tolerance 0.1%; MPN RT0402BRE07100KL
R251: 75k; R_0402_1005Metric; Tolerance 0.1%; MPN RT0402BRD0775KL
R252, R253: 10k; R_0402_1005Metric; Tolerance 1%; MPN RC0402FR-7W10KL; not fitted
R254, R257, R261: 10k; R_0402_1005Metric; Tolerance 1%; MPN RC0402FR-7W10KL
R260: 80k; R_0402_1005Metric; Tolerance 0.1%; MPN RNCF0402BTE80K0
R262, R263, R273, R274: 0; R_0402_1005Metric; Tolerance Jumper; MPN RC0402JR-070RL
R264, R265, R266: 0; R_0402_1005Metric; Tolerance Jumper; MPN RC0402JR-070RL; not fitted
R275, R276: 43; R_0805_2012Metric; Tolerance 1%; MPN CRCW080543R0FKEA
R277, R278: 1k; R_0402_1005Metric; Tolerance 1%; MPN RC0402FR-7W1KL
TP44, TP45, TP46: TestPoint; KEYSTONE_5015; MPN 5015
TP58: TestPoint; TestPoint_Pad_D30mil
U14, U15: AP3401KTTR-G1; AP3401_SOT95P280X100-6N; Manufacturer_Part_Number AP3401KTTR-G1; Mouser Part Number 621-AP3401KTTR-G1
U16: TLV75718PDBVR; LTV75718; MPN TLV75718PDBVR
U18: 74LVC2G08GT; DualAnd_74LVC2G08GT; MPN 74LVC2G08GT
U19: SN74LVC2G34DCK3; SN74LVC2G34_DCK6; MPN SN74LVC2G34DCK3

Connections:
AND_PG_R: R264.2, U18.5 (2A)
GND: C116.1, C118.2, C119.2, C120.2, C121.2, C122.2, C123.1, C124.2, C126.2, C127.2, C128.1, C129.2, C130.2, C131.2, C132.2, C146.1, Q1.1 (E1), Q1.4 (E2), R251.1, R253.1, R260.1, R279.2, R280.2, U14.2 (GND), U15.2 (GND), U16.2 (GND), U18.4 (GND), U19.2 (GND)
unnamed: D8.1 (K1), R275.1
unnamed: D8.3 (K2), R276.1
unnamed: Q1.2 (B1), R277.2, R279.1
unnamed: Q1.3 (C2), R276.2
unnamed: Q1.5 (B2), R278.2, R280.1
unnamed: Q1.6 (C1), R275.2
unnamed: R262.2, U18.1 (1A)
unnamed: R263.2, U18.2 (1B)
unnamed: R273.1, U19.1 (1A)
unnamed: R274.1, U19.3 (2A)
P1V4_EN: C116.2, R254.1, U14.1 (EN)
P1V4_FB: C117.1, R250.1, R251.2, U14.6 (FB)
P1V4_LX: L4.1, U14.3 (LX)
P1V4_PG: R249.1, R262.1, U14.5 (PG)
P1V4_SOC: C117.2, C120.1, C121.1, L4.2, R250.2, TP44.1
P1V8: C131.1, C132.1, TP46.1, U16.5 (OUT)
P1V8_EN: C128.2, R261.1, U16.3 (EN)
P1V35_DRAM: C125.2, C126.1, C127.1, L5.2, R259.2, TP45.1
P1V35_EN: C123.2, R257.1, U15.1 (EN)
P1V35_FB: C125.1, R259.1, R260.2, U15.6 (FB)
P1V35_LX: L5.1, U15.3 (LX)
P1V35_PG: R258.1, R263.1, U15.5 (PG)
P3V3: C146.2, D8.2 (A1), D8.4 (A2), F13.2, U18.8 (VCC), U19.5 (VCC)
P3V3_LDO1V8_VIN: C129.1, C130.1, F13.1, U16.1 (IN)
P3V3_PGD: R252.1, R253.2, R254.2, R257.2, R261.2
P5V: F11.2, F12.2
P5V_BUCK1V4_VIN: C118.1, C119.1, F11.1, R249.2, R252.2, U14.4 (VIN)
P5V_BUCK1V35_VIN: C122.1, C124.1, F12.1, R258.2, U15.4 (VIN)
PGD_BUF: R277.1, U19.6 (1Y)
POWER_GOOD: R264.1, R273.2, TP58.1, U18.7 (1Y)
SUP_RESET: R265.1
~IMX6_POR_R: R266.1, U18.3 (2Y)
~IMX6_POR: R266.2, R274.2
~POR_BUF: R278.1, U19.4 (2Y)
~SUP_RESET_R: R265.2, U18.6 (2B)

Notes on the sheet:
LED Indicators
R259 = R260(V_{out}/0.6-1) V_{out} = 0.6*(R259/R260+1) = 1.35
P1V8
P1V35_DRAM
R250 = R251(V_{out}/0.6-1) V_{out} = 0.6*(R250/R251+1) = 1.4
LED V_{f} = 2.0V, design for I_{c} = 25mA: R_{c} = (3.3-2.0-0.2)/0.025 = 44ohms, use 43ohm I_{c} >= 2.5mA R_{b} <= (3.3-0.7)/0.0025 <= 1040ohms, use 1kohm
This circuit is not used by default for POR_B Populate R264/265/266 depop R167 to include VR PG signals
POR_B - Power Good
P1V4_SOC
