a1wolfe/iMX6-BareBones/Kicad/Power.kicad_sch

## KiCad design Kicad/Power.kicad_sch (2026-04-23)

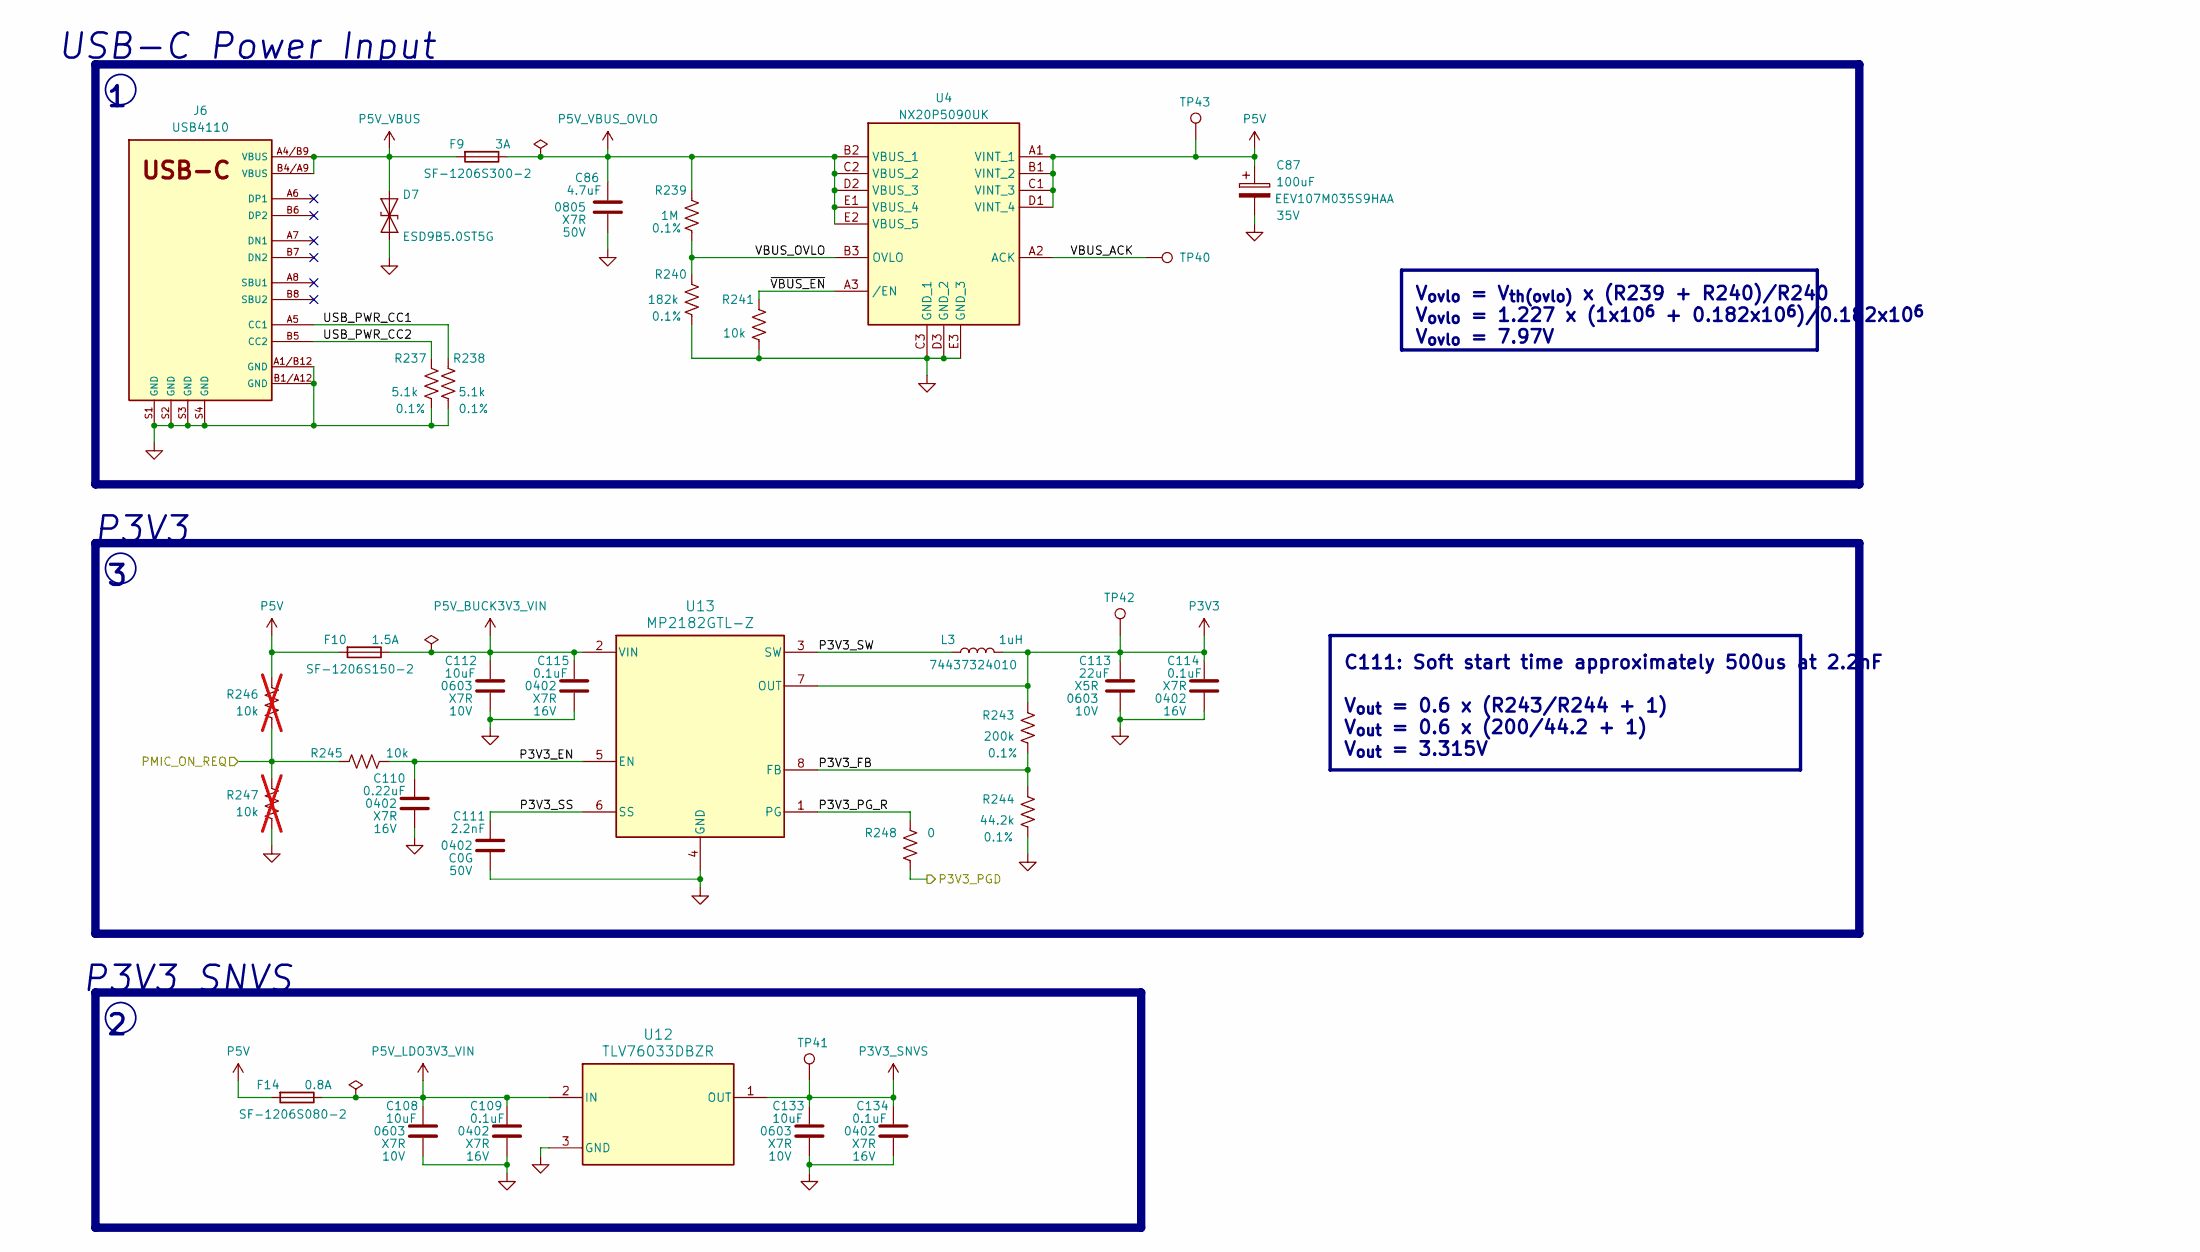
[picture p71: schematic Power.kicad_sch]

Parts:
C86: 4.7uF; C_0805_2012Metric; Voltage 50V; Tolerance 10%; MPN GRM21BZ71H475ME15
C87: 100uF; CP_Elec_6.3x7.7; Voltage 35V; Tolerance 20%; MPN EEV107M035S9HAA
C108, C112, C133: 10uF; C_0603_1608Metric; Tolerance 10%; Voltage 10V; MPN GRM188Z71A106KA73
C109, C114, C115, C134: 0.1uF; C_0402_1005Metric; Tolerance 10%; Voltage 16V; MPN GRM155R71C104KA88
C110: 0.22uF; C_0402_1005Metric; Tolerance 10%; Voltage 16V; MPN GRM155R71C224KA12
C111: 2.2nF; C_0402_1005Metric; Tolerance 2%; Voltage 50V; MPN GRM1555C1H222GA01
C113: 22uF; C_0603_1608Metric; Tolerance 20%; Voltage 10V; MPN GRM188R61A226ME15
D7: ESD9B5.0ST5G; D_SOD-923; MPN ESD9B5.0ST5G
F9: SF-1206S300-2; Fuse_1206_3216Metric; Current Rating 3A; MPN SF-1206S300-2
F10: SF-1206S150-2; Fuse_1206_3216Metric; Current Rating 1.5A; MPN SF-1206S150-2
F14: SF-1206S080-2; Fuse_1206_3216Metric; Current Rating 0.8A; MPN SF-1206S080-2
J6: USB4110; GCT_USB4110GFA; MPN USB4110-GF-A
L3: 1uH; WE-LHMI_4020; MPN 74437324010
R237, R238: 5.1k; R_0402_1005Metric; Tolerance 0.1%; MPN RT0402BRD075K1L
R239: 1M; R_0402_1005Metric; Tolerance 0.1%; MPN MCS0402MD1004BE000
R240: 182k; R_0402_1005Metric; Tolerance 0.1%; MPN RT0402BRD07182KL
R241, R245: 10k; R_0402_1005Metric; Tolerance 1%; MPN RC0402FR-7W10KL
R243: 200k; R_0402_1005Metric; Tolerance 0.1%; MPN RT0402BRD07200KL
R244: 44.2k; R_0402_1005Metric; Tolerance 0.1%; MPN RT0402BRD0744K2L
R246, R247: 10k; R_0402_1005Metric; Tolerance 1%; MPN RC0402FR-7W10KL; not fitted
R248: 0; R_0402_1005Metric; Tolerance Jumper; MPN RC0402JR-070RL
TP40: TestPoint; TestPoint_Pad_D30mil
TP41, TP42, TP43: TestPoint; KEYSTONE_5015; MPN 5015
U4: NX20P5090UK; Manufacturer_Part_Number NX20P5090UK
U12: TLV76033DBZR; TLV76033; MPN TLV76033DBZR
U13: MP2182GTL-Z; SOT583_MP2182_MNP; MPN MP2182GTL-Z

Connections:
GND: C86.2, C87.2, C108.2, C109.2, C110.1, C111.1, C112.2, C113.2, C114.2, C115.2, C133.2, C134.2, D7.1 (A1), J6.A1/B12 (GND), J6.B1/A12 (GND), J6.S1 (GND), J6.S2 (GND), J6.S3 (GND), J6.S4 (GND), R237.1, R238.1, R240.1, R241.1, R244.1, R247.1, U4.C3 (GND_1), U4.D3 (GND_2), U4.E3 (GND_3), U12.3 (GND), U13.4 (GND)
P3V3: C113.1, C114.1, L3.2, R243.2, TP42.1, U13.7 (OUT)
P3V3_EN: C110.2, R245.1, U13.5 (EN)
P3V3_FB: R243.1, R244.2, U13.8 (FB)
P3V3_PGD: R248.2
P3V3_PG_R: R248.1, U13.1 (PG)
P3V3_SNVS: C133.1, C134.1, TP41.1, U12.1 (OUT)
P3V3_SS: C111.2, U13.6 (SS)
P3V3_SW: L3.1, U13.3 (SW)
P5V: C87.1, F10.2, F14.2, R246.2, TP43.1, U4.A1 (VINT_1), U4.B1 (VINT_2), U4.C1 (VINT_3), U4.D1 (VINT_4)
P5V_BUCK3V3_VIN: C112.1, C115.1, F10.1, U13.2 (VIN)
P5V_LDO3V3_VIN: C108.1, C109.1, F14.1, U12.2 (IN)
P5V_VBUS: D7.2 (A2), F9.2, J6.A4/B9 (VBUS), J6.B4/A9 (VBUS)
P5V_VBUS_OVLO: C86.1, F9.1, R239.2, U4.B2 (VBUS_1), U4.C2 (VBUS_2), U4.D2 (VBUS_3), U4.E1 (VBUS_4), U4.E2 (VBUS_5)
PMIC_ON_REQ: R245.2, R246.1, R247.2
USB_PWR_CC1: J6.A5 (CC1), R238.2
USB_PWR_CC2: J6.B5 (CC2), R237.2
VBUS_ACK: TP40.1, U4.A2 (ACK)
VBUS_OVLO: R239.1, R240.2, U4.B3 (OVLO)
~VBUS_EN: R241.2, U4.A3 (/EN)

Notes on the sheet:
USB-C Power Input
V_{ovlo} = V_{th(ovlo)} x (R239 + R240)/R240 V_{ovlo} = 1.227 x (1x10^{6} + 0.182x10^{6})/0.182x10^{6} V_{ovlo} = 7.97V
P3V3_SNVS
P3V3
C111: Soft start time approximately 500us at 2.2nF V_{out} = 0.6 x (R243/R244 + 1) V_{out} = 0.6 x (200/44.2 + 1) V_{out} = 3.315V
