a1wolfe/iMX6-BareBones/Kicad/eMMC.kicad_sch

## KiCad design Kicad/eMMC.kicad_sch (2026-04-23)

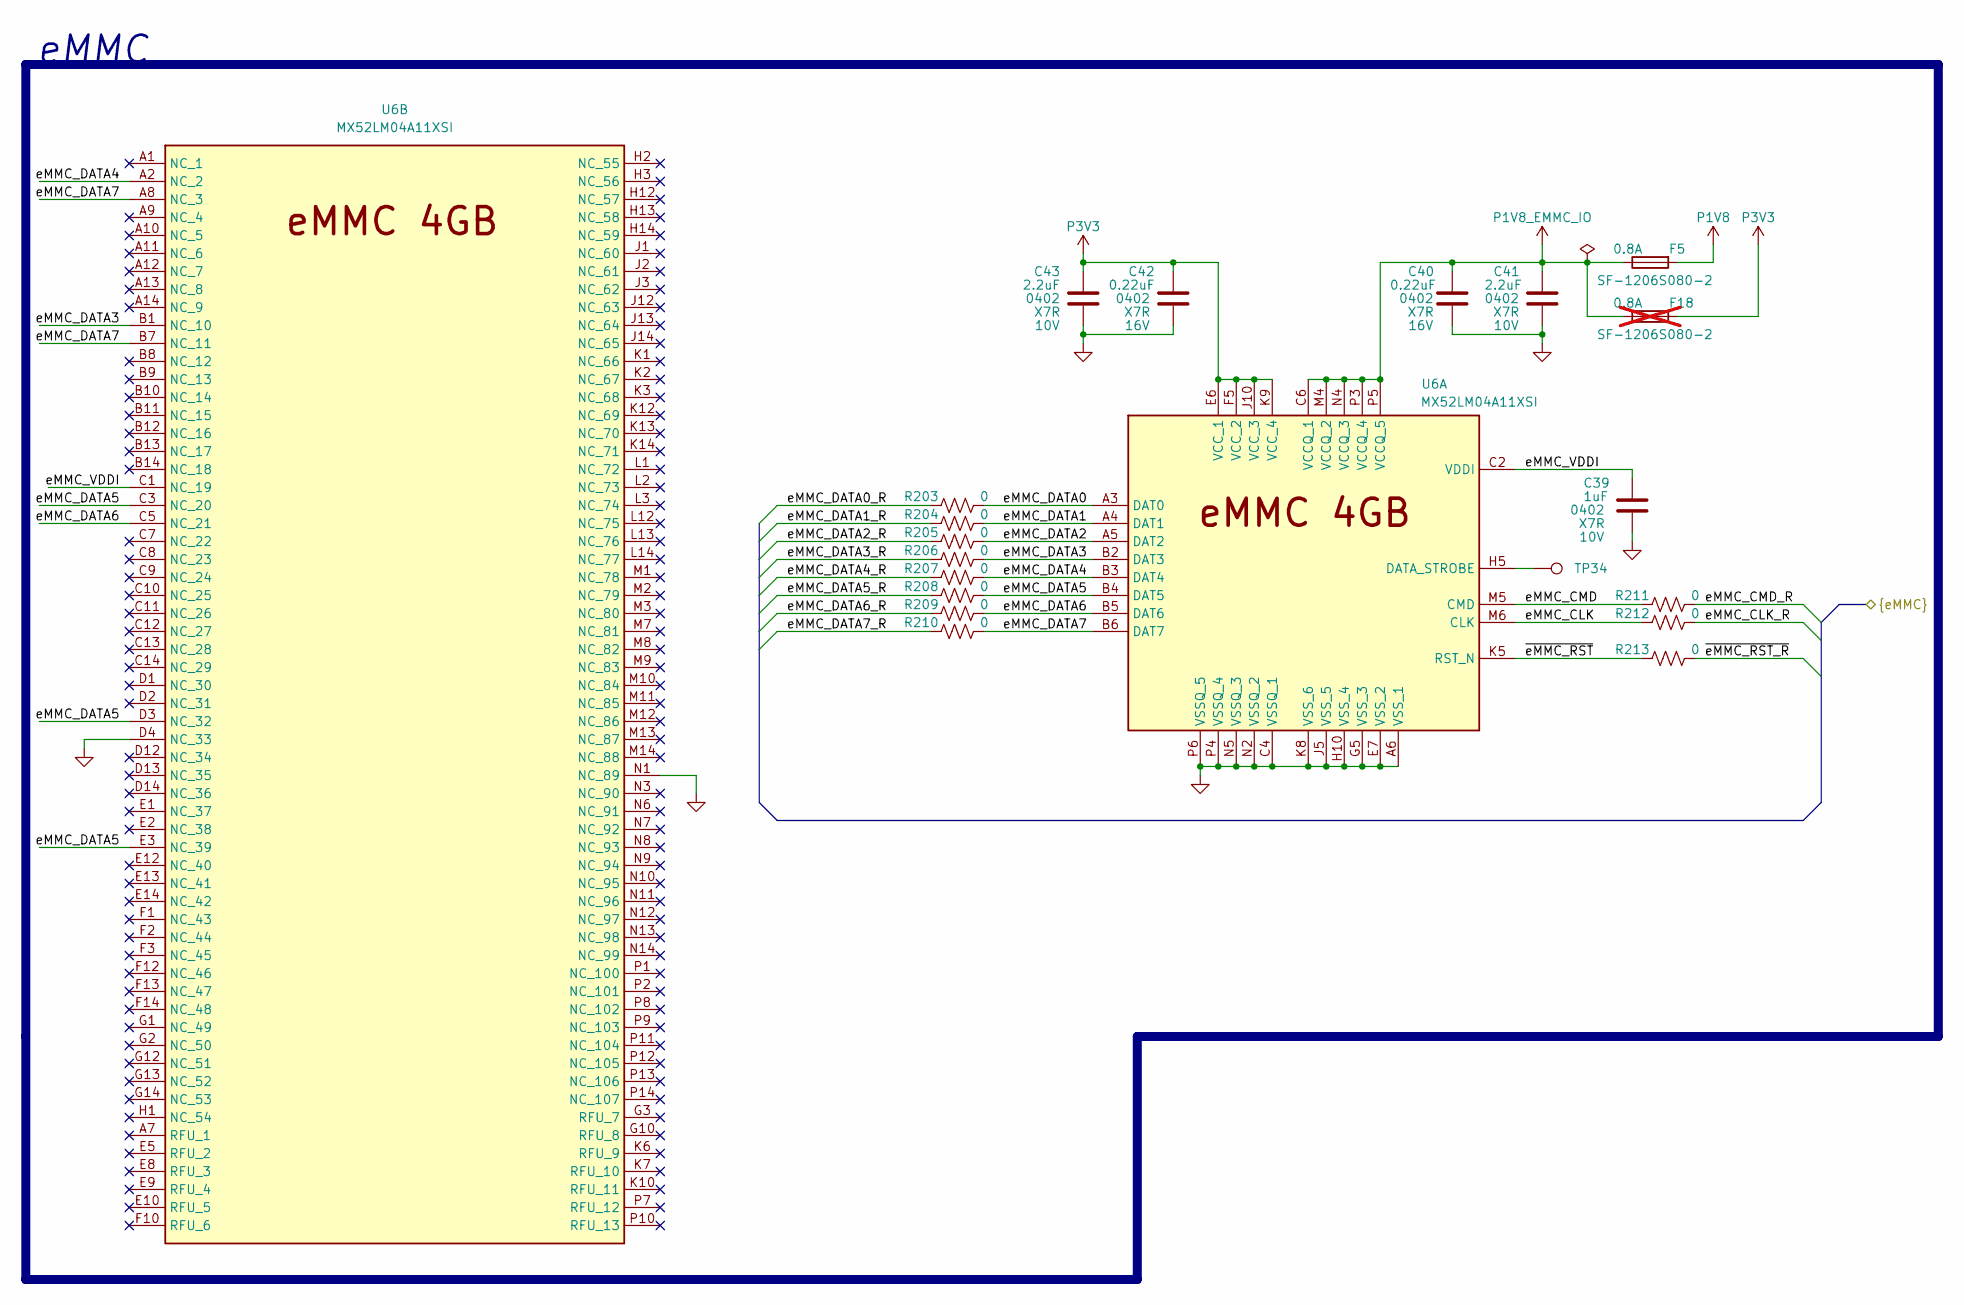
[picture p72: schematic eMMC.kicad_sch]

Parts:
C39: 1uF; C_0402_1005Metric; Tolerance 10%; Voltage 10V; MPN GRM155Z71A105KE01
C40, C42: 0.22uF; C_0402_1005Metric; Tolerance 10%; Voltage 16V; MPN GRM155R71C224KA12
C41, C43: 2.2uF; C_0402_1005Metric; Tolerance 10%; Voltage 10V; MPN GRM155Z71A225KE44
F5: SF-1206S080-2; Fuse_1206_3216Metric; Current Rating 0.8A; MPN SF-1206S080-2
F18: SF-1206S080-2; Fuse_1206_3216Metric; Current Rating 0.8A; MPN SF-1206S080-2; not fitted
R203, R204, R205, R206, R207, R208, R209, R210, R211, R212, R213: 0; R_0402_1005Metric; Tolerance Jumper; MPN RC0402JR-070RL
TP34: TestPoint; TestPoint_Pad_D30mil
U6: MX52LM04A11XSI; eMMC_BGA153C50P14X14_1150X1300X80; MPN MX52LM04A11XSI

Connections:
GND: C39.2, C40.2, C41.2, C42.1, C43.1, U6.A6 (VSS_1), U6.C4 (VSSQ_1), U6.D4 (NC_33), U6.E7 (VSS_2), U6.G5 (VSS_3), U6.H10 (VSS_4), U6.J5 (VSS_5), U6.K8 (VSS_6), U6.N1 (NC_89), U6.N2 (VSSQ_2), U6.N5 (VSSQ_3), U6.P4 (VSSQ_4), U6.P6 (VSSQ_5)
unnamed: TP34.1, U6.H5 (DATA_STROBE)
P1V8: F5.2
P1V8_EMMC_IO: C40.1, C41.1, F5.1, F18.1, U6.C6 (VCCQ_1), U6.M4 (VCCQ_2), U6.N4 (VCCQ_3), U6.P3 (VCCQ_4), U6.P5 (VCCQ_5)
P3V3: C42.2, C43.2, F18.2, U6.E6 (VCC_1), U6.F5 (VCC_2), U6.J10 (VCC_3), U6.K9 (VCC_4)
eMMC_CLK: R212.1, U6.M6 (CLK)
eMMC_CLK_R: R212.2
eMMC_CMD: R211.1, U6.M5 (CMD)
eMMC_CMD_R: R211.2
eMMC_DATA0: R203.2, U6.A3 (DAT0)
eMMC_DATA0_R: R203.1
eMMC_DATA1: R204.2, U6.A4 (DAT1)
eMMC_DATA1_R: R204.1
eMMC_DATA2: R205.2, U6.A5 (DAT2)
eMMC_DATA2_R: R205.1
eMMC_DATA3: R206.2, U6.B1 (NC_10), U6.B2 (DAT3)
eMMC_DATA3_R: R206.1
eMMC_DATA4: R207.2, U6.A2 (NC_2), U6.B3 (DAT4)
eMMC_DATA4_R: R207.1
eMMC_DATA5: R208.2, U6.B4 (DAT5), U6.C3 (NC_20), U6.D3 (NC_32), U6.E3 (NC_39)
eMMC_DATA5_R: R208.1
eMMC_DATA6: R209.2, U6.B5 (DAT6), U6.C5 (NC_21)
eMMC_DATA6_R: R209.1
eMMC_DATA7: R210.2, U6.A8 (NC_3), U6.B6 (DAT7), U6.B7 (NC_11)
eMMC_DATA7_R: R210.1
eMMC_VDDI: C39.1, U6.C1 (NC_19), U6.C2 (VDDI)
~eMMC_RST_R: R213.2
~eMMC_RST: R213.1, U6.K5 (RST_N)

Notes on the sheet:
eMMC
