a1wolfe/iMX6-BareBones/Kicad/iMX6_Control.kicad_sch

## KiCad design Kicad/iMX6_Control.kicad_sch (2026-04-23)

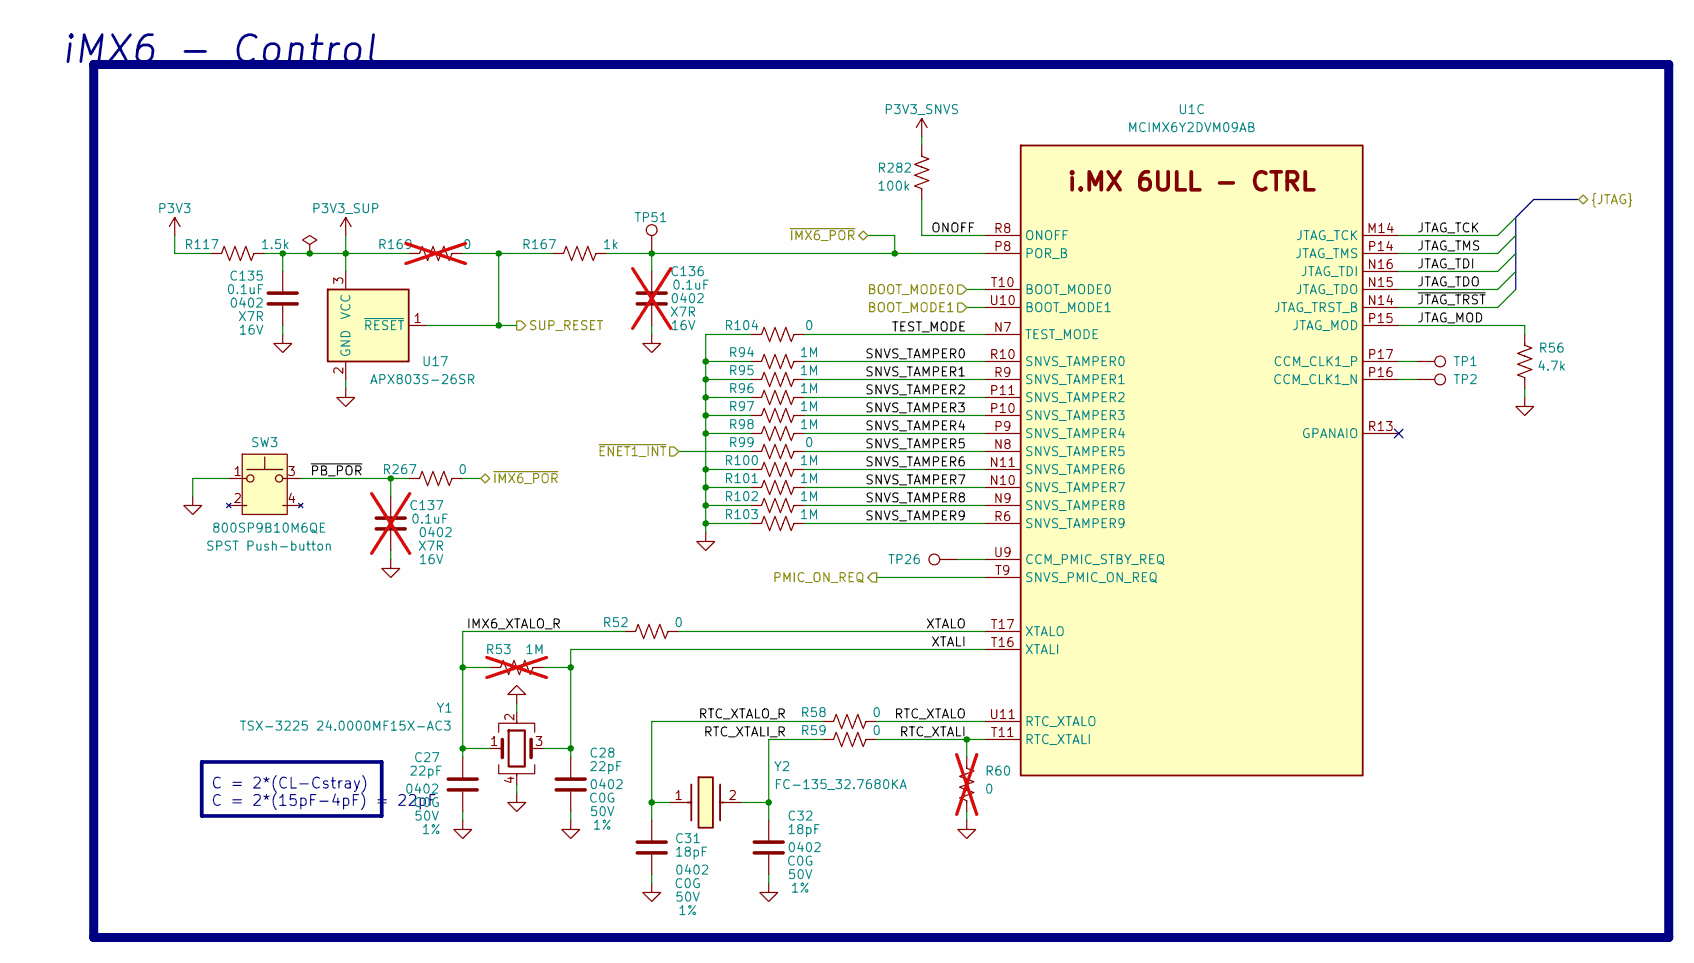
[picture p73: schematic iMX6_Control.kicad_sch]

Parts:
C27, C28: 22pF; C_0402_1005Metric; Tolerance 1%; Voltage 50V; MPN GJM1555C1H220FB01
C31, C32: 18pF; C_0402_1005Metric; Tolerance 1%; Voltage 50V; MPN GJM1555C1H180FB01
C135: 0.1uF; C_0402_1005Metric; Tolerance 10%; Voltage 16V; MPN GRM155R71C104KA88
C136, C137: 0.1uF; C_0402_1005Metric; Tolerance 10%; Voltage 16V; MPN GRM155R71C104KA88; not fitted
R52, R58, R59, R99, R104, R267: 0; R_0402_1005Metric; Tolerance Jumper; MPN RC0402JR-070RL
R53: 1M; R_0402_1005Metric; Tolerance 0.1%; MPN MCS0402MD1004BE000; not fitted
R56: 4.7k; R_0402_1005Metric; Tolerance 1%; MPN RC0402FR-074K7L
R60, R169: 0; R_0402_1005Metric; Tolerance Jumper; MPN RC0402JR-070RL; not fitted
R94, R95, R96, R97, R98, R100, R101, R102, R103: 1M; R_0402_1005Metric; Tolerance 0.1%; MPN MCS0402MD1004BE000
R117: 1.5k; R_0402_1005Metric; Tolerance 0.1%; MPN ERA-2AEB152X
R167: 1k; R_0402_1005Metric; Tolerance 1%; MPN RC0402FR-7W1KL
R282: 100k; R_0402_1005Metric; Tolerance 0.1%; MPN RT0402BRE07100KL
SW3: 800SP9B10M6QE; MPN 800SP9B10M6QE
TP1, TP2, TP26, TP51: TestPoint; TestPoint_Pad_D30mil
U1: MCIMX6Y2DVM09AB; imx6ull_BGA289C80P17X17_1400X1400X132; MPN MCIMX6Y2DVM09AB
U17: APX803S-26SR; APX803; Manufacturer_Part_Number APX803S-29SR-7; Mouser Part Number 621-APX803S-29SR-7
Y1: TSX-3225 24.0000MF15X-AC3; TSX-322524.0000MF15X-AC3; MPN TSX-3225 24.0000MF15X-AC3
Y2: FC-135_32.7680KA; FC135327680KAK0; MPN FC-135_32.7680KA

Connections:
BOOT_MODE0: U1.T10 (BOOT_MODE0)
BOOT_MODE1: U1.U10 (BOOT_MODE1)
GND: C27.2, C28.2, C31.2, C32.2, C135.1, C136.1, C137.1, R56.1, R60.1, R94.1, R95.1, R96.1, R97.1, R98.1, R100.1, R101.1, R102.1, R103.1, R104.1, SW3.1, U17.2 (GND), Y1.2, Y1.4
IMX6_XTALO_R: C27.1, R52.1, R53.1, Y1.1
JTAG_MOD: R56.2, U1.P15 (JTAG_MOD)
JTAG_TCK: U1.M14 (JTAG_TCK)
JTAG_TDI: U1.N16 (JTAG_TDI)
JTAG_TDO: U1.N15 (JTAG_TDO)
JTAG_TMS: U1.P14 (JTAG_TMS)
unnamed: TP1.1, U1.P17 (CCM_CLK1_P)
unnamed: TP2.1, U1.P16 (CCM_CLK1_N)
unnamed: TP26.1, U1.U9 (CCM_PMIC_STBY_REQ)
ONOFF: R282.2, U1.R8 (ONOFF)
P3V3: R117.2
P3V3_SNVS: R282.1
P3V3_SUP: C135.2, R117.1, R169.1, U17.3 (VCC)
PMIC_ON_REQ: U1.T9 (SNVS_PMIC_ON_REQ)
RTC_XTALI: R59.2, R60.2, U1.T11 (RTC_XTALI)
RTC_XTALI_R: C32.1, R59.1, Y2.2
RTC_XTALO: R58.2, U1.U11 (RTC_XTALO)
RTC_XTALO_R: C31.1, R58.1, Y2.1 (CRYSTAL_2)
SNVS_TAMPER0: R94.2, U1.R10 (SNVS_TAMPER0)
SNVS_TAMPER1: R95.2, U1.R9 (SNVS_TAMPER1)
SNVS_TAMPER2: R96.2, U1.P11 (SNVS_TAMPER2)
SNVS_TAMPER3: R97.2, U1.P10 (SNVS_TAMPER3)
SNVS_TAMPER4: R98.2, U1.P9 (SNVS_TAMPER4)
SNVS_TAMPER5: R99.2, U1.N8 (SNVS_TAMPER5)
SNVS_TAMPER6: R100.2, U1.N11 (SNVS_TAMPER6)
SNVS_TAMPER7: R101.2, U1.N10 (SNVS_TAMPER7)
SNVS_TAMPER8: R102.2, U1.N9 (SNVS_TAMPER8)
SNVS_TAMPER9: R103.2, U1.R6 (SNVS_TAMPER9)
SUP_RESET: R167.2, R169.2, U17.1 (~RESET)
TEST_MODE: R104.2, U1.N7 (TEST_MODE)
XTALI: C28.1, R53.2, U1.T16 (XTALI), Y1.3
XTALO: R52.2, U1.T17 (XTALO)
~ENET1_INT: R99.1
~IMX6_POR: C136.2, R167.1, R267.2, TP51.1, U1.P8 (POR_B)
~JTAG_TRST: U1.N14 (JTAG_TRST_B)
~PB_POR: C137.2, R267.1, SW3.3

Notes on the sheet:
C = 2*(CL-Cstray) C = 2*(15pF-4pF) = 22pF
iMX6 - Control
