a1wolfe/iMX6-BareBones/Kicad/iMX6_DDR3L.kicad_sch

## KiCad design Kicad/iMX6_DDR3L.kicad_sch (2026-04-23)

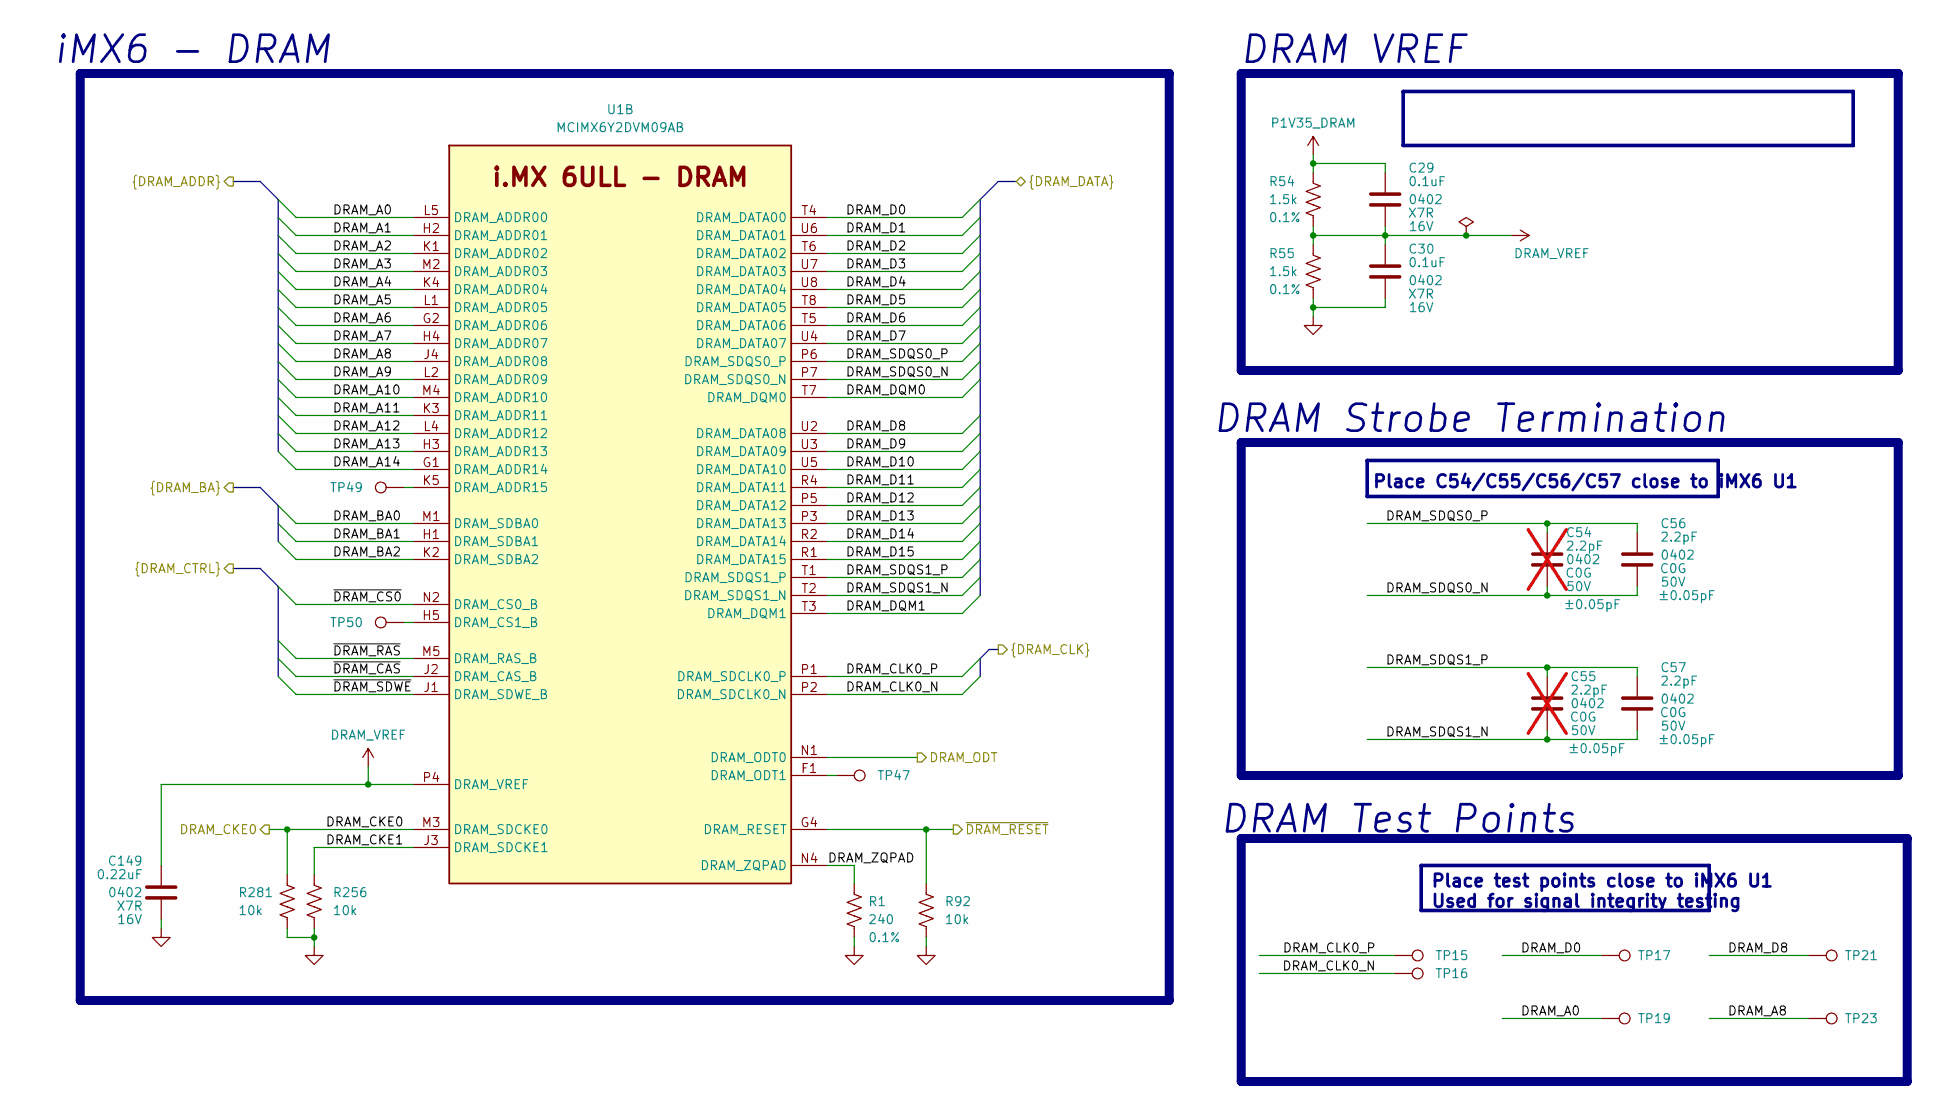
[picture p74: schematic iMX6_DDR3L.kicad_sch]

Parts:
C29, C30: 0.1uF; C_0402_1005Metric; Tolerance 10%; Voltage 16V; MPN GRM155R71C104KA88
C54, C55: 2.2pF; C_0402_1005Metric; Tolerance ±0.05pF; Voltage 50V; MPN GJM1555C1H2R2WB01; not fitted
C56, C57: 2.2pF; C_0402_1005Metric; Tolerance ±0.05pF; Voltage 50V; MPN GJM1555C1H2R2WB01
C149: 0.22uF; C_0402_1005Metric; Tolerance 10%; Voltage 16V; MPN GRM155R71C224KA12
R1: 240; R_0402_1005Metric; Tolerance 0.1%; MPN RT0402BRD07240RL
R54, R55: 1.5k; R_0402_1005Metric; Tolerance 0.1%; MPN ERA-2AEB152X
R92, R256, R281: 10k; R_0402_1005Metric; Tolerance 1%; MPN RC0402FR-7W10KL
TP15, TP16, TP17, TP19, TP21, TP23, TP47, TP49, TP50: TestPoint; TestPoint_Pad_D18mil
U1: MCIMX6Y2DVM09AB; imx6ull_BGA289C80P17X17_1400X1400X132; MPN MCIMX6Y2DVM09AB

Connections:
DRAM_A0: TP19.1, U1.L5 (DRAM_ADDR00)
DRAM_A1: U1.H2 (DRAM_ADDR01)
DRAM_A2: U1.K1 (DRAM_ADDR02)
DRAM_A3: U1.M2 (DRAM_ADDR03)
DRAM_A4: U1.K4 (DRAM_ADDR04)
DRAM_A5: U1.L1 (DRAM_ADDR05)
DRAM_A6: U1.G2 (DRAM_ADDR06)
DRAM_A7: U1.H4 (DRAM_ADDR07)
DRAM_A8: TP23.1, U1.J4 (DRAM_ADDR08)
DRAM_A9: U1.L2 (DRAM_ADDR09)
DRAM_A10: U1.M4 (DRAM_ADDR10)
DRAM_A11: U1.K3 (DRAM_ADDR11)
DRAM_A12: U1.L4 (DRAM_ADDR12)
DRAM_A13: U1.H3 (DRAM_ADDR13)
DRAM_A14: U1.G1 (DRAM_ADDR14)
DRAM_BA0: U1.M1 (DRAM_SDBA0)
DRAM_BA1: U1.H1 (DRAM_SDBA1)
DRAM_BA2: U1.K2 (DRAM_SDBA2)
DRAM_CKE0: R281.1, U1.M3 (DRAM_SDCKE0)
DRAM_CKE1: R256.1, U1.J3 (DRAM_SDCKE1)
DRAM_CLK0_N: TP16.1, U1.P2 (DRAM_SDCLK0_N)
DRAM_CLK0_P: TP15.1, U1.P1 (DRAM_SDCLK0_P)
DRAM_D0: TP17.1, U1.T4 (DRAM_DATA00)
DRAM_D1: U1.U6 (DRAM_DATA01)
DRAM_D2: U1.T6 (DRAM_DATA02)
DRAM_D3: U1.U7 (DRAM_DATA03)
DRAM_D4: U1.U8 (DRAM_DATA04)
DRAM_D5: U1.T8 (DRAM_DATA05)
DRAM_D6: U1.T5 (DRAM_DATA06)
DRAM_D7: U1.U4 (DRAM_DATA07)
DRAM_D8: TP21.1, U1.U2 (DRAM_DATA08)
DRAM_D9: U1.U3 (DRAM_DATA09)
DRAM_D10: U1.U5 (DRAM_DATA10)
DRAM_D11: U1.R4 (DRAM_DATA11)
DRAM_D12: U1.P5 (DRAM_DATA12)
DRAM_D13: U1.P3 (DRAM_DATA13)
DRAM_D14: U1.R2 (DRAM_DATA14)
DRAM_D15: U1.R1 (DRAM_DATA15)
DRAM_DQM0: U1.T7 (DRAM_DQM0)
DRAM_DQM1: U1.T3 (DRAM_DQM1)
DRAM_ODT: U1.N1 (DRAM_ODT0)
DRAM_SDQS0_N: C54.2, C56.2, U1.P7 (DRAM_SDQS0_N)
DRAM_SDQS0_P: C54.1, C56.1, U1.P6 (DRAM_SDQS0_P)
DRAM_SDQS1_N: C55.2, C57.2, U1.T2 (DRAM_SDQS1_N)
DRAM_SDQS1_P: C55.1, C57.1, U1.T1 (DRAM_SDQS1_P)
DRAM_VREF: C29.2, C30.1, C149.2, R54.2, R55.1, U1.P4 (DRAM_VREF)
DRAM_ZQPAD: R1.1, U1.N4 (DRAM_ZQPAD)
GND: C30.2, C149.1, R1.2, R55.2, R92.2, R256.2, R281.2
unnamed: TP47.1, U1.F1 (DRAM_ODT1)
unnamed: TP49.1, U1.K5 (DRAM_ADDR15)
unnamed: TP50.1, U1.H5 (DRAM_CS1_B)
P1V35_DRAM: C29.1, R54.1
~DRAM_CAS: U1.J2 (DRAM_CAS_B)
~DRAM_CS0: U1.N2 (DRAM_CS0_B)
~DRAM_RAS: U1.M5 (DRAM_RAS_B)
~DRAM_RESET: R92.1, U1.G4 (DRAM_RESET)
~DRAM_SDWE: U1.J1 (DRAM_SDWE_B)

Notes on the sheet:
iMX6 - DRAM
DRAM Strobe Termination
Place test points close to iMX6 U1 Used for signal integrity testing
DRAM Test Points
DRAM VREF
Place C54/C55/C56/C57 close to iMX6 U1
