a1wolfe/iMX6-BareBones/Kicad/iMX6_Ethernet.kicad_sch

## KiCad design Kicad/iMX6_Ethernet.kicad_sch (2026-04-23)

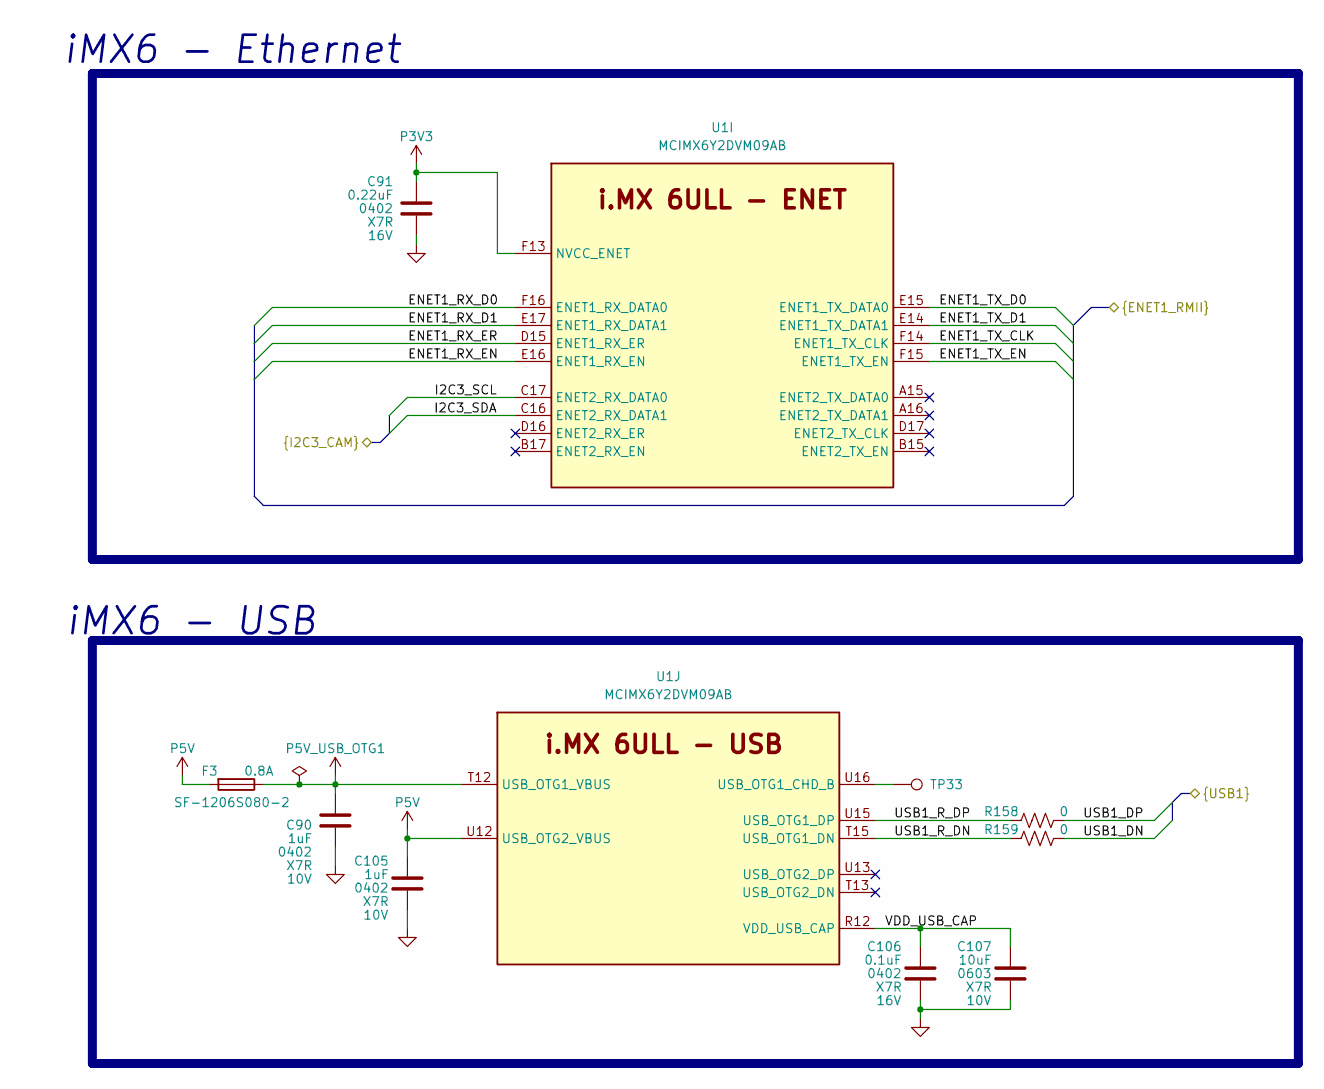
[picture p75: schematic iMX6_Ethernet.kicad_sch]

Parts:
C90, C105: 1uF; C_0402_1005Metric; Voltage 10V; Tolerance 10%; MPN GRM155Z71A105KE01
C91: 0.22uF; C_0402_1005Metric; Tolerance 10%; Voltage 16V; MPN GRM155R71C224KA12
C106: 0.1uF; C_0402_1005Metric; Tolerance 10%; Voltage 16V; MPN GRM155R71C104KA88
C107: 10uF; C_0603_1608Metric; Tolerance 10%; Voltage 10V; MPN GRM188Z71A106KA73
F3: SF-1206S080-2; Fuse_1206_3216Metric; Current Rating 0.8A; MPN SF-1206S080-2
R158, R159: 0; R_0402_1005Metric; Tolerance Jumper; MPN RC0402JR-070RL
TP33: TestPoint; TestPoint_Pad_D30mil
U1: MCIMX6Y2DVM09AB; imx6ull_BGA289C80P17X17_1400X1400X132; MPN MCIMX6Y2DVM09AB

Connections:
ENET1_RX_D0: U1.F16 (ENET1_RX_DATA0)
ENET1_RX_D1: U1.E17 (ENET1_RX_DATA1)
ENET1_RX_EN: U1.E16 (ENET1_RX_EN)
ENET1_RX_ER: U1.D15 (ENET1_RX_ER)
ENET1_TX_CLK: U1.F14 (ENET1_TX_CLK)
ENET1_TX_D0: U1.E15 (ENET1_TX_DATA0)
ENET1_TX_D1: U1.E14 (ENET1_TX_DATA1)
ENET1_TX_EN: U1.F15 (ENET1_TX_EN)
GND: C90.1, C91.1, C105.1, C106.1, C107.1
I2C3_SCL: U1.C17 (ENET2_RX_DATA0)
I2C3_SDA: U1.C16 (ENET2_RX_DATA1)
unnamed: TP33.1, U1.U16 (USB_OTG1_CHD_B)
P3V3: C91.2, U1.F13 (NVCC_ENET)
P5V: C105.2, F3.2, U1.U12 (USB_OTG2_VBUS)
P5V_USB_OTG1: C90.2, F3.1, U1.T12 (USB_OTG1_VBUS)
USB1_DN: R159.2
USB1_DP: R158.2
USB1_R_DN: R159.1, U1.T15 (USB_OTG1_DN)
USB1_R_DP: R158.1, U1.U15 (USB_OTG1_DP)
VDD_USB_CAP: C106.2, C107.2, U1.R12 (VDD_USB_CAP)

Notes on the sheet:
iMX6 - USB
iMX6 - Ethernet
