a1wolfe/iMX6-BareBones/Kicad/iMX6_GPIO_UART.kicad_sch

## KiCad design Kicad/iMX6_GPIO_UART.kicad_sch (2026-04-23)

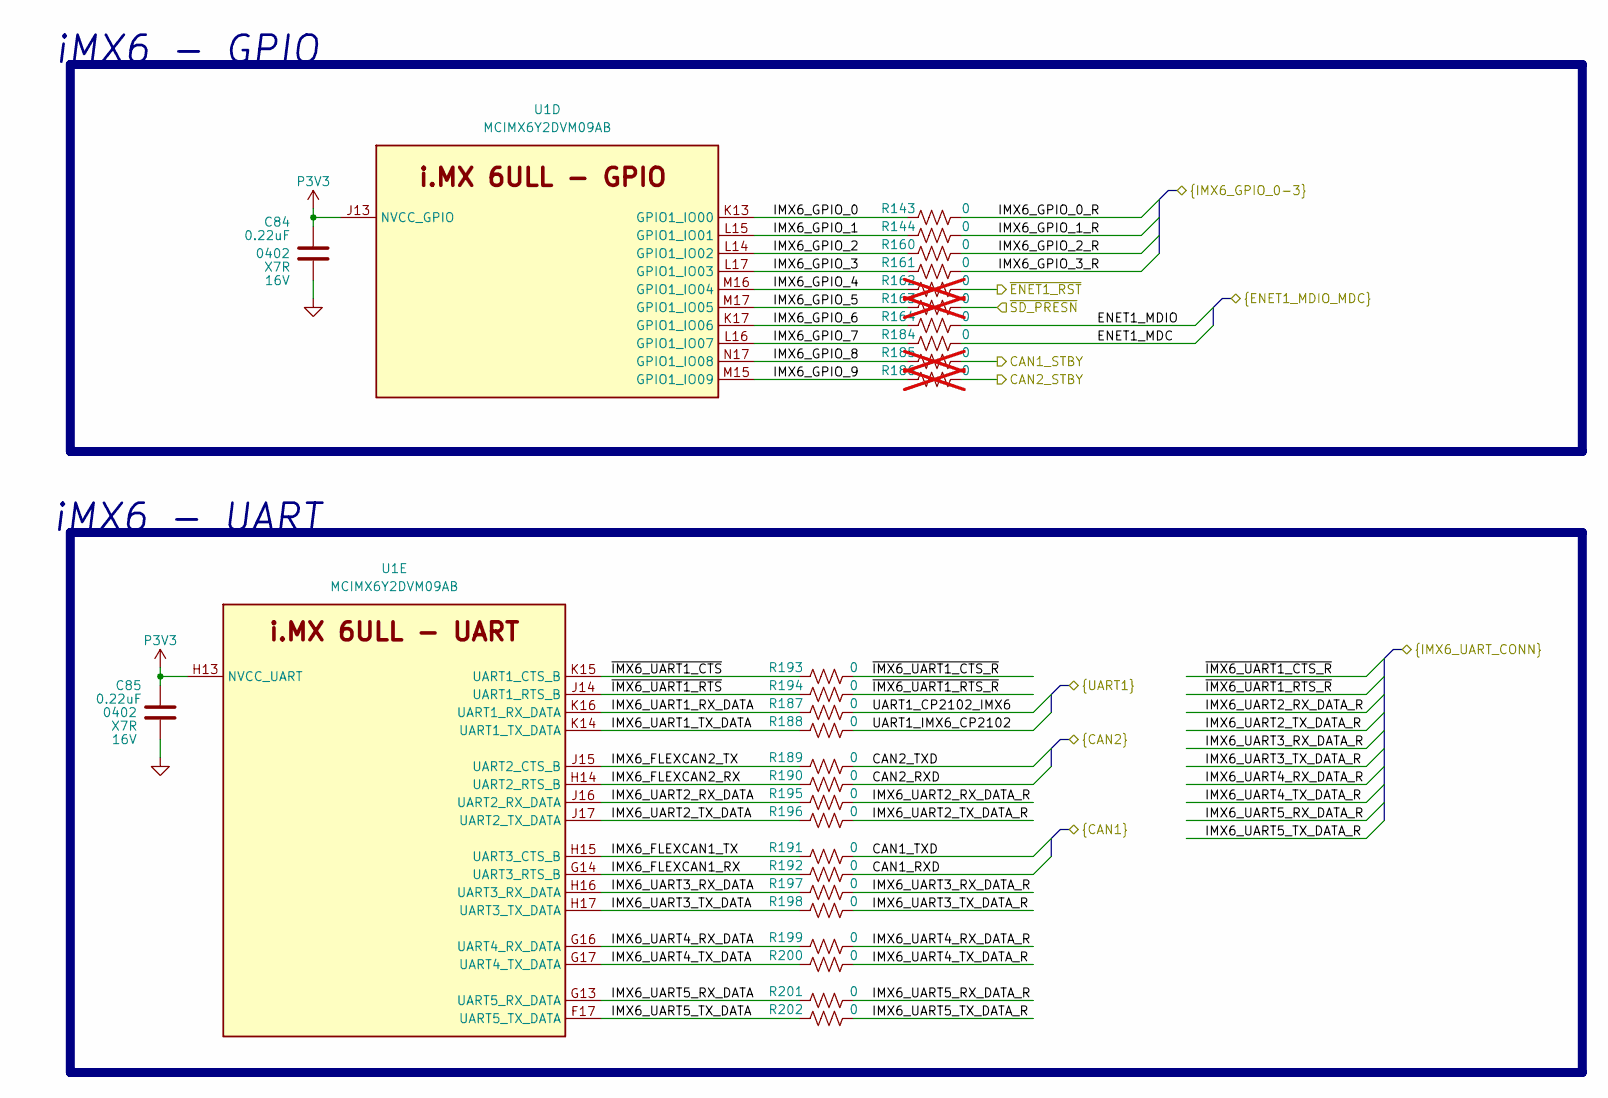
[picture p76: schematic iMX6_GPIO_UART.kicad_sch]

Parts:
C84, C85: 0.22uF; C_0402_1005Metric; Tolerance 10%; Voltage 16V; MPN GRM155R71C224KA12
R143, R144, R160, R161, R164, R184, R187, R188, R189, R190, R191, R192, R193, R194, R195, R196, R197, R198, R199, R200, R201, R202: 0; R_0402_1005Metric; Tolerance Jumper; MPN RC0402JR-070RL
R162, R163, R185, R186: 0; R_0402_1005Metric; Tolerance Jumper; MPN RC0402JR-070RL; not fitted
U1: MCIMX6Y2DVM09AB; imx6ull_BGA289C80P17X17_1400X1400X132; MPN MCIMX6Y2DVM09AB

Connections:
CAN1_RXD: R192.1
CAN1_STBY: R185.2
CAN1_TXD: R191.1
CAN2_RXD: R190.1
CAN2_STBY: R186.2
CAN2_TXD: R189.1
ENET1_MDC: R184.2
ENET1_MDIO: R164.2
GND: C84.1, C85.1
IMX6_FLEXCAN1_RX: R192.2, U1.G14 (UART3_RTS_B)
IMX6_FLEXCAN1_TX: R191.2, U1.H15 (UART3_CTS_B)
IMX6_FLEXCAN2_RX: R190.2, U1.H14 (UART2_RTS_B)
IMX6_FLEXCAN2_TX: R189.2, U1.J15 (UART2_CTS_B)
IMX6_GPIO_0: R143.1, U1.K13 (GPIO1_IO00)
IMX6_GPIO_0_R: R143.2
IMX6_GPIO_1: R144.1, U1.L15 (GPIO1_IO01)
IMX6_GPIO_1_R: R144.2
IMX6_GPIO_2: R160.1, U1.L14 (GPIO1_IO02)
IMX6_GPIO_2_R: R160.2
IMX6_GPIO_3: R161.1, U1.L17 (GPIO1_IO03)
IMX6_GPIO_3_R: R161.2
IMX6_GPIO_4: R162.1, U1.M16 (GPIO1_IO04)
IMX6_GPIO_5: R163.1, U1.M17 (GPIO1_IO05)
IMX6_GPIO_6: R164.1, U1.K17 (GPIO1_IO06)
IMX6_GPIO_7: R184.1, U1.L16 (GPIO1_IO07)
IMX6_GPIO_8: R185.1, U1.N17 (GPIO1_IO08)
IMX6_GPIO_9: R186.1, U1.M15 (GPIO1_IO09)
IMX6_UART1_RX_DATA: R187.2, U1.K16 (UART1_RX_DATA)
IMX6_UART1_TX_DATA: R188.2, U1.K14 (UART1_TX_DATA)
IMX6_UART2_RX_DATA: R195.2, U1.J16 (UART2_RX_DATA)
IMX6_UART2_RX_DATA_R: R195.1
IMX6_UART2_TX_DATA: R196.2, U1.J17 (UART2_TX_DATA)
IMX6_UART2_TX_DATA_R: R196.1
IMX6_UART3_RX_DATA: R197.2, U1.H16 (UART3_RX_DATA)
IMX6_UART3_RX_DATA_R: R197.1
IMX6_UART3_TX_DATA: R198.2, U1.H17 (UART3_TX_DATA)
IMX6_UART3_TX_DATA_R: R198.1
IMX6_UART4_RX_DATA: R199.2, U1.G16 (UART4_RX_DATA)
IMX6_UART4_RX_DATA_R: R199.1
IMX6_UART4_TX_DATA: R200.2, U1.G17 (UART4_TX_DATA)
IMX6_UART4_TX_DATA_R: R200.1
IMX6_UART5_RX_DATA: R201.2, U1.G13 (UART5_RX_DATA)
IMX6_UART5_RX_DATA_R: R201.1
IMX6_UART5_TX_DATA: R202.2, U1.F17 (UART5_TX_DATA)
IMX6_UART5_TX_DATA_R: R202.1
P3V3: C84.2, C85.2, U1.H13 (NVCC_UART), U1.J13 (NVCC_GPIO)
UART1_CP2102_IMX6: R187.1
UART1_IMX6_CP2102: R188.1
~ENET1_RST: R162.2
~IMX6_UART1_CTS_R: R193.1
~IMX6_UART1_CTS: R193.2, U1.K15 (UART1_CTS_B)
~IMX6_UART1_RTS_R: R194.1
~IMX6_UART1_RTS: R194.2, U1.J14 (UART1_RTS_B)
~SD_PRESN: R163.2

Notes on the sheet:
iMX6 - UART
iMX6 - GPIO
