a1wolfe/iMX6-BareBones/Kicad/iMX6_Periphs.kicad_sch

## KiCad design Kicad/iMX6_Periphs.kicad_sch (2026-04-23)

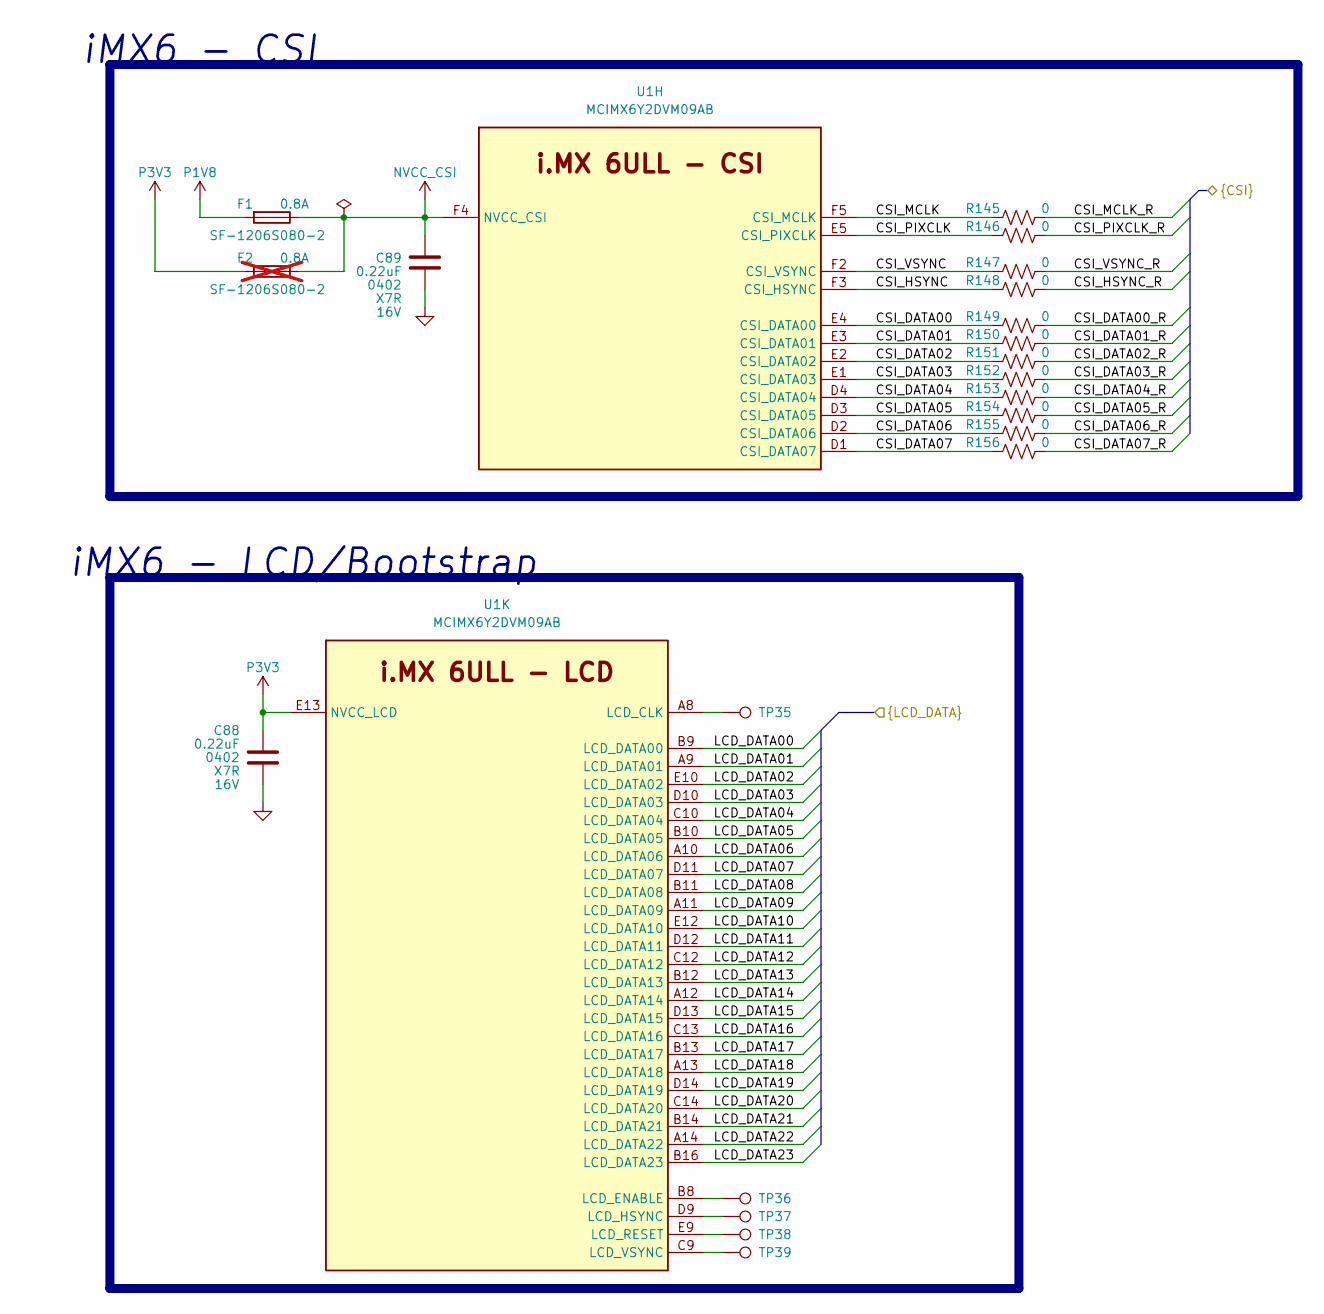
[picture p77: schematic iMX6_Periphs.kicad_sch]

Parts:
C88, C89: 0.22uF; C_0402_1005Metric; Tolerance 10%; Voltage 16V; MPN GRM155R71C224KA12
F1: SF-1206S080-2; Fuse_1206_3216Metric; Current Rating 0.8A; MPN SF-1206S080-2
F2: SF-1206S080-2; Fuse_1206_3216Metric; Current Rating 0.8A; MPN SF-1206S080-2; not fitted
R145, R146, R147, R148, R149, R150, R151, R152, R153, R154, R155, R156: 0; R_0402_1005Metric; Tolerance Jumper; MPN RC0402JR-070RL
TP35, TP36, TP37, TP38, TP39: TestPoint; TestPoint_Pad_D30mil
U1: MCIMX6Y2DVM09AB; imx6ull_BGA289C80P17X17_1400X1400X132; MPN MCIMX6Y2DVM09AB

Connections:
CSI_DATA00: R149.1, U1.E4 (CSI_DATA00)
CSI_DATA00_R: R149.2
CSI_DATA01: R150.1, U1.E3 (CSI_DATA01)
CSI_DATA01_R: R150.2
CSI_DATA02: R151.1, U1.E2 (CSI_DATA02)
CSI_DATA02_R: R151.2
CSI_DATA03: R152.1, U1.E1 (CSI_DATA03)
CSI_DATA03_R: R152.2
CSI_DATA04: R153.1, U1.D4 (CSI_DATA04)
CSI_DATA04_R: R153.2
CSI_DATA05: R154.1, U1.D3 (CSI_DATA05)
CSI_DATA05_R: R154.2
CSI_DATA06: R155.1, U1.D2 (CSI_DATA06)
CSI_DATA06_R: R155.2
CSI_DATA07: R156.1, U1.D1 (CSI_DATA07)
CSI_DATA07_R: R156.2
CSI_HSYNC: R148.1, U1.F3 (CSI_HSYNC)
CSI_HSYNC_R: R148.2
CSI_MCLK: R145.1, U1.F5 (CSI_MCLK)
CSI_MCLK_R: R145.2
CSI_PIXCLK: R146.1, U1.E5 (CSI_PIXCLK)
CSI_PIXCLK_R: R146.2
CSI_VSYNC: R147.1, U1.F2 (CSI_VSYNC)
CSI_VSYNC_R: R147.2
GND: C88.1, C89.1
LCD_DATA00: U1.B9 (LCD_DATA00)
LCD_DATA01: U1.A9 (LCD_DATA01)
LCD_DATA02: U1.E10 (LCD_DATA02)
LCD_DATA03: U1.D10 (LCD_DATA03)
LCD_DATA04: U1.C10 (LCD_DATA04)
LCD_DATA05: U1.B10 (LCD_DATA05)
LCD_DATA06: U1.A10 (LCD_DATA06)
LCD_DATA07: U1.D11 (LCD_DATA07)
LCD_DATA08: U1.B11 (LCD_DATA08)
LCD_DATA09: U1.A11 (LCD_DATA09)
LCD_DATA10: U1.E12 (LCD_DATA10)
LCD_DATA11: U1.D12 (LCD_DATA11)
LCD_DATA12: U1.C12 (LCD_DATA12)
LCD_DATA13: U1.B12 (LCD_DATA13)
LCD_DATA14: U1.A12 (LCD_DATA14)
LCD_DATA15: U1.D13 (LCD_DATA15)
LCD_DATA16: U1.C13 (LCD_DATA16)
LCD_DATA17: U1.B13 (LCD_DATA17)
LCD_DATA18: U1.A13 (LCD_DATA18)
LCD_DATA19: U1.D14 (LCD_DATA19)
LCD_DATA20: U1.C14 (LCD_DATA20)
LCD_DATA21: U1.B14 (LCD_DATA21)
LCD_DATA22: U1.A14 (LCD_DATA22)
LCD_DATA23: U1.B16 (LCD_DATA23)
NVCC_CSI: C89.2, F1.1, F2.1, U1.F4 (NVCC_CSI)
unnamed: TP35.1, U1.A8 (LCD_CLK)
unnamed: TP36.1, U1.B8 (LCD_ENABLE)
unnamed: TP37.1, U1.D9 (LCD_HSYNC)
unnamed: TP38.1, U1.E9 (LCD_RESET)
unnamed: TP39.1, U1.C9 (LCD_VSYNC)
P1V8: F1.2
P3V3: C88.2, F2.2, U1.E13 (NVCC_LCD)

Notes on the sheet:
iMX6 - LCD/Bootstrap
iMX6 - CSI
