a1wolfe/iMX6-BareBones/Kicad/iMX6_Power.kicad_sch

## KiCad design Kicad/iMX6_Power.kicad_sch (2026-04-23)

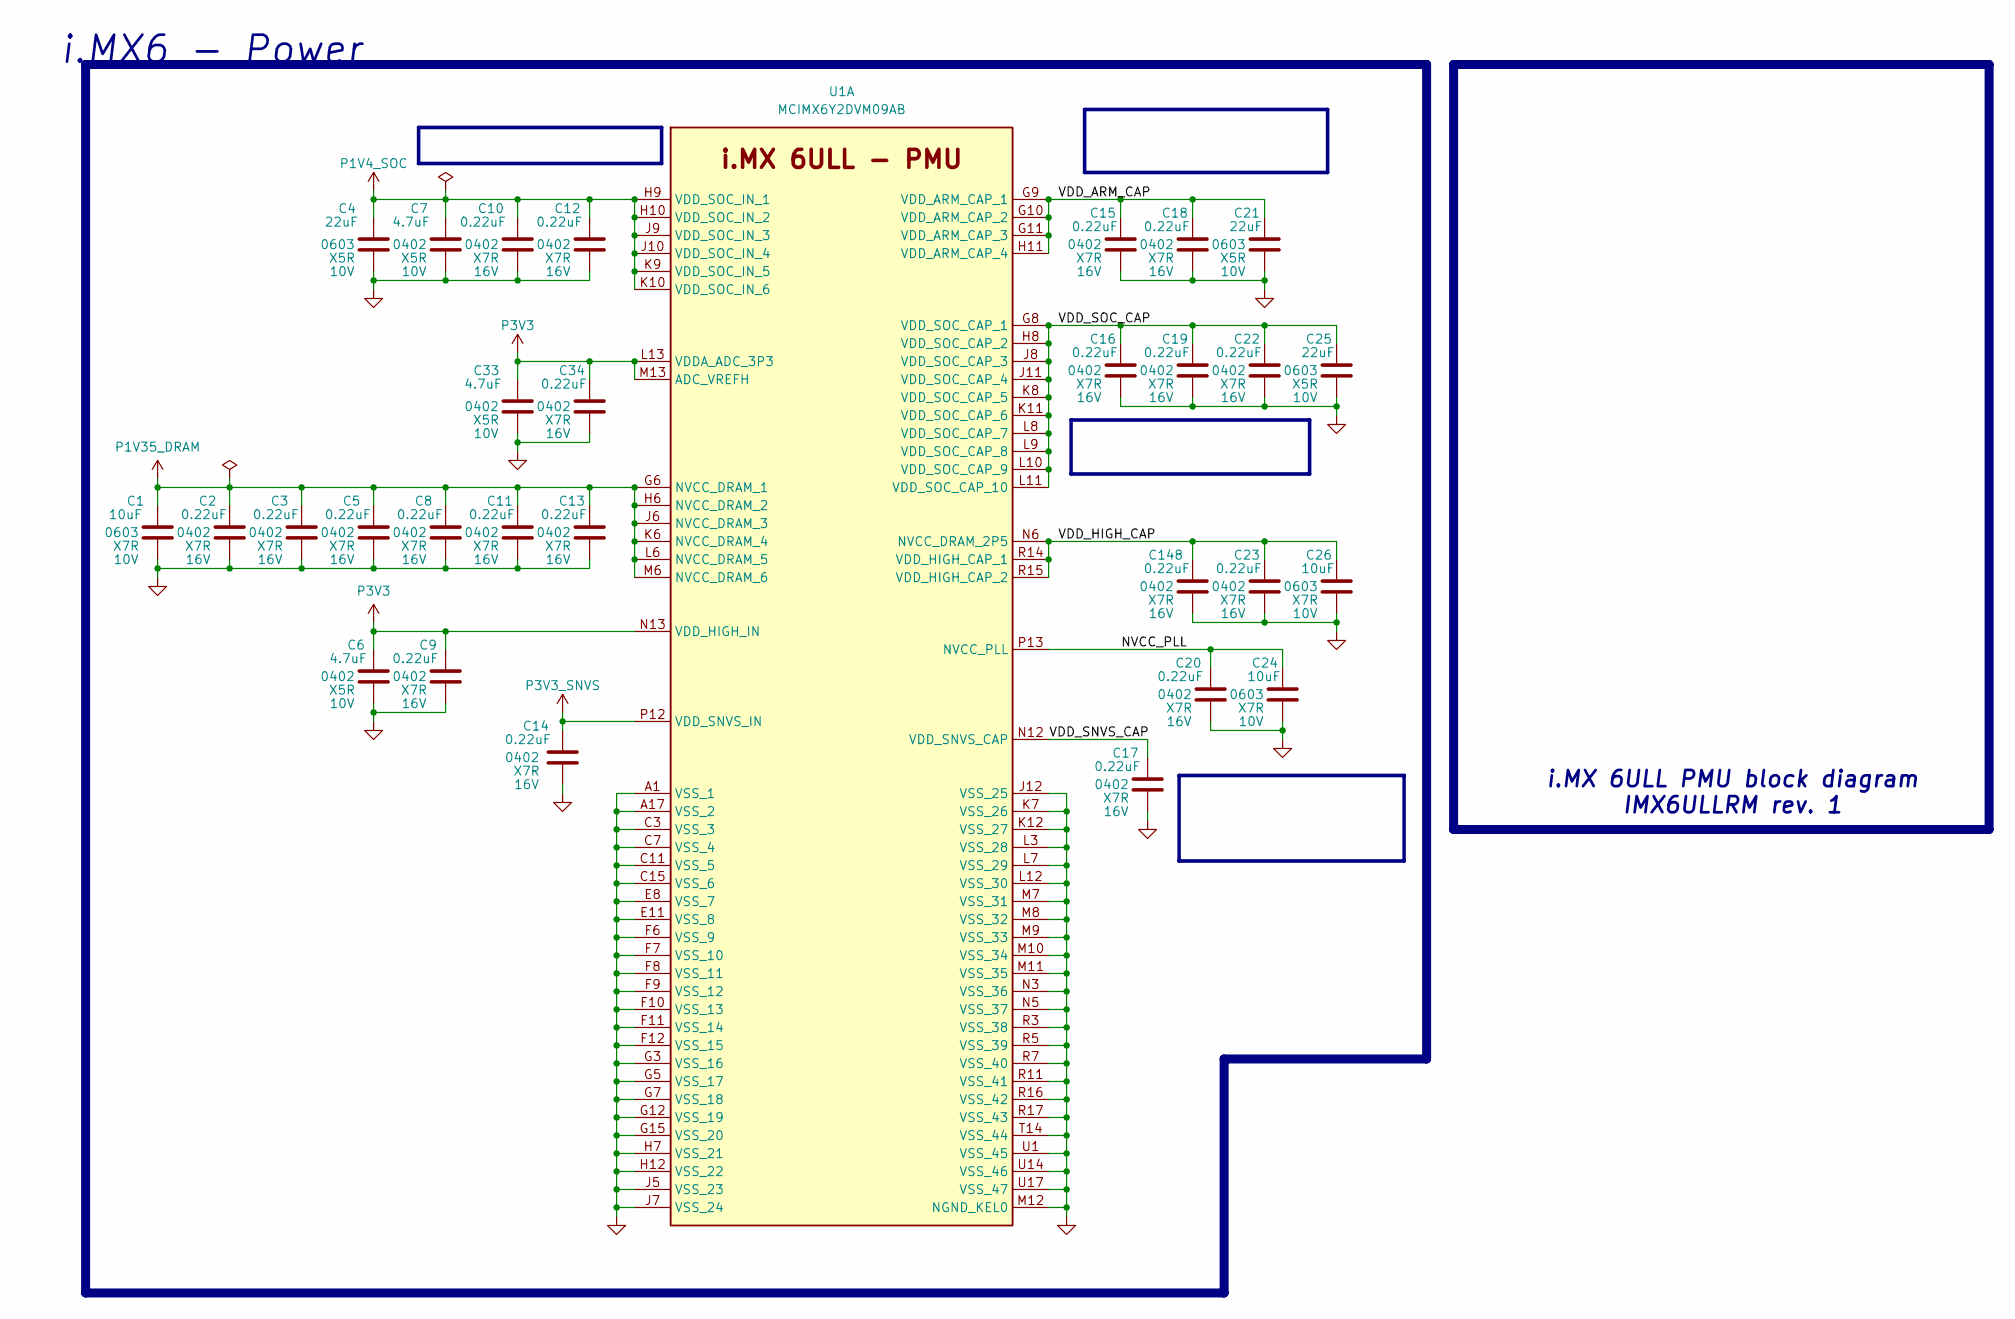
[picture p78: schematic iMX6_Power.kicad_sch]

Parts:
C1, C24, C26: 10uF; C_0603_1608Metric; Tolerance 10%; Voltage 10V; MPN GRM188Z71A106KA73
C2, C3, C5, C8, C9, C10, C11, C12, C13, C14, C15, C16, C17, C18, C19, C20, C22, C23, C34, C148: 0.22uF; C_0402_1005Metric; Tolerance 10%; Voltage 16V; MPN GRM155R71C224KA12
C4, C21, C25: 22uF; C_0603_1608Metric; Tolerance 20%; Voltage 10V; MPN GRM188R61A226ME15
C6, C7, C33: 4.7uF; C_0402_1005Metric; Tolerance 20%; Voltage 10V; MPN GRM155R61A475MEA
U1: MCIMX6Y2DVM09AB; imx6ull_BGA289C80P17X17_1400X1400X132; MPN MCIMX6Y2DVM09AB

Connections:
GND: C1.2, C2.2, C3.2, C4.2, C5.2, C6.2, C7.2, C8.2, C9.2, C10.2, C11.2, C12.2, C13.2, C14.2, C15.2, C16.2, C17.2, C18.2, C19.2, C20.2, C21.2, C22.2, C23.2, C24.2, C25.2, C26.2, C33.2, C34.2, C148.2, U1.A1 (VSS_1), U1.A17 (VSS_2), U1.C3 (VSS_3), U1.C7 (VSS_4), U1.C11 (VSS_5), U1.C15 (VSS_6), U1.E8 (VSS_7), U1.E11 (VSS_8), U1.F6 (VSS_9), U1.F7 (VSS_10), U1.F8 (VSS_11), U1.F9 (VSS_12), U1.F10 (VSS_13), U1.F11 (VSS_14), U1.F12 (VSS_15), U1.G3 (VSS_16), U1.G5 (VSS_17), U1.G7 (VSS_18), U1.G12 (VSS_19), U1.G15 (VSS_20), U1.H7 (VSS_21), U1.H12 (VSS_22), U1.J5 (VSS_23), U1.J7 (VSS_24), U1.J12 (VSS_25), U1.K7 (VSS_26), U1.K12 (VSS_27), U1.L3 (VSS_28), U1.L7 (VSS_29), U1.L12 (VSS_30), U1.M7 (VSS_31), U1.M8 (VSS_32), U1.M9 (VSS_33), U1.M10 (VSS_34), U1.M11 (VSS_35), U1.M12 (NGND_KEL0), U1.N3 (VSS_36), U1.N5 (VSS_37), U1.R3 (VSS_38), U1.R5 (VSS_39), U1.R7 (VSS_40), U1.R11 (VSS_41), U1.R16 (VSS_42), U1.R17 (VSS_43), U1.T14 (VSS_44), U1.U1 (VSS_45), U1.U14 (VSS_46), U1.U17 (VSS_47)
NVCC_PLL: C20.1, C24.1, U1.P13 (NVCC_PLL)
P1V4_SOC: C4.1, C7.1, C10.1, C12.1, U1.H9 (VDD_SOC_IN_1), U1.H10 (VDD_SOC_IN_2), U1.J9 (VDD_SOC_IN_3), U1.J10 (VDD_SOC_IN_4), U1.K9 (VDD_SOC_IN_5), U1.K10 (VDD_SOC_IN_6)
P1V35_DRAM: C1.1, C2.1, C3.1, C5.1, C8.1, C11.1, C13.1, U1.G6 (NVCC_DRAM_1), U1.H6 (NVCC_DRAM_2), U1.J6 (NVCC_DRAM_3), U1.K6 (NVCC_DRAM_4), U1.L6 (NVCC_DRAM_5), U1.M6 (NVCC_DRAM_6)
P3V3: C6.1, C9.1, C33.1, C34.1, U1.L13 (VDDA_ADC_3P3), U1.M13 (ADC_VREFH), U1.N13 (VDD_HIGH_IN)
P3V3_SNVS: C14.1, U1.P12 (VDD_SNVS_IN)
VDD_ARM_CAP: C15.1, C18.1, C21.1, U1.G9 (VDD_ARM_CAP_1), U1.G10 (VDD_ARM_CAP_2), U1.G11 (VDD_ARM_CAP_3), U1.H11 (VDD_ARM_CAP_4)
VDD_HIGH_CAP: C23.1, C26.1, C148.1, U1.N6 (NVCC_DRAM_2P5), U1.R14 (VDD_HIGH_CAP_1), U1.R15 (VDD_HIGH_CAP_2)
VDD_SNVS_CAP: C17.1, U1.N12 (VDD_SNVS_CAP)
VDD_SOC_CAP: C16.1, C19.1, C22.1, C25.1, U1.G8 (VDD_SOC_CAP_1), U1.H8 (VDD_SOC_CAP_2), U1.J8 (VDD_SOC_CAP_3), U1.J11 (VDD_SOC_CAP_4), U1.K8 (VDD_SOC_CAP_5), U1.K11 (VDD_SOC_CAP_6), U1.L8 (VDD_SOC_CAP_7), U1.L9 (VDD_SOC_CAP_8), U1.L10 (VDD_SOC_CAP_9), U1.L11 (VDD_SOC_CAP_10)

Notes on the sheet:
i.MX 6ULL PMU block diagram IMX6ULLRM rev. 1
i.MX6 - Power
