a1wolfe/iMX6-BareBones/Kicad/iMX6_Storage.kicad_sch

## KiCad design Kicad/iMX6_Storage.kicad_sch (2026-04-23)

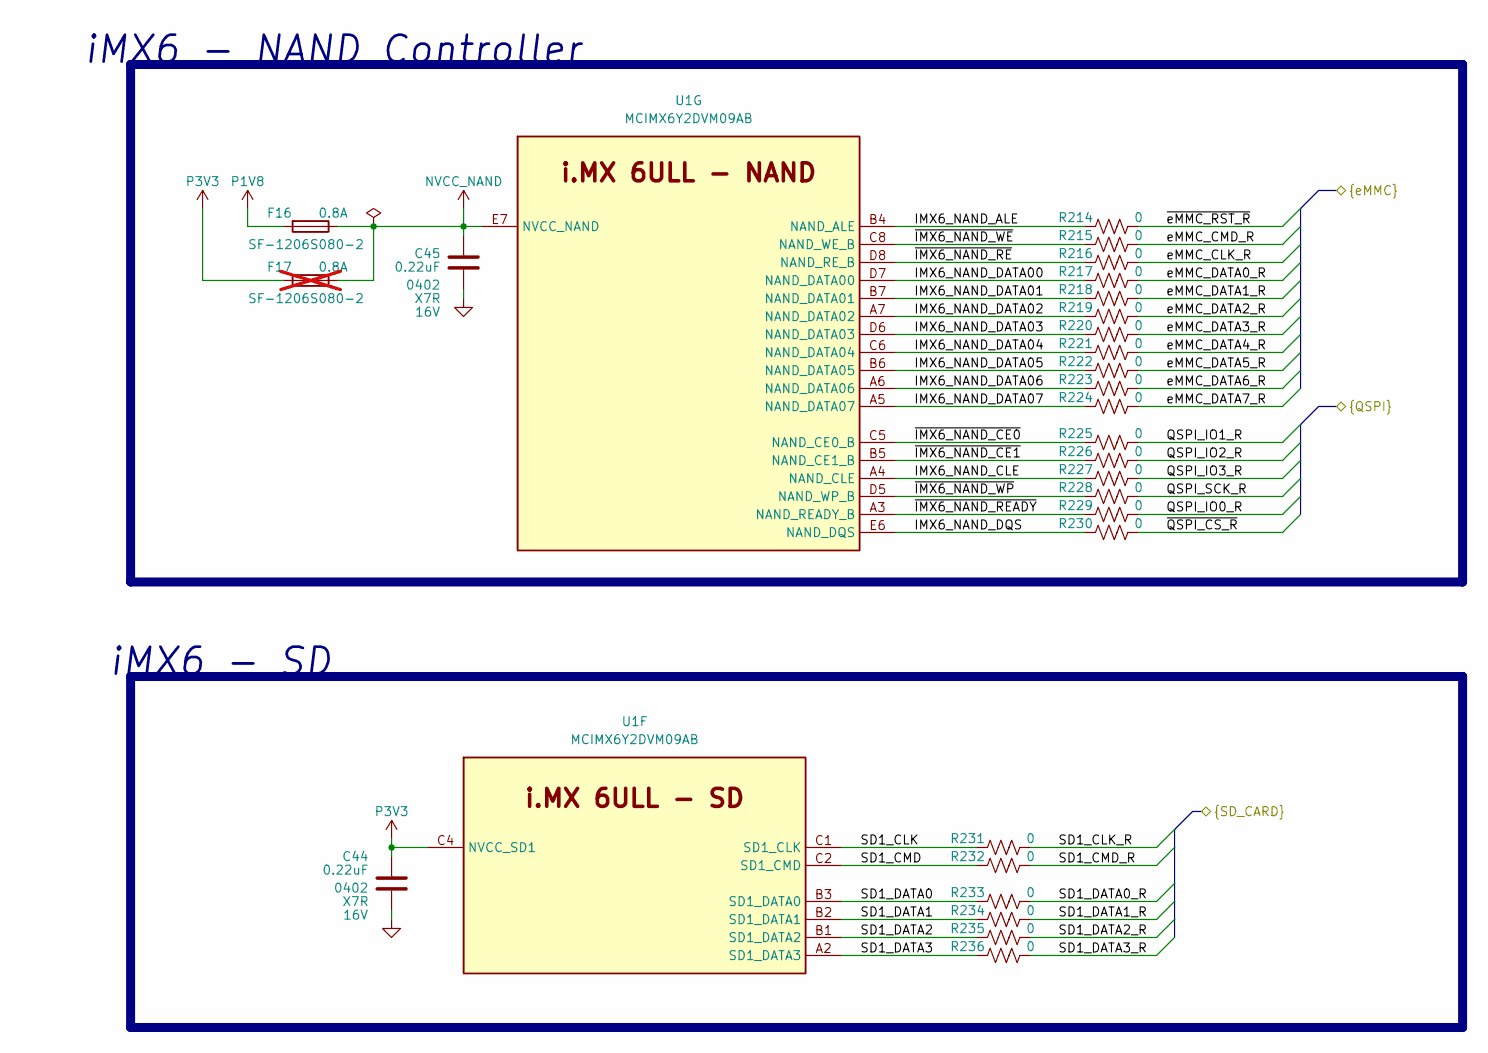
[picture p79: schematic iMX6_Storage.kicad_sch]

Parts:
C44, C45: 0.22uF; C_0402_1005Metric; Tolerance 10%; Voltage 16V; MPN GRM155R71C224KA12
F16: SF-1206S080-2; Fuse_1206_3216Metric; Current Rating 0.8A; MPN SF-1206S080-2
F17: SF-1206S080-2; Fuse_1206_3216Metric; Current Rating 0.8A; MPN SF-1206S080-2; not fitted
R214, R215, R216, R217, R218, R219, R220, R221, R222, R223, R224, R225, R226, R227, R228, R229, R230, R231, R232, R233, R234, R235, R236: 0; R_0402_1005Metric; Tolerance Jumper; MPN RC0402JR-070RL
U1: MCIMX6Y2DVM09AB; imx6ull_BGA289C80P17X17_1400X1400X132; MPN MCIMX6Y2DVM09AB

Connections:
GND: C44.1, C45.1
IMX6_NAND_ALE: R214.1, U1.B4 (NAND_ALE)
IMX6_NAND_CLE: R227.1, U1.A4 (NAND_CLE)
IMX6_NAND_DATA00: R217.1, U1.D7 (NAND_DATA00)
IMX6_NAND_DATA01: R218.1, U1.B7 (NAND_DATA01)
IMX6_NAND_DATA02: R219.1, U1.A7 (NAND_DATA02)
IMX6_NAND_DATA03: R220.1, U1.D6 (NAND_DATA03)
IMX6_NAND_DATA04: R221.1, U1.C6 (NAND_DATA04)
IMX6_NAND_DATA05: R222.1, U1.B6 (NAND_DATA05)
IMX6_NAND_DATA06: R223.1, U1.A6 (NAND_DATA06)
IMX6_NAND_DATA07: R224.1, U1.A5 (NAND_DATA07)
IMX6_NAND_DQS: R230.1, U1.E6 (NAND_DQS)
NVCC_NAND: C45.2, F16.1, F17.1, U1.E7 (NVCC_NAND)
P1V8: F16.2
P3V3: C44.2, F17.2, U1.C4 (NVCC_SD1)
QSPI_IO0_R: R229.2
QSPI_IO1_R: R225.2
QSPI_IO2_R: R226.2
QSPI_IO3_R: R227.2
QSPI_SCK_R: R228.2
SD1_CLK: R231.1, U1.C1 (SD1_CLK)
SD1_CLK_R: R231.2
SD1_CMD: R232.1, U1.C2 (SD1_CMD)
SD1_CMD_R: R232.2
SD1_DATA0: R233.1, U1.B3 (SD1_DATA0)
SD1_DATA0_R: R233.2
SD1_DATA1: R234.1, U1.B2 (SD1_DATA1)
SD1_DATA1_R: R234.2
SD1_DATA2: R235.1, U1.B1 (SD1_DATA2)
SD1_DATA2_R: R235.2
SD1_DATA3: R236.1, U1.A2 (SD1_DATA3)
SD1_DATA3_R: R236.2
eMMC_CLK_R: R216.2
eMMC_CMD_R: R215.2
eMMC_DATA0_R: R217.2
eMMC_DATA1_R: R218.2
eMMC_DATA2_R: R219.2
eMMC_DATA3_R: R220.2
eMMC_DATA4_R: R221.2
eMMC_DATA5_R: R222.2
eMMC_DATA6_R: R223.2
eMMC_DATA7_R: R224.2
~IMX6_NAND_CE0: R225.1, U1.C5 (NAND_CE0_B)
~IMX6_NAND_CE1: R226.1, U1.B5 (NAND_CE1_B)
~IMX6_NAND_READY: R229.1, U1.A3 (NAND_READY_B)
~IMX6_NAND_RE: R216.1, U1.D8 (NAND_RE_B)
~IMX6_NAND_WE: R215.1, U1.C8 (NAND_WE_B)
~IMX6_NAND_WP: R228.1, U1.D5 (NAND_WP_B)
~QSPI_CS_R: R230.2
~eMMC_RST_R: R214.2

Notes on the sheet:
iMX6 - NAND Controller
iMX6 - SD
